tristanseifert/68komputer-hw/cpu-68000/sound.brd

## EAGLE design cpu-68000/sound.brd (2020-02-12)

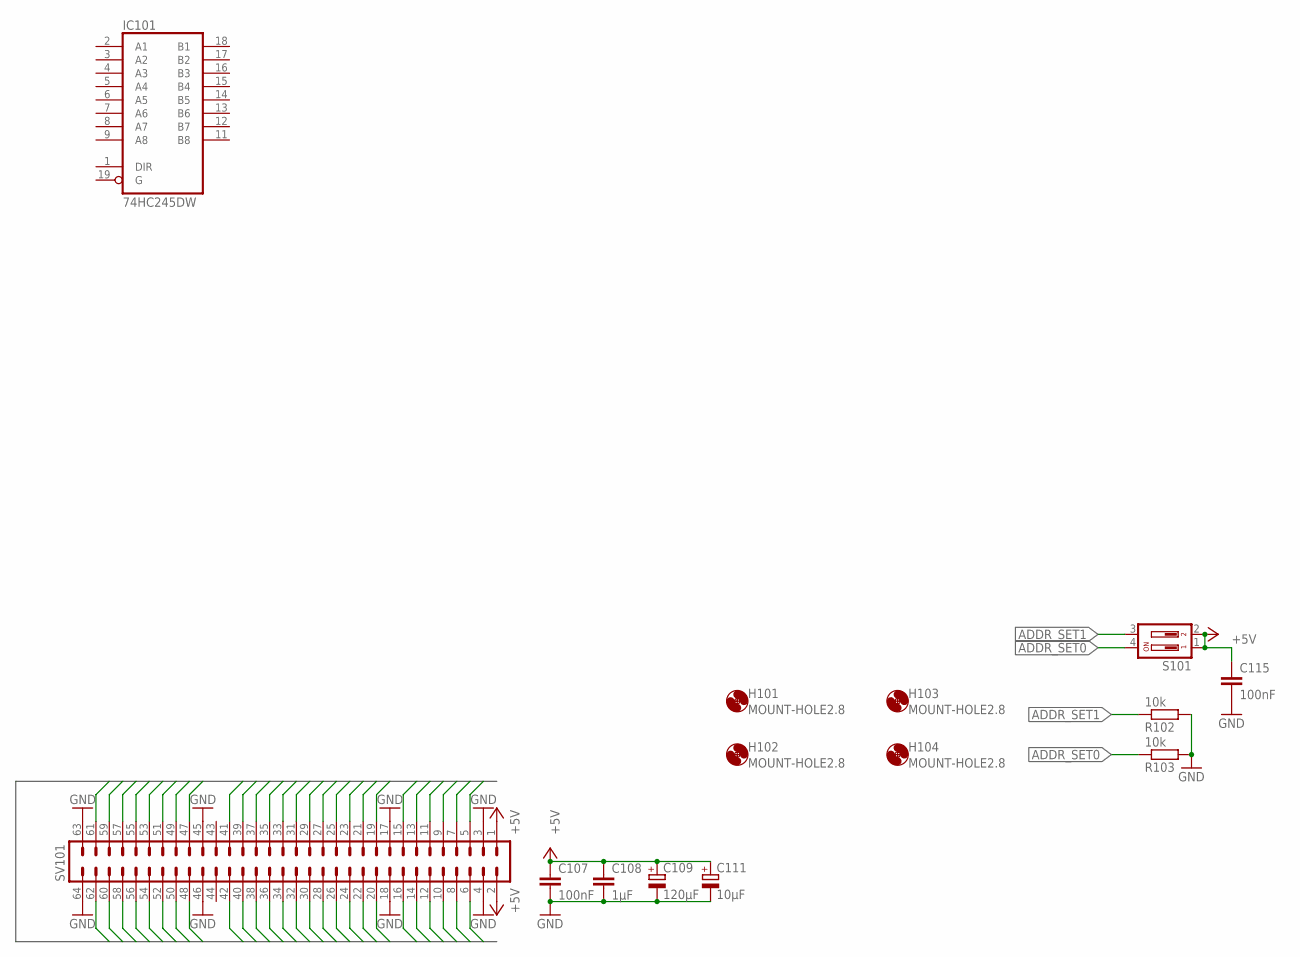
[picture p32: schematic sound.sch, sheet 1, Interface, Address Decoding]

Parts:
C107, C115: 100nF; C0805; MOUSER 710-885012207072
C108: 1µF; C0805; MOUSER 710-885012207078
C109: 120µF; E2,5-7; MOUSER 710-860020373007
C111: 10µF; SMC_B; MOUSER 581-TAJB106K020RNJV
H101, H102, H103, H104: MOUNT-HOLE2.8; 2,8
IC101: 74HC245DW; SO20W; MOUSER 595-SN74HC245DWR
R102, R103: 10k; R2012; MOUSER 652-CR0805FX-1002ELF
S101: DP02; DP-02
SV101: ML64L

Connections:
!AS: SV101.13
!BG: SV101.9
!BGACK: SV101.8
!BR: SV101.7
!DTACK: SV101.10
!EXTI_A: SV101.16
!EXTI_B: SV101.15
!EXT_ID: SV101.41
!HALT: SV101.5
!LDS: SV101.11
!RESET: SV101.6
!UDS: SV101.14
+5V: C107.1, C108.1, C109.+, C111.+, C115.1, S101.1, S101.2, SV101.1, SV101.2; also elsewhere on the board
A1: SV101.20
A2: SV101.22
A3: SV101.19
A4: SV101.24
A5: SV101.21
A6: SV101.23
A7: SV101.26
A8: SV101.25
A9: SV101.28
A10: SV101.27
A11: SV101.30
A12: SV101.29
A13: SV101.31
A14: SV101.32
A15: SV101.33
A16: SV101.34
A17: SV101.36
A18: SV101.35
A19: SV101.38
A20: SV101.37
A21: SV101.40
A22: SV101.39
A23: SV101.42
ADDR_SET0: R103.1, S101.4
ADDR_SET1: R102.1, S101.3
D0: SV101.62
D1: SV101.60
D2: SV101.58
D3: SV101.56
D4: SV101.54
D5: SV101.52
D6: SV101.50
D7: SV101.48
D8: SV101.57
D9: SV101.59
D10: SV101.61
D11: SV101.55
D12: SV101.53
D13: SV101.51
D14: SV101.49
D15: SV101.47
GND: C107.2, C108.2, C109.-, C111.-, C115.2, IC101.10 (GND), R102.2, R103.2, SV101.3, SV101.4, SV101.17, SV101.18, SV101.45, SV101.46, SV101.63, SV101.64; also elsewhere on the board
R/!W!: SV101.12
VCC: IC101.20 (VCC)

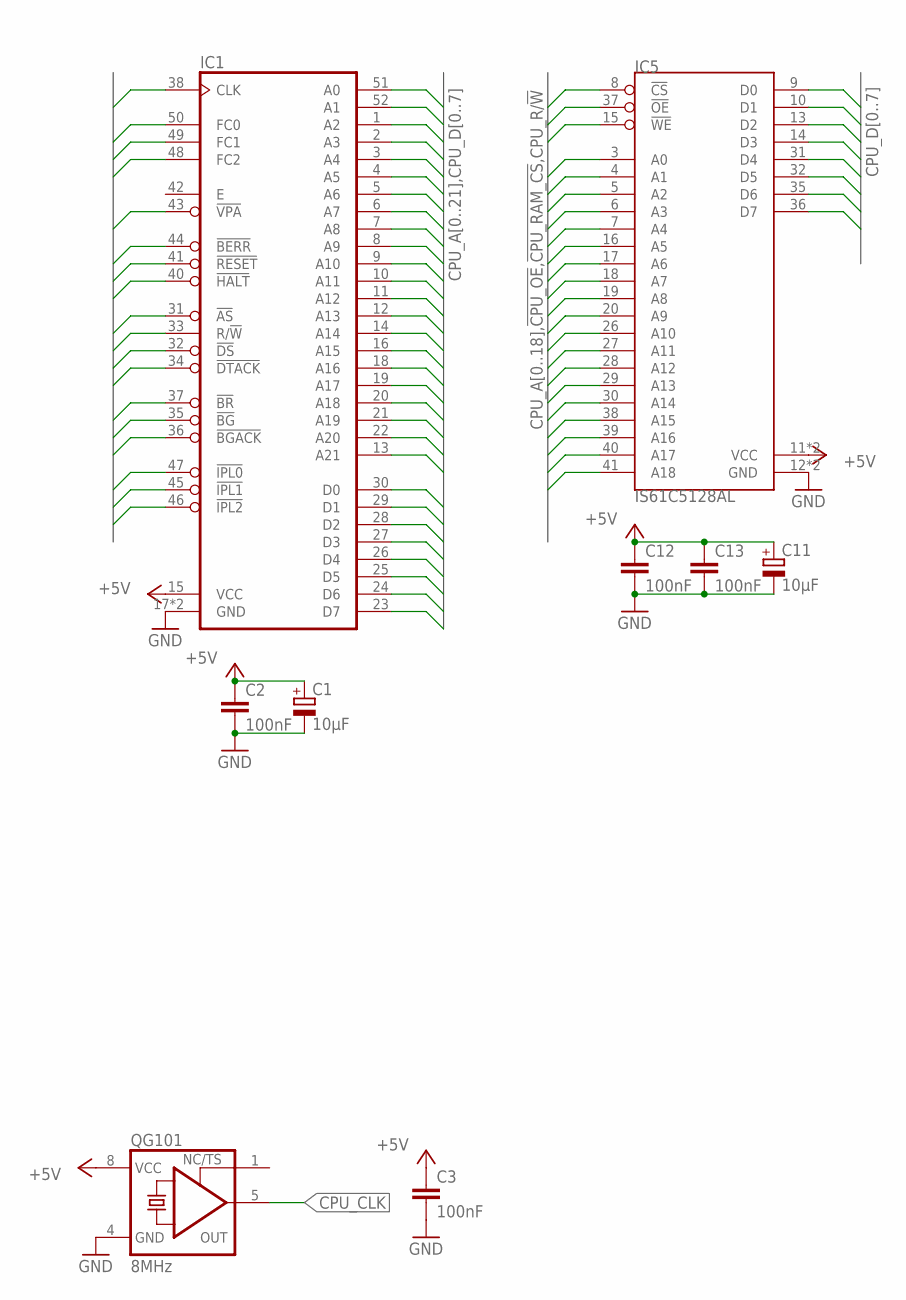
[picture p33: schematic sound.sch, sheet 2, Sound CPU]

Parts:
C1, C11: 10µF; SMC_B; MOUSER 581-TAJB106K020RNJV
C2, C3, C12, C13: 100nF; C0805; MOUSER 710-885012207072
IC1: MC68008-PLCCPLCC52-SOCKET; PLCC52-S
IC5: IS61C5128AL; TSOP44-II
QG101: 8MHz; DIL08S; MOUSER 774-MXO45HS-3C-8.0

Connections:
!CPU_AS: IC1.31 (!AS)
!CPU_BERR: IC1.44 (!BERR)
!CPU_BG: IC1.35 (!BG); also elsewhere on the board
!CPU_BGACK: IC1.36 (!BGACK)
!CPU_BR: IC1.37 (!BR); also elsewhere on the board
!CPU_DS: IC1.32 (!DS)
!CPU_DTACK: IC1.34 (!DTACK)
!CPU_HALT: IC1.40 (!HALT); also elsewhere on the board
!CPU_IPL0: IC1.47 (!IPL0)
!CPU_IPL1: IC1.45 (!IPL1)
!CPU_IPL2: IC1.46 (!IPL2)
!CPU_OE: IC5.37 (!OE)
!CPU_RAM_CS: IC5.8 (!CS)
!CPU_RESET: IC1.41 (!RESET); also elsewhere on the board
!CPU_VPA: IC1.43 (!VPA)
+5V: C1.+, C2.1, C3.1, C11.+, C12.1, C13.1, IC1.15 (VCC), IC5.11 (VCC), IC5.33 (VCC), QG101.8 (VCC); also elsewhere on the board
CPU_A0: IC1.51 (A0), IC5.3 (A0); also elsewhere on the board
CPU_A1: IC1.52 (A1), IC5.4 (A1); also elsewhere on the board
CPU_A2: IC1.1 (A2), IC5.5 (A2); also elsewhere on the board
CPU_A3: IC1.2 (A3), IC5.6 (A3)
CPU_A4: IC1.3 (A4), IC5.7 (A4)
CPU_A5: IC1.4 (A5), IC5.16 (A5)
CPU_A6: IC1.5 (A6), IC5.17 (A6)
CPU_A7: IC1.6 (A7), IC5.18 (A7)
CPU_A8: IC1.7 (A8), IC5.19 (A8)
CPU_A9: IC1.8 (A9), IC5.20 (A9)
CPU_A10: IC1.9 (A10), IC5.26 (A10)
CPU_A11: IC1.10 (A11), IC5.27 (A11)
CPU_A12: IC1.11 (A12), IC5.28 (A12)
CPU_A13: IC1.12 (A13), IC5.29 (A13)
CPU_A14: IC1.14 (A14), IC5.30 (A14)
CPU_A15: IC1.16 (A15), IC5.38 (A15)
CPU_A16: IC1.18 (A16), IC5.39 (A16)
CPU_A17: IC1.19 (A17), IC5.40 (A17)
CPU_A18: IC1.20 (A18), IC5.41 (A18)
CPU_A19: IC1.21 (A19)
CPU_A20: IC1.22 (A20)
CPU_A21: IC1.13 (A21)
CPU_CLK: IC1.38 (CLK), QG101.5 (OUT)
CPU_D0: IC1.30 (D0), IC5.9 (D0); also elsewhere on the board
CPU_D1: IC1.29 (D1), IC5.10 (D1); also elsewhere on the board
CPU_D2: IC1.28 (D2), IC5.13 (D2); also elsewhere on the board
CPU_D3: IC1.27 (D3), IC5.14 (D3); also elsewhere on the board
CPU_D4: IC1.26 (D4), IC5.31 (D4); also elsewhere on the board
CPU_D5: IC1.25 (D5), IC5.32 (D5); also elsewhere on the board
CPU_D6: IC1.24 (D6), IC5.35 (D6); also elsewhere on the board
CPU_D7: IC1.23 (D7), IC5.36 (D7); also elsewhere on the board
CPU_FC0: IC1.50 (FC0)
CPU_FC1: IC1.49 (FC1)
CPU_FC2: IC1.48 (FC2)
CPU_R/!W!: IC1.33 (R/!W), IC5.15 (!WE); also elsewhere on the board
GND: C1.-, C2.2, C3.2, C11.-, C12.2, C13.2, IC1.17 (GND), IC1.39 (GND), IC5.12 (GND), IC5.34 (GND), QG101.4 (GND); also elsewhere on the board

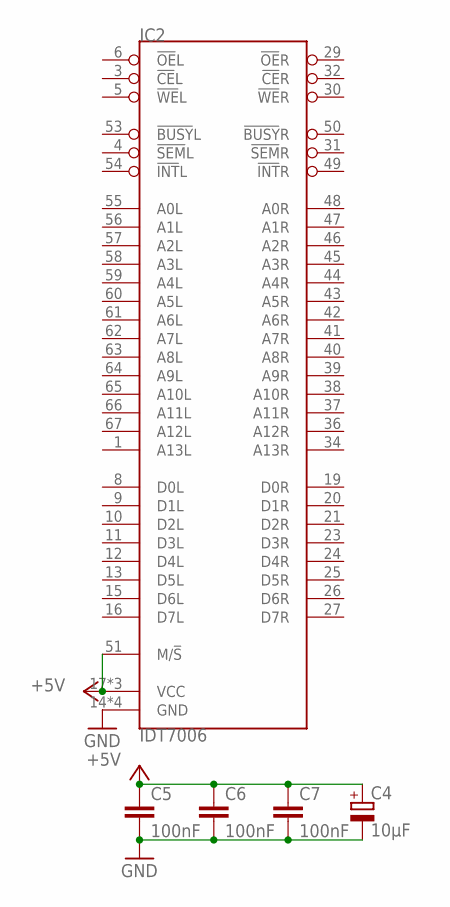
[picture p34: schematic sound.sch, sheet 4, Sound CPU / Host IF]

Parts:
C4: 10µF; SMC_B; MOUSER 581-TAJB106K020RNJV
C5, C6, C7: 100nF; C0805; MOUSER 710-885012207072
IC2: IDT7006; PLCC68-S

Connections:
+5V: C4.+, C5.1, C6.1, C7.1, IC2.17 (VCC), IC2.22 (VCC), IC2.51 (M/!S!), IC2.68 (VCC); also elsewhere on the board
GND: C4.-, C5.2, C6.2, C7.2, IC2.14 (GND), IC2.18 (GND), IC2.35 (GND), IC2.52 (GND); also elsewhere on the board

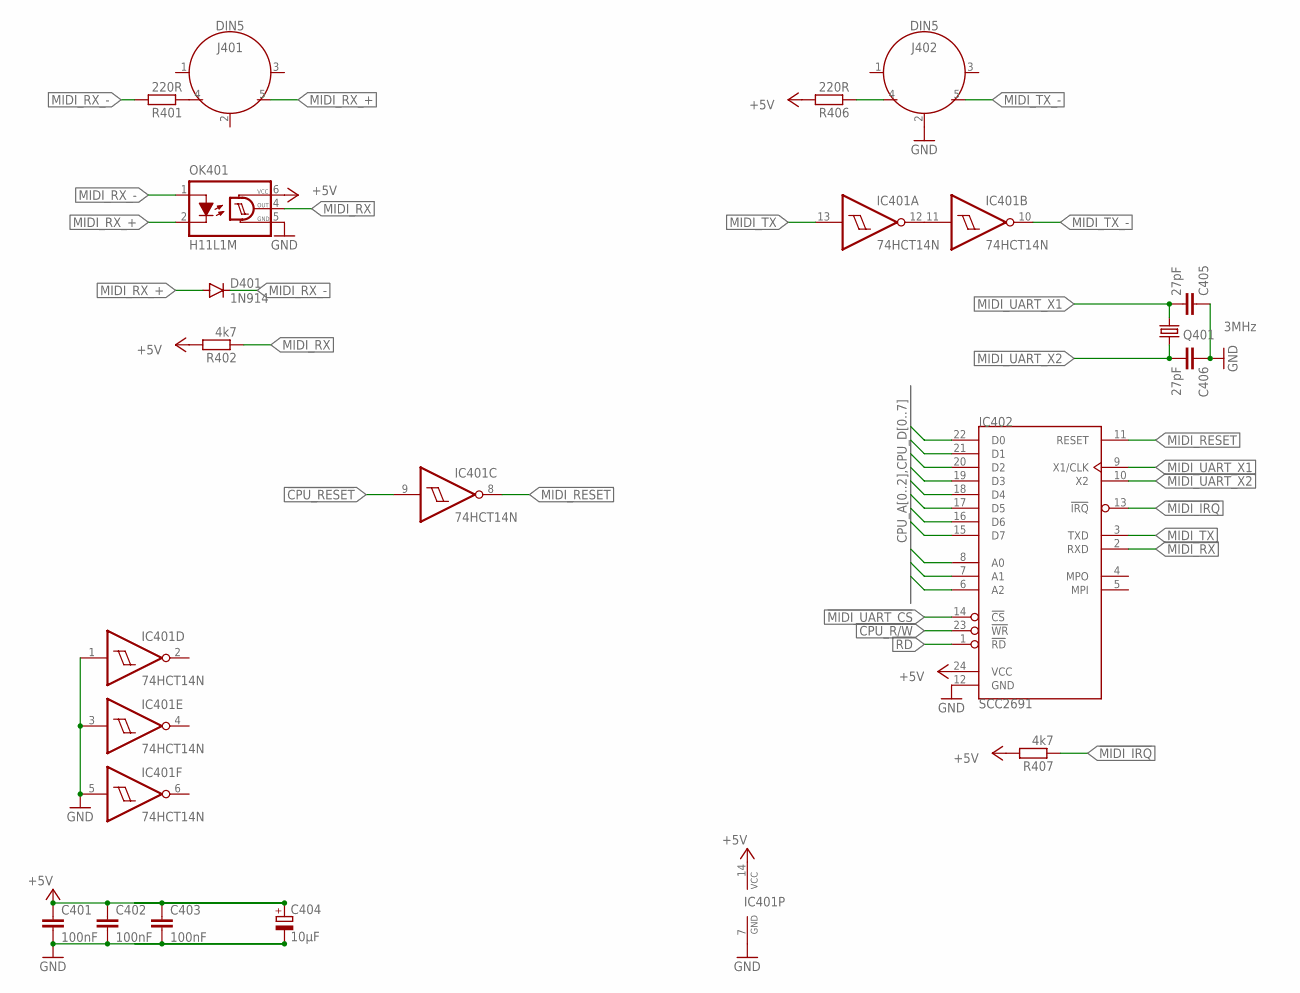
[picture p35: schematic sound.sch, sheet 7, MIDI IF]

Parts:
C401, C402, C403: 100nF; C0805; MOUSER 710-885012207072
C404: 10µF; SMC_B; MOUSER 581-TAJB106K020RNJV
C405, C406: 27pF; C0805; MOUSER 80-C0805C270K5HACTU
D401: 1N914; DO35-10; MOUSER 512-1N914TR
IC401: 74HCT14N; DIL14; MOUSER 595-SN74HCT14N
IC402: SCC2691; DIL24S; MOUSER_SOCKET 575-11044324
J401, J402: DIN5; DIN5-RA-PTH; MOUSER 806-KCDX-5S-N
OK401: H11L1M; DIL06; MOUSER 512-H11L1M
Q401: 3MHz; HC49/S; MOUSER 520-HCA300-SX
R401, R406: 220R; R2012; MOUSER 652-CR0805FX-2200ELF
R402, R407: 4k7; R2012; MOUSER 652-CR0805FX-4701ELF

Connections:
!CPU_RESET: IC401.9 (I); also elsewhere on the board
!MIDI_IRQ: IC402.13 (!IRQ), R407.1; also elsewhere on the board
!MIDI_UART_CS: IC402.14 (!CS)
!RD: IC402.1 (!RD)
+5V: C401.1, C402.1, C403.1, C404.+, IC401.14 (VCC), IC402.24 (VCC), OK401.6 (VCC), R402.2, R406.2, R407.2; also elsewhere on the board
CPU_A0: IC402.8 (A0); also elsewhere on the board
CPU_A1: IC402.7 (A1); also elsewhere on the board
CPU_A2: IC402.6 (A2); also elsewhere on the board
CPU_D0: IC402.22 (D0); also elsewhere on the board
CPU_D1: IC402.21 (D1); also elsewhere on the board
CPU_D2: IC402.20 (D2); also elsewhere on the board
CPU_D3: IC402.19 (D3); also elsewhere on the board
CPU_D4: IC402.18 (D4); also elsewhere on the board
CPU_D5: IC402.17 (D5); also elsewhere on the board
CPU_D6: IC402.16 (D6); also elsewhere on the board
CPU_D7: IC402.15 (D7); also elsewhere on the board
CPU_R/!W!: IC402.23 (!WR); also elsewhere on the board
GND: C401.2, C402.2, C403.2, C404.-, C405.1, C406.1, IC401.1 (I), IC401.3 (I), IC401.5 (I), IC401.7 (GND), IC402.12 (GND), J402.2, OK401.5 (GND); also elsewhere on the board
MIDI_RESET: IC401.8 (O), IC402.11 (RESET)
MIDI_RX: IC402.2 (RXD), OK401.4 (OUT), R402.1; also elsewhere on the board
MIDI_RX_+: D401.A, J401.5, OK401.2 (C)
MIDI_RX_-: D401.C, OK401.1 (A), R401.2
MIDI_TX: IC401.13 (I), IC402.3 (TXD); also elsewhere on the board
MIDI_TX_-: IC401.10 (O), J402.5
MIDI_UART_X1: C405.2, IC402.9 (X1/CLK), Q401.1
MIDI_UART_X2: C406.2, IC402.10 (X2), Q401.2
unnamed: J401.4, R401.1
unnamed: IC401.11 (I), IC401.12 (O)
unnamed: J402.4, R406.1

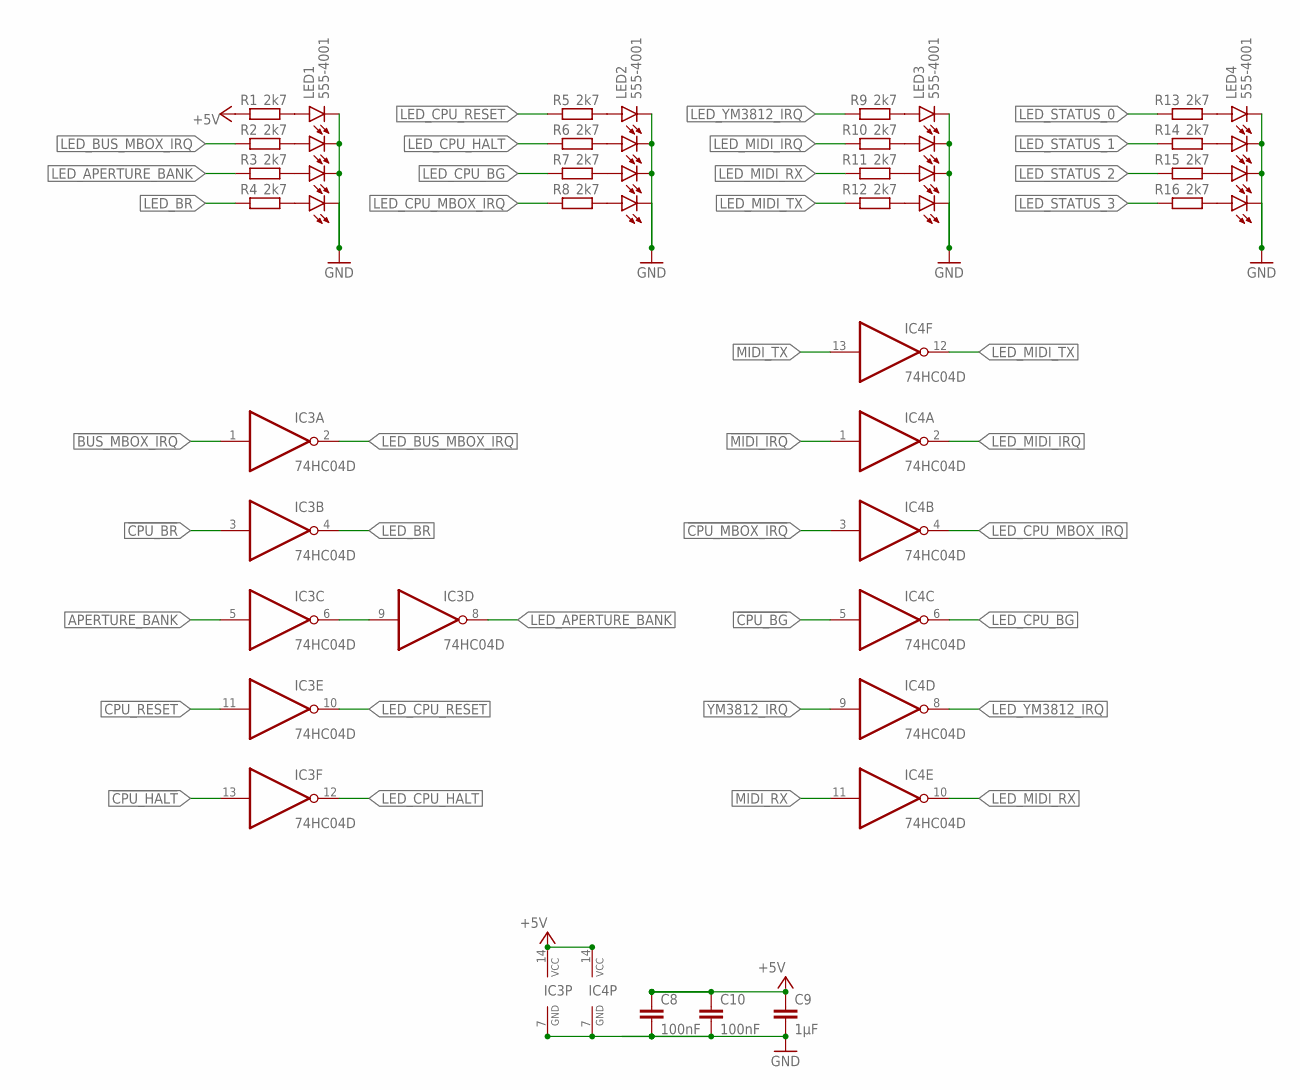
[picture p36: schematic sound.sch, sheet 8, Blinkenlights]

Parts:
C8, C10: 100nF; C0805; MOUSER 710-885012207072
C9: 1µF; C0805; MOUSER 710-885012207078
IC3, IC4: 74HC04D; SO14
LED1, LED2, LED3, LED4: 555-4001
R1, R2, R3, R4, R5, R6, R7, R8, R9, R10, R11, R12, R13, R14, R15, R16: 2k7; R2012; MOUSER 652-CR0805FX-2701ELF

Connections:
!BUS_MBOX_IRQ: IC3.1 (I)
!CPU_BG: IC4.5 (I); also elsewhere on the board
!CPU_BR: IC3.3 (I); also elsewhere on the board
!CPU_HALT: IC3.13 (I); also elsewhere on the board
!CPU_MBOX_IRQ: IC4.3 (I)
!CPU_RESET: IC3.11 (I); also elsewhere on the board
!MIDI_IRQ: IC4.1 (I); also elsewhere on the board
!YM3812_IRQ: IC4.9 (I)
+5V: C8.1, C9.1, C10.1, IC3.14 (VCC), IC4.14 (VCC), R1.2; also elsewhere on the board
APERTURE_BANK: IC3.5 (I)
GND: C8.2, C9.2, C10.2, IC3.7 (GND), IC4.7 (GND), LED1.K1, LED1.K2, LED1.K3, LED1.K4, LED2.K1, LED2.K2, LED2.K3, LED2.K4, LED3.K1, LED3.K2, LED3.K3, LED3.K4, LED4.K1, LED4.K2, LED4.K3, LED4.K4; also elsewhere on the board
LED_APERTURE_BANK: IC3.8 (O), R3.2
LED_BR: IC3.4 (O), R4.2
LED_BUS_MBOX_IRQ: IC3.2 (O), R2.2
LED_CPU_BG: IC4.6 (O), R7.2
LED_CPU_HALT: IC3.12 (O), R6.2
LED_CPU_MBOX_IRQ: IC4.4 (O), R8.2
LED_CPU_RESET: IC3.10 (O), R5.2
LED_MIDI_IRQ: IC4.2 (O), R10.2
LED_MIDI_RX: IC4.10 (O), R11.2
LED_MIDI_TX: IC4.12 (O), R12.2
LED_STATUS_0: R13.2
LED_STATUS_1: R14.2
LED_STATUS_2: R15.2
LED_STATUS_3: R16.2
LED_YM3812_IRQ: IC4.8 (O), R9.2
MIDI_RX: IC4.11 (I); also elsewhere on the board
MIDI_TX: IC4.13 (I); also elsewhere on the board
unnamed: LED1.A4, R1.1
unnamed: LED1.A3, R2.1
unnamed: LED1.A2, R3.1
unnamed: LED1.A1, R4.1
unnamed: LED2.A4, R5.1
unnamed: LED2.A3, R6.1
unnamed: IC3.6 (O), IC3.9 (I)
unnamed: LED2.A2, R7.1
unnamed: LED2.A1, R8.1
unnamed: LED3.A4, R9.1
unnamed: LED3.A3, R10.1
unnamed: LED3.A2, R11.1
unnamed: LED3.A1, R12.1
unnamed: LED4.A4, R13.1
unnamed: LED4.A3, R14.1
unnamed: LED4.A2, R15.1
unnamed: LED4.A1, R16.1

Board: 2 copper layers, 70 parts (3 on the bottom side), 77 nets, no tracks yet.
