tristanseifert/68komputer-hw/cpu-68000/cpu-68000.brd

## EAGLE design cpu-68000/cpu-68000.brd (2019-11-22)

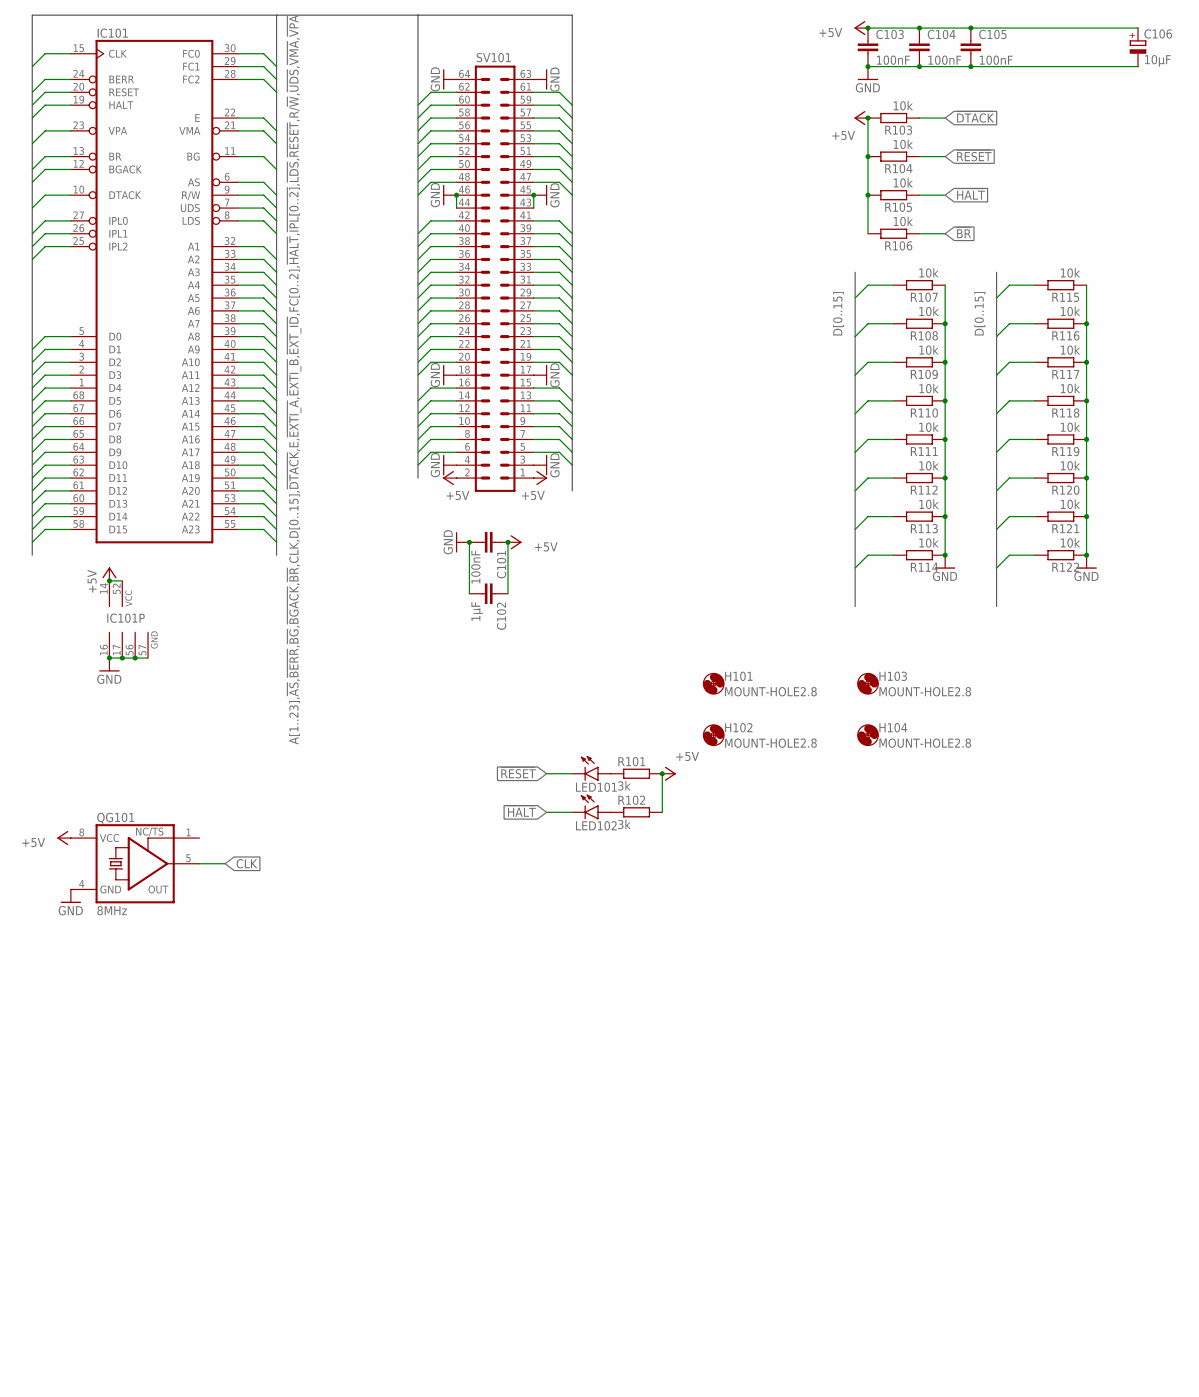
[picture p37: schematic cpu-68000.sch, sheet 1, CPU]

Parts:
C101, C103, C104, C105: 100nF; C0805; MOUSER 710-885012207072
C102: 1µF; C0805; MOUSER 710-885012207078
C106: 10µF; SMC_B; MOUSER 581-TAJB106K020RNJV
H101, H102, H103, H104: MOUNT-HOLE2.8; 2,8
IC101: MC68000FN-SOC; PLCC68SOCK; MOUSER_SOCKET 940-44-068-24-000000
LED101, LED102: LEDCHIPLED_1206; CHIPLED_1206; MOUSER 710-156120RS75300
QG101: 8MHz; DIL08S; MOUSER 774-MXO45HS-3C-8.0
R101, R102: 3k; R2012; MOUSER 652-CR0805JW-302ELF
R103, R104, R105, R106, R107, R108, R109, R110, R111, R112, R113, R114, R115, R116, R117, R118, R119, R120, R121, R122: 10k; R2012; MOUSER 652-CR0805FX-1002ELF
SV101: ML64L

Connections:
!AS: IC101.6 (AS), SV101.13; also elsewhere on the board
!BERR: IC101.24 (BERR); also elsewhere on the board
!BG: IC101.11 (BG), SV101.9
!BGACK: IC101.12 (BGACK), SV101.8
!BR: IC101.13 (BR), R106.1, SV101.7
!DTACK: IC101.10 (DTACK), R103.1, SV101.10; also elsewhere on the board
!EXTI_A: SV101.16; also elsewhere on the board
!EXTI_B: SV101.15; also elsewhere on the board
!EXT_ID: SV101.41; also elsewhere on the board
!HALT: IC101.19 (HALT), LED102.C, R105.1, SV101.5; also elsewhere on the board
!IPL0: IC101.27 (IPL0); also elsewhere on the board
!IPL1: IC101.26 (IPL1); also elsewhere on the board
!IPL2: IC101.25 (IPL2); also elsewhere on the board
!LDS: IC101.8 (LDS), SV101.11; also elsewhere on the board
!RESET: IC101.20 (RESET), LED101.C, R104.1, SV101.6; also elsewhere on the board
!UDS: IC101.7 (UDS), SV101.14; also elsewhere on the board
!VMA: IC101.21 (VMA)
!VPA: IC101.23 (VPA); also elsewhere on the board
+5V: C101.1, C102.1, C103.1, C104.1, C105.1, C106.+, IC101.14 (VCC), IC101.52 (VCC), QG101.8 (VCC), R101.2, R102.2, R103.2, R104.2, R105.2, R106.2, SV101.1, SV101.2; also elsewhere on the board
A1: IC101.32 (A1), SV101.20; also elsewhere on the board
A2: IC101.33 (A2), SV101.22; also elsewhere on the board
A3: IC101.34 (A3), SV101.19; also elsewhere on the board
A4: IC101.35 (A4), SV101.24; also elsewhere on the board
A5: IC101.36 (A5), SV101.21; also elsewhere on the board
A6: IC101.37 (A6), SV101.23; also elsewhere on the board
A7: IC101.38 (A7), SV101.26; also elsewhere on the board
A8: IC101.39 (A8), SV101.25; also elsewhere on the board
A9: IC101.40 (A9), SV101.28; also elsewhere on the board
A10: IC101.41 (A10), SV101.27; also elsewhere on the board
A11: IC101.42 (A11), SV101.30; also elsewhere on the board
A12: IC101.43 (A12), SV101.29; also elsewhere on the board
A13: IC101.44 (A13), SV101.31; also elsewhere on the board
A14: IC101.45 (A14), SV101.32; also elsewhere on the board
A15: IC101.46 (A15), SV101.33; also elsewhere on the board
A16: IC101.47 (A16), SV101.34; also elsewhere on the board
A17: IC101.48 (A17), SV101.36; also elsewhere on the board
A18: IC101.49 (A18), SV101.35; also elsewhere on the board
A19: IC101.50 (A19), SV101.38; also elsewhere on the board
A20: IC101.51 (A20), SV101.37; also elsewhere on the board
A21: IC101.53 (A21), SV101.40; also elsewhere on the board
A22: IC101.54 (A22), SV101.39; also elsewhere on the board
A23: IC101.55 (A23), SV101.42; also elsewhere on the board
CLK: IC101.15 (CLK), QG101.5 (OUT); also elsewhere on the board
D0: IC101.5 (D0), R107.2, SV101.62; also elsewhere on the board
D1: IC101.4 (D1), R108.2, SV101.60; also elsewhere on the board
D2: IC101.3 (D2), R109.2, SV101.58; also elsewhere on the board
D3: IC101.2 (D3), R110.2, SV101.56; also elsewhere on the board
D4: IC101.1 (D4), R111.2, SV101.54; also elsewhere on the board
D5: IC101.68 (D5), R112.2, SV101.52; also elsewhere on the board
D6: IC101.67 (D6), R113.2, SV101.50; also elsewhere on the board
D7: IC101.66 (D7), R114.2, SV101.48; also elsewhere on the board
D8: IC101.65 (D8), R115.2, SV101.57; also elsewhere on the board
D9: IC101.64 (D9), R116.2, SV101.59; also elsewhere on the board
D10: IC101.63 (D10), R117.2, SV101.61; also elsewhere on the board
D11: IC101.62 (D11), R118.2, SV101.55; also elsewhere on the board
D12: IC101.61 (D12), R119.2, SV101.53; also elsewhere on the board
D13: IC101.60 (D13), R120.2, SV101.51; also elsewhere on the board
D14: IC101.59 (D14), R121.2, SV101.49; also elsewhere on the board
D15: IC101.58 (D15), R122.2, SV101.47; also elsewhere on the board
E: IC101.22 (E); also elsewhere on the board
FC0: IC101.30 (FC0); also elsewhere on the board
FC1: IC101.29 (FC1); also elsewhere on the board
FC2: IC101.28 (FC2); also elsewhere on the board
GND: C101.2, C102.2, C103.2, C104.2, C105.2, C106.-, IC101.16 (GND), IC101.17 (GND), IC101.56 (GND), IC101.57 (GND), QG101.4 (GND), R107.1, R108.1, R109.1, R110.1, R111.1, R112.1, R113.1, R114.1, R115.1, R116.1, R117.1, R118.1, R119.1, R120.1, R121.1, R122.1, SV101.3, SV101.4, SV101.17, SV101.18, SV101.43, SV101.44, SV101.45, SV101.46, SV101.63, SV101.64; also elsewhere on the board
unnamed: LED101.A, R101.1
unnamed: LED102.A, R102.1
R/!W!: IC101.9 (R/W), SV101.12; also elsewhere on the board

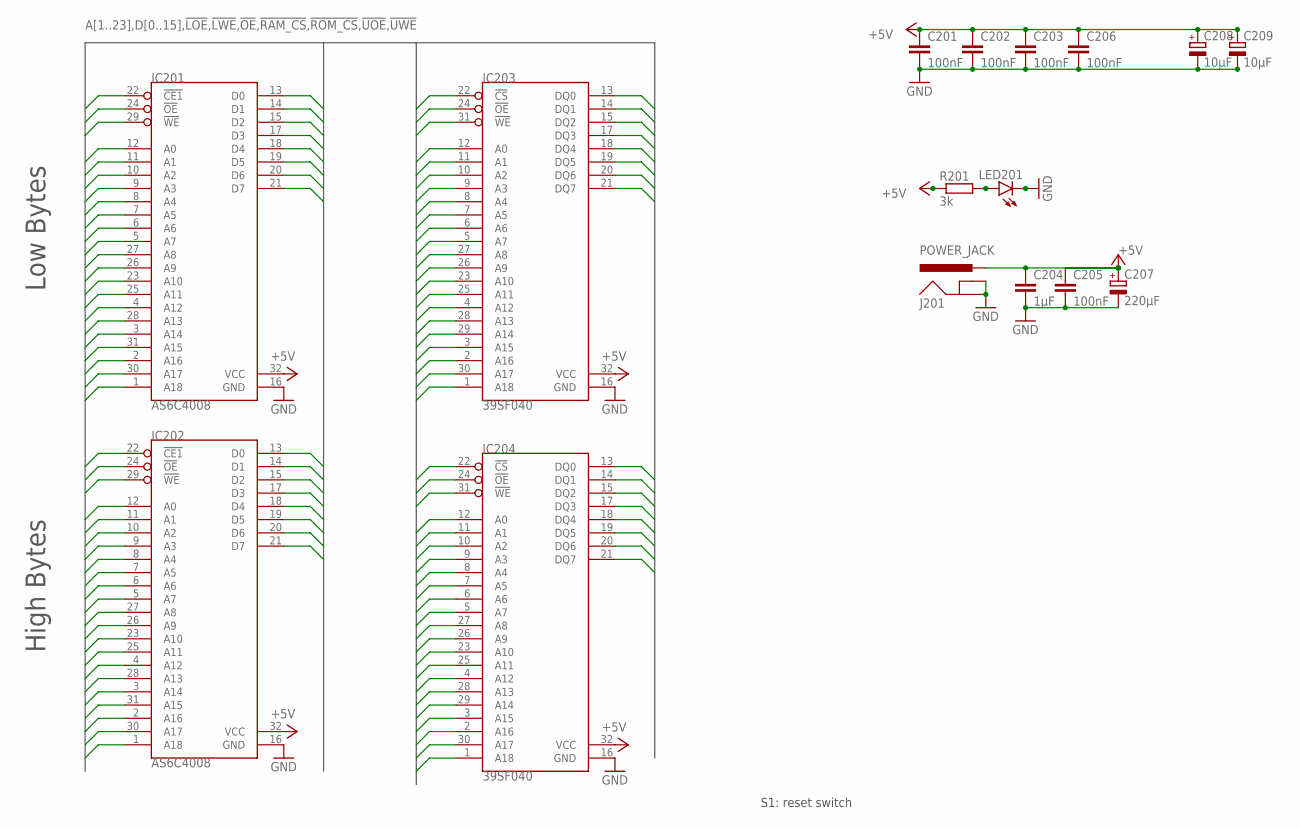
[picture p38: schematic cpu-68000.sch, sheet 2, RAM, ROM]

Parts:
C201, C202, C203, C205, C206: 100nF; C0805; MOUSER 710-885012207072
C204: 1µF; C0805; MOUSER 710-885012107015
C207: 220µF; E2,5-7; MOUSER 710-860020373010
C208, C209: 10µF; SMC_B; MOUSER 581-TAJB106K020RNJV
IC201, IC202: AS6C4008; DIL32; MOUSER_SOCKET 575-1144632
IC203, IC204: 39SF040; DIL32; MOUSER 804-39SF0407CPHE
J201: POWER_JACK; POWER_JACK_PTH
LED201: LEDCHIPLED_1206; CHIPLED_1206; MOUSER 710-156120YS75300
R201: 3k; R2012; MOUSER 652-CR0805JW-302ELF

Connections:
!LOE: IC201.24 (!OE), IC203.24 (!OE); also elsewhere on the board
!LWE: IC201.29 (!WE), IC203.31 (!WE); also elsewhere on the board
!RAM_CS: IC201.22 (!CE1), IC202.22 (!CE1); also elsewhere on the board
!ROM_CS: IC203.22 (!CS), IC204.22 (!CS); also elsewhere on the board
!UOE: IC202.24 (!OE), IC204.24 (!OE); also elsewhere on the board
!UWE: IC202.29 (!WE), IC204.31 (!WE); also elsewhere on the board
+5V: C201.1, C202.1, C203.1, C204.1, C205.1, C206.1, C207.+, C208.+, C209.+, IC201.32 (VCC), IC202.32 (VCC), IC203.32 (VCC), IC204.32 (VCC), J201.PWR, R201.1; also elsewhere on the board
A1: IC201.12 (A0), IC202.12 (A0), IC203.12 (A0), IC204.12 (A0); also elsewhere on the board
A2: IC201.11 (A1), IC202.11 (A1), IC203.11 (A1), IC204.11 (A1); also elsewhere on the board
A3: IC201.10 (A2), IC202.10 (A2), IC203.10 (A2), IC204.10 (A2); also elsewhere on the board
A4: IC201.9 (A3), IC202.9 (A3), IC203.9 (A3), IC204.9 (A3); also elsewhere on the board
A5: IC201.8 (A4), IC202.8 (A4), IC203.8 (A4), IC204.8 (A4); also elsewhere on the board
A6: IC201.7 (A5), IC202.7 (A5), IC203.7 (A5), IC204.7 (A5); also elsewhere on the board
A7: IC201.6 (A6), IC202.6 (A6), IC203.6 (A6), IC204.6 (A6); also elsewhere on the board
A8: IC201.5 (A7), IC202.5 (A7), IC203.5 (A7), IC204.5 (A7); also elsewhere on the board
A9: IC201.27 (A8), IC202.27 (A8), IC203.27 (A8), IC204.27 (A8); also elsewhere on the board
A10: IC201.26 (A9), IC202.26 (A9), IC203.26 (A9), IC204.26 (A9); also elsewhere on the board
A11: IC201.23 (A10), IC202.23 (A10), IC203.23 (A10), IC204.23 (A10); also elsewhere on the board
A12: IC201.25 (A11), IC202.25 (A11), IC203.25 (A11), IC204.25 (A11); also elsewhere on the board
A13: IC201.4 (A12), IC202.4 (A12), IC203.4 (A12), IC204.4 (A12); also elsewhere on the board
A14: IC201.28 (A13), IC202.28 (A13), IC203.28 (A13), IC204.28 (A13); also elsewhere on the board
A15: IC201.3 (A14), IC202.3 (A14), IC203.29 (A14), IC204.29 (A14); also elsewhere on the board
A16: IC201.31 (A15), IC202.31 (A15), IC203.3 (A15), IC204.3 (A15); also elsewhere on the board
A17: IC201.2 (A16), IC202.2 (A16), IC203.2 (A16), IC204.2 (A16); also elsewhere on the board
A18: IC201.30 (A17), IC202.30 (A17), IC203.30 (A17), IC204.30 (A17); also elsewhere on the board
A19: IC201.1 (A18), IC202.1 (A18), IC203.1 (A18), IC204.1 (A18); also elsewhere on the board
D0: IC201.13 (D0), IC203.13 (DQ0); also elsewhere on the board
D1: IC201.14 (D1), IC203.14 (DQ1); also elsewhere on the board
D2: IC201.15 (D2), IC203.15 (DQ2); also elsewhere on the board
D3: IC201.17 (D3), IC203.17 (DQ3); also elsewhere on the board
D4: IC201.18 (D4), IC203.18 (DQ4); also elsewhere on the board
D5: IC201.19 (D5), IC203.19 (DQ5); also elsewhere on the board
D6: IC201.20 (D6), IC203.20 (DQ6); also elsewhere on the board
D7: IC201.21 (D7), IC203.21 (DQ7); also elsewhere on the board
D8: IC202.13 (D0), IC204.13 (DQ0); also elsewhere on the board
D9: IC202.14 (D1), IC204.14 (DQ1); also elsewhere on the board
D10: IC202.15 (D2), IC204.15 (DQ2); also elsewhere on the board
D11: IC202.17 (D3), IC204.17 (DQ3); also elsewhere on the board
D12: IC202.18 (D4), IC204.18 (DQ4); also elsewhere on the board
D13: IC202.19 (D5), IC204.19 (DQ5); also elsewhere on the board
D14: IC202.20 (D6), IC204.20 (DQ6); also elsewhere on the board
D15: IC202.21 (D7), IC204.21 (DQ7); also elsewhere on the board
GND: C201.2, C202.2, C203.2, C204.2, C205.2, C206.2, C207.-, C208.-, C209.-, IC201.16 (GND), IC202.16 (GND), IC203.16 (GND), IC204.16 (GND), J201.GND, J201.GNDBREAK, LED201.C; also elsewhere on the board
unnamed: LED201.A, R201.2

Notes on the sheet:
S1: reset switch
Low Bytes
High Bytes
