tristanseifert/68komputer-hw/cpu-68000/cpu-68000.brd

## EAGLE design cpu-68000/cpu-68000.brd (continued)

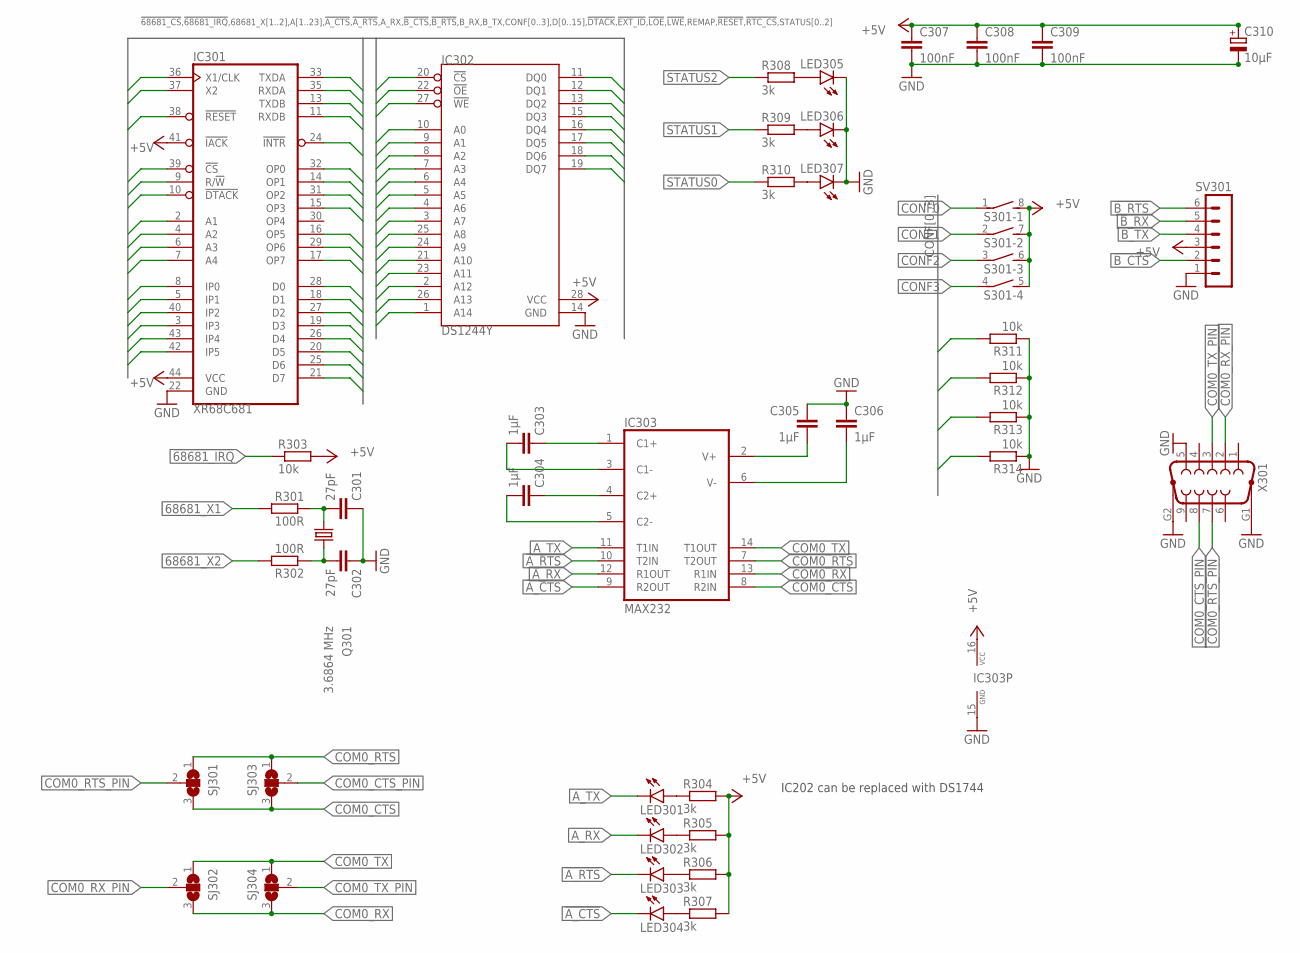
[picture p39: schematic cpu-68000.sch, sheet 3, Peripherals (DUART, RTC)]

Parts:
C301, C302: 27pF; C0805; MOUSER 80-C0805C270K5HACTU
C303, C304, C305, C306: 1µF; C0805; MOUSER 710-885012207078
C307, C308, C309: 100nF; C0805; MOUSER 710-885012207072
C310: 10µF; SMC_B; MOUSER 581-TAJB106K020RNJV
IC301: XR68C681; PLCC-S44; MOUSER 701-XR68C681CJ-F
IC302: DS1244Y; DIL28-6; MOUSER_SOCKET 575-1104762841001000
IC303: MAX232; DIL16; MOUSER 595-MAX232ECN
LED301, LED302, LED303, LED304, LED305, LED306, LED307: LEDCHIPLED_1206; CHIPLED_1206; MOUSER 710-156120VS75300
Q301: 3.6864 MHz; HC49/S; MOUSER 815-ABL-3.6864-B2
R301, R302: 100R; R2012; MOUSER 652-CR0805FX-1000ELF
R303, R311, R312, R313, R314: 10k; R2012; MOUSER 652-CR0805FX-1002ELF
R304, R305, R306, R307, R308, R309, R310: 3k; R2012; MOUSER 652-CR0805JW-302ELF
S301: DIP04S; MOUSER 653-A6FR-4104
SJ301, SJ302, SJ303, SJ304: SJ2WW; SJ_2W
SV301: MA06-1
X301: F09HP; MOUSER 806-K22X-E9P-N-99

Connections:
68681_X1: IC301.36 (X1/CLK), R301.2
68681_X2: IC301.37 (X2), R302.2
!68681_CS: IC301.39 (!CS); also elsewhere on the board
!68681_IRQ: IC301.24 (!INTR), R303.1; also elsewhere on the board
!A_CTS: IC301.8 (IP0), IC303.9 (R2OUT), LED304.C
!A_RTS: IC301.32 (OP0), IC303.10 (T2IN), LED303.C
!B_CTS: IC301.5 (IP1), SV301.2
!B_RTS: IC301.14 (OP1), SV301.6
!DTACK: IC301.10 (!DTACK); also elsewhere on the board
!EXT_ID: IC301.29 (OP6); also elsewhere on the board
!LOE: IC302.22 (!OE); also elsewhere on the board
!LWE: IC301.9 (R/!W), IC302.27 (!WE); also elsewhere on the board
!RESET: IC301.38 (!RESET); also elsewhere on the board
!RTC_CS: IC302.20 (!CS); also elsewhere on the board
+5V: C307.1, C308.1, C309.1, C310.+, IC301.41 (!IACK), IC301.44 (VCC), IC302.28 (VCC), IC303.16 (VCC), R303.2, R304.2, R305.2, R306.2, R307.2, S301.5 (2), S301.6 (2), S301.7 (2), S301.8 (2), SV301.3; also elsewhere on the board
A1: IC301.2 (A1), IC302.10 (A0); also elsewhere on the board
A2: IC301.4 (A2), IC302.9 (A1); also elsewhere on the board
A3: IC301.6 (A3), IC302.8 (A2); also elsewhere on the board
A4: IC301.7 (A4), IC302.7 (A3); also elsewhere on the board
A5: IC302.6 (A4); also elsewhere on the board
A6: IC302.5 (A5); also elsewhere on the board
A7: IC302.4 (A6); also elsewhere on the board
A8: IC302.3 (A7); also elsewhere on the board
A9: IC302.25 (A8); also elsewhere on the board
A10: IC302.24 (A9); also elsewhere on the board
A11: IC302.21 (A10); also elsewhere on the board
A12: IC302.23 (A11); also elsewhere on the board
A13: IC302.2 (A12); also elsewhere on the board
A14: IC302.26 (A13); also elsewhere on the board
A15: IC302.1 (A14); also elsewhere on the board
A_RX: IC301.35 (RXDA), IC303.12 (R1OUT), LED302.C
A_TX: IC301.33 (TXDA), IC303.11 (T1IN), LED301.C
B_RX: IC301.11 (RXDB), SV301.5
B_TX: IC301.13 (TXDB), SV301.4
COM0_CTS: IC303.8 (R2IN), SJ301.3, SJ303.3
COM0_CTS_PIN: SJ303.2, X301.8
COM0_RTS: IC303.7 (T2OUT), SJ301.1, SJ303.1
COM0_RTS_PIN: SJ301.2, X301.7
COM0_RX: IC303.13 (R1IN), SJ302.3, SJ304.3
COM0_RX_PIN: SJ302.2, X301.2
COM0_TX: IC303.14 (T1OUT), SJ302.1, SJ304.1
COM0_TX_PIN: SJ304.2, X301.3
CONF0: IC301.40 (IP2), R311.2, S301.1
CONF1: IC301.43 (IP4), R312.2, S301.2 (1)
CONF2: IC301.42 (IP5), R313.2, S301.3 (1)
CONF3: IC301.3 (IP3), R314.2, S301.4 (1)
D0: IC301.28 (D0), IC302.11 (DQ0); also elsewhere on the board
D1: IC301.18 (D1), IC302.12 (DQ1); also elsewhere on the board
D2: IC301.27 (D2), IC302.13 (DQ2); also elsewhere on the board
D3: IC301.19 (D3), IC302.15 (DQ3); also elsewhere on the board
D4: IC301.26 (D4), IC302.16 (DQ4); also elsewhere on the board
D5: IC301.20 (D5), IC302.17 (DQ5); also elsewhere on the board
D6: IC301.25 (D6), IC302.18 (DQ6); also elsewhere on the board
D7: IC301.21 (D7), IC302.19 (DQ7); also elsewhere on the board
GND: C301.1, C302.1, C305.1, C306.1, C307.2, C308.2, C309.2, C310.-, IC301.22 (GND), IC302.14 (GND), IC303.15 (GND), LED305.C, LED306.C, LED307.C, R311.1, R312.1, R313.1, R314.1, SV301.1, X301.5, X301.G1, X301.G2; also elsewhere on the board
unnamed: C305.2, IC303.2 (V+)
unnamed: C301.2, Q301.1, R301.1
unnamed: C302.2, Q301.2, R302.1
unnamed: LED306.A, R309.2
unnamed: LED307.A, R310.2
unnamed: LED305.A, R308.2
unnamed: LED301.A, R304.1
unnamed: LED302.A, R305.1
unnamed: LED303.A, R306.1
unnamed: LED304.A, R307.1
unnamed: C306.2, IC303.6 (V-)
unnamed: C304.1, IC303.4 (C2+)
unnamed: C303.1, IC303.1 (C1+)
unnamed: C303.2, IC303.3 (C1-)
unnamed: C304.2, IC303.5 (C2-)
REMAP: IC301.31 (OP2); also elsewhere on the board
STATUS0: IC301.16 (OP5), R310.1
STATUS1: IC301.17 (OP7), R309.1
STATUS2: IC301.15 (OP3), R308.1

Notes on the sheet:
IC202 can be replaced with DS1744

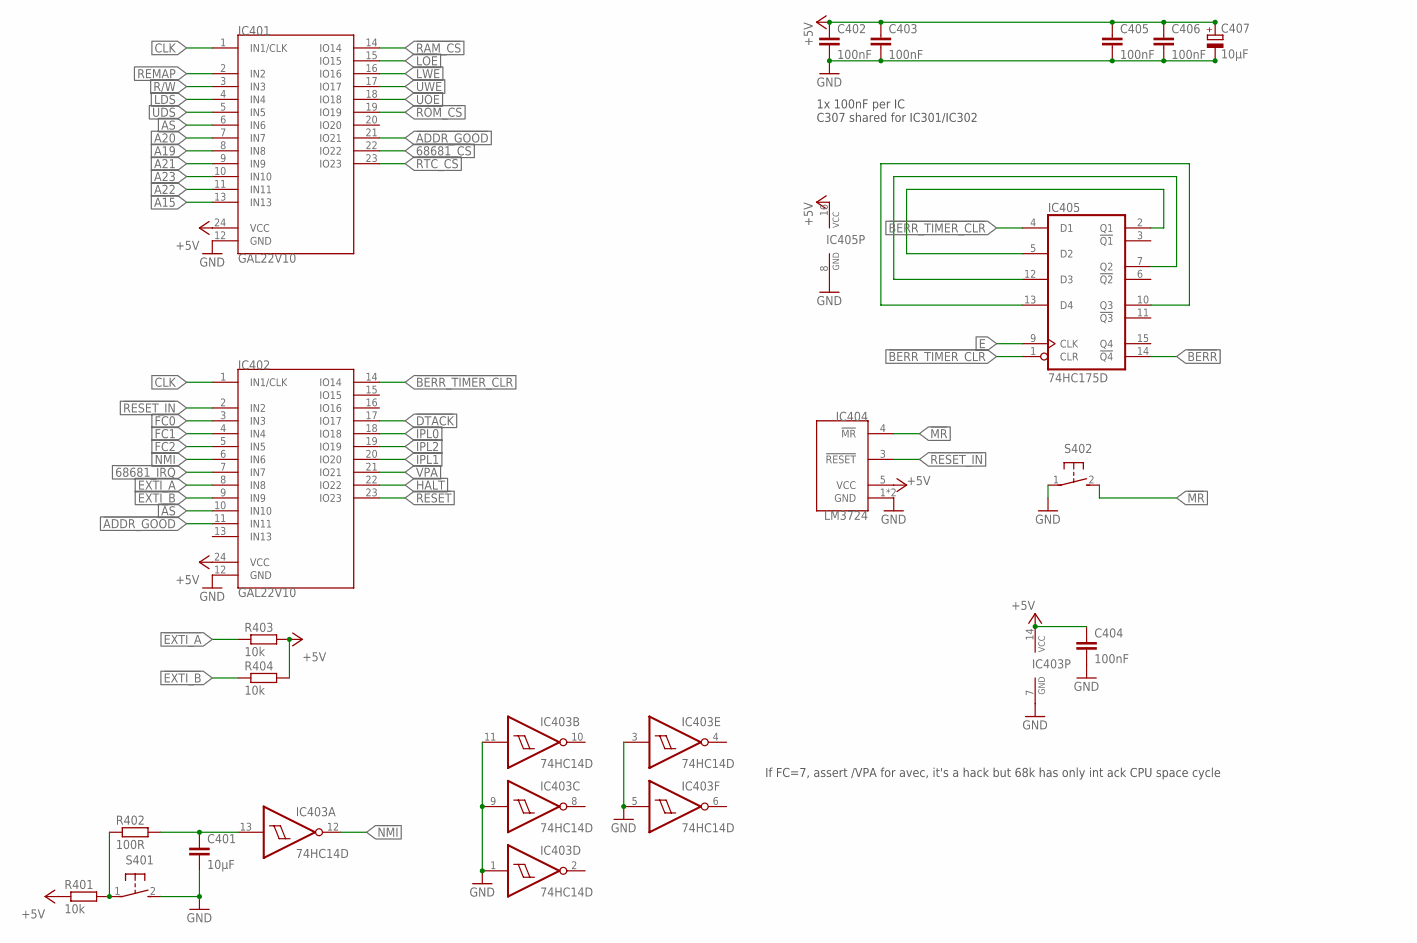
[picture p40: schematic cpu-68000.sch, sheet 4, Supporting Logic]

Parts:
C401: 10µF; C0805; MOUSER 791-0805F106Z100CT
C402, C403, C404, C405, C406: 100nF; C0805; MOUSER 710-885012207072
C407: 10µF; SMC_B; MOUSER 581-TAJB106K020RNJV
IC401, IC402: GAL22V10; DIL24S; MOUSER_SOCKET 575-1104732441001000
IC403: 74HC14D; SO14; MOUSER 771-74HC14D-T
IC404: LM3724; SOT23-5
IC405: 74HC175D; SO16; MOUSER 595-CD74HCT175M
R401, R403, R404: 10k; R2012; MOUSER 652-CR0805FX-1002ELF
R402: 100R; R2012; MOUSER 652-CR0805JW-101ELF
S401, S402: 31-XX; B3F-31XX; MOUSER 653-B3F-3150

Connections:
!68681_CS: IC401.22 (IO22); also elsewhere on the board
!68681_IRQ: IC402.7 (IN7); also elsewhere on the board
!ADDR_GOOD: IC401.21 (IO21), IC402.11 (IN11)
!AS: IC401.6 (IN6), IC402.10 (IN10); also elsewhere on the board
!BERR: IC405.14 (!Q4); also elsewhere on the board
!BERR_TIMER_CLR: IC402.14 (IO14), IC405.1 (CLR), IC405.4 (D1)
!DTACK: IC402.17 (IO17); also elsewhere on the board
!EXTI_A: IC402.8 (IN8), R403.1; also elsewhere on the board
!EXTI_B: IC402.9 (IN9), R404.1; also elsewhere on the board
!HALT: IC402.22 (IO22); also elsewhere on the board
!IPL0: IC402.18 (IO18); also elsewhere on the board
!IPL1: IC402.20 (IO20); also elsewhere on the board
!IPL2: IC402.19 (IO19); also elsewhere on the board
!LDS: IC401.4 (IN4); also elsewhere on the board
!LOE: IC401.15 (IO15); also elsewhere on the board
!LWE: IC401.16 (IO16); also elsewhere on the board
!MR: IC404.4 (!MR), S402.2 (S)
!NMI: IC402.6 (IN6), IC403.12 (O)
!RAM_CS: IC401.14 (IO14); also elsewhere on the board
!RESET: IC402.23 (IO23); also elsewhere on the board
!RESET_IN: IC402.2 (IN2), IC404.3 (!RESET)
!ROM_CS: IC401.19 (IO19); also elsewhere on the board
!RTC_CS: IC401.23 (IO23); also elsewhere on the board
!UDS: IC401.5 (IN5); also elsewhere on the board
!UOE: IC401.18 (IO18); also elsewhere on the board
!UWE: IC401.17 (IO17); also elsewhere on the board
!VPA: IC402.21 (IO21); also elsewhere on the board
+5V: C402.1, C403.1, C404.1, C405.1, C406.1, C407.+, IC401.24 (VCC), IC402.24 (VCC), IC403.14 (VCC), IC404.5 (VCC), IC405.16 (VCC), R401.1, R403.2, R404.2; also elsewhere on the board
A15: IC401.13 (IN13); also elsewhere on the board
A19: IC401.8 (IN8); also elsewhere on the board
A20: IC401.7 (IN7); also elsewhere on the board
A21: IC401.9 (IN9); also elsewhere on the board
A22: IC401.11 (IN11); also elsewhere on the board
A23: IC401.10 (IN10); also elsewhere on the board
CLK: IC401.1 (IN1/CLK), IC402.1 (IN1/CLK); also elsewhere on the board
E: IC405.9 (CLK); also elsewhere on the board
FC0: IC402.3 (IN3); also elsewhere on the board
FC1: IC402.4 (IN4); also elsewhere on the board
FC2: IC402.5 (IN5); also elsewhere on the board
GND: C401.2, C402.2, C403.2, C404.2, C405.2, C406.2, C407.-, IC401.12 (GND), IC402.12 (GND), IC403.1 (I), IC403.3 (I), IC403.5 (I), IC403.7 (GND), IC403.9 (I), IC403.11 (I), IC404.1 (GND), IC404.2 (GND), IC405.8 (GND), S401.2 (S), S402.1; also elsewhere on the board
unnamed: IC405.2 (Q1), IC405.5 (D2)
unnamed: IC405.7 (Q2), IC405.12 (D3)
unnamed: IC405.10 (Q3), IC405.13 (D4)
unnamed: R401.2, R402.1, S401.1
unnamed: C401.1, IC403.13 (I), R402.2
R/!W!: IC401.3 (IN3); also elsewhere on the board
REMAP: IC401.2 (IN2); also elsewhere on the board

Notes on the sheet:
1x 100nF per IC C307 shared for IC301/IC302
If FC=7, assert /VPA for avec, it's a hack but 68k has only int ack CPU space cycle

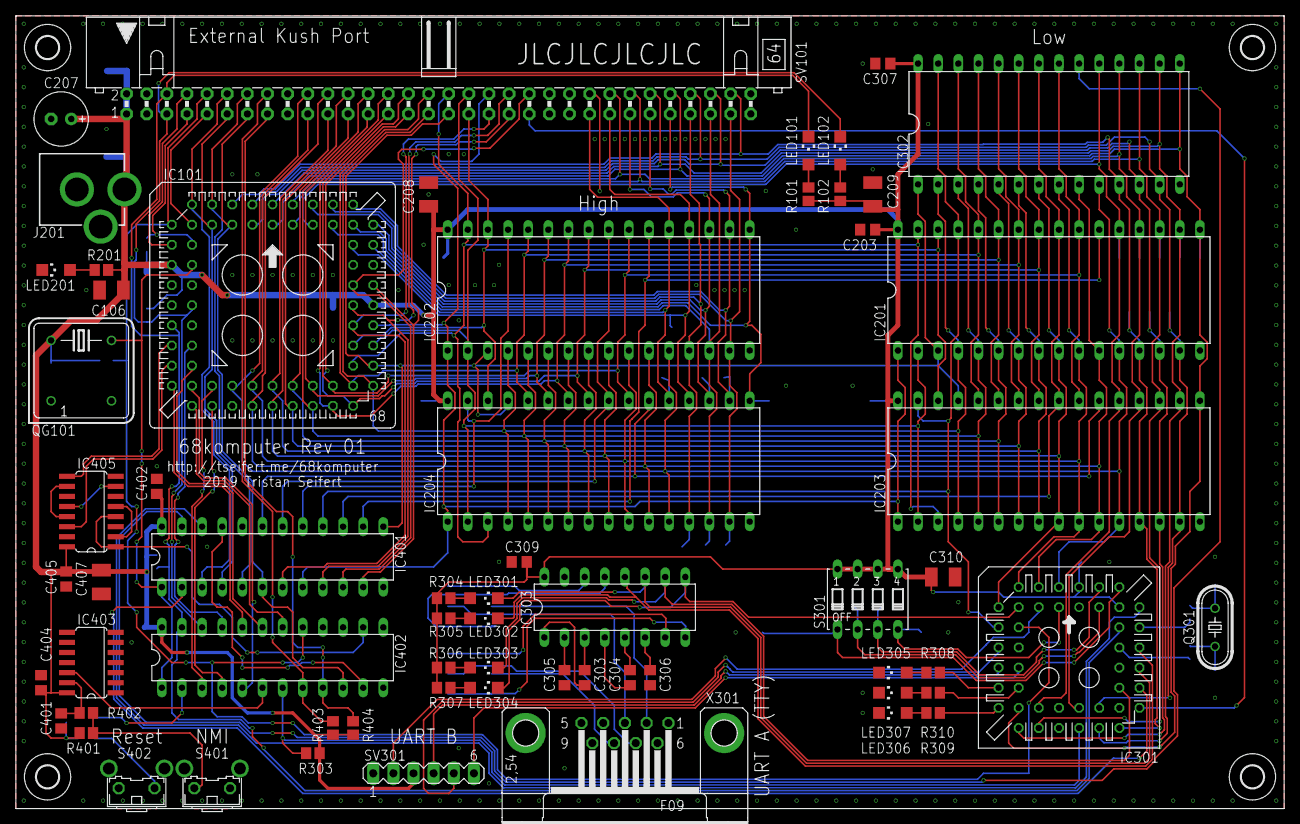
[picture p41: board cpu-68000.brd from above]

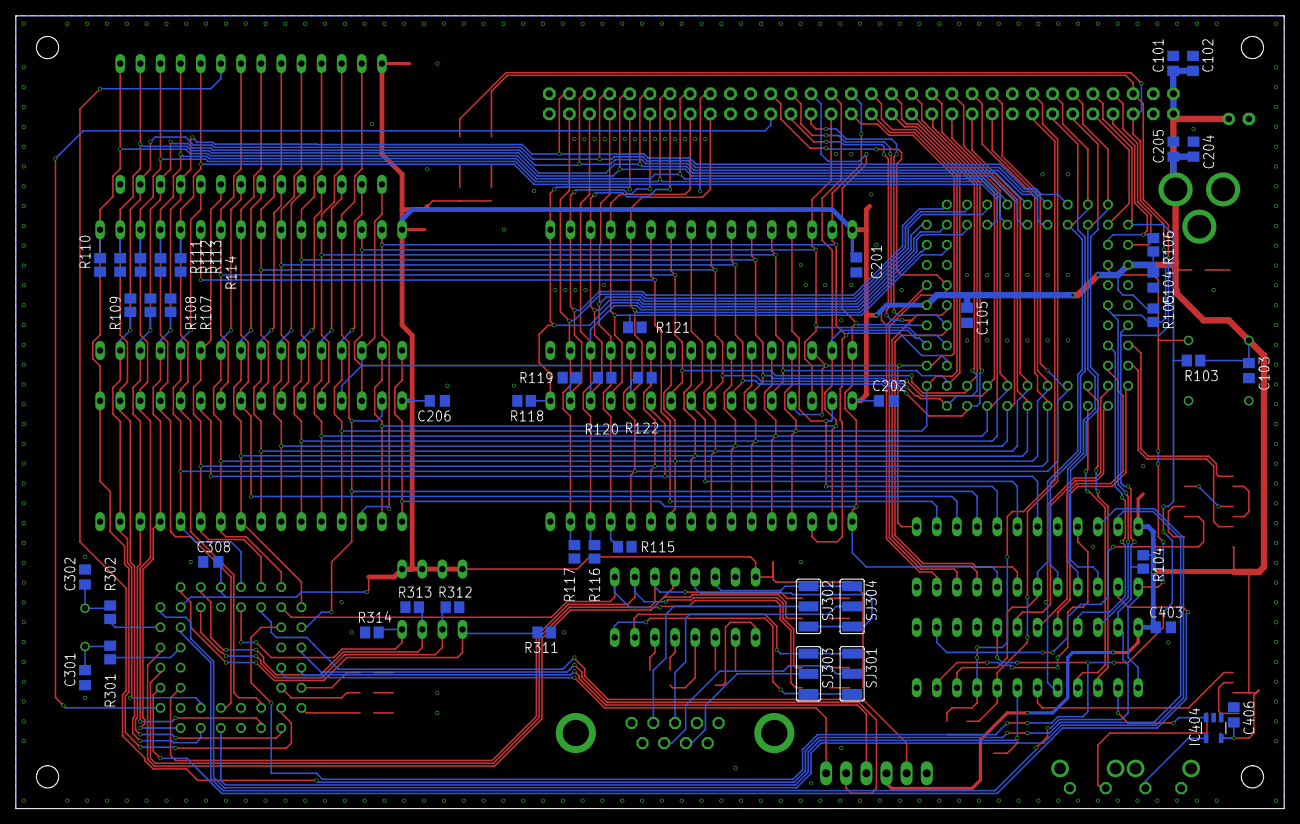
[picture p42: board cpu-68000.brd from below]

Board: 2 copper layers, 160.0 x 100.0 mm, 113 parts (46 on the bottom side), 127 nets.
