tristanseifert/68komputer-hw/cpu-68000/ram-2mb.brd

## EAGLE design cpu-68000/ram-2mb.brd (2019-11-22)

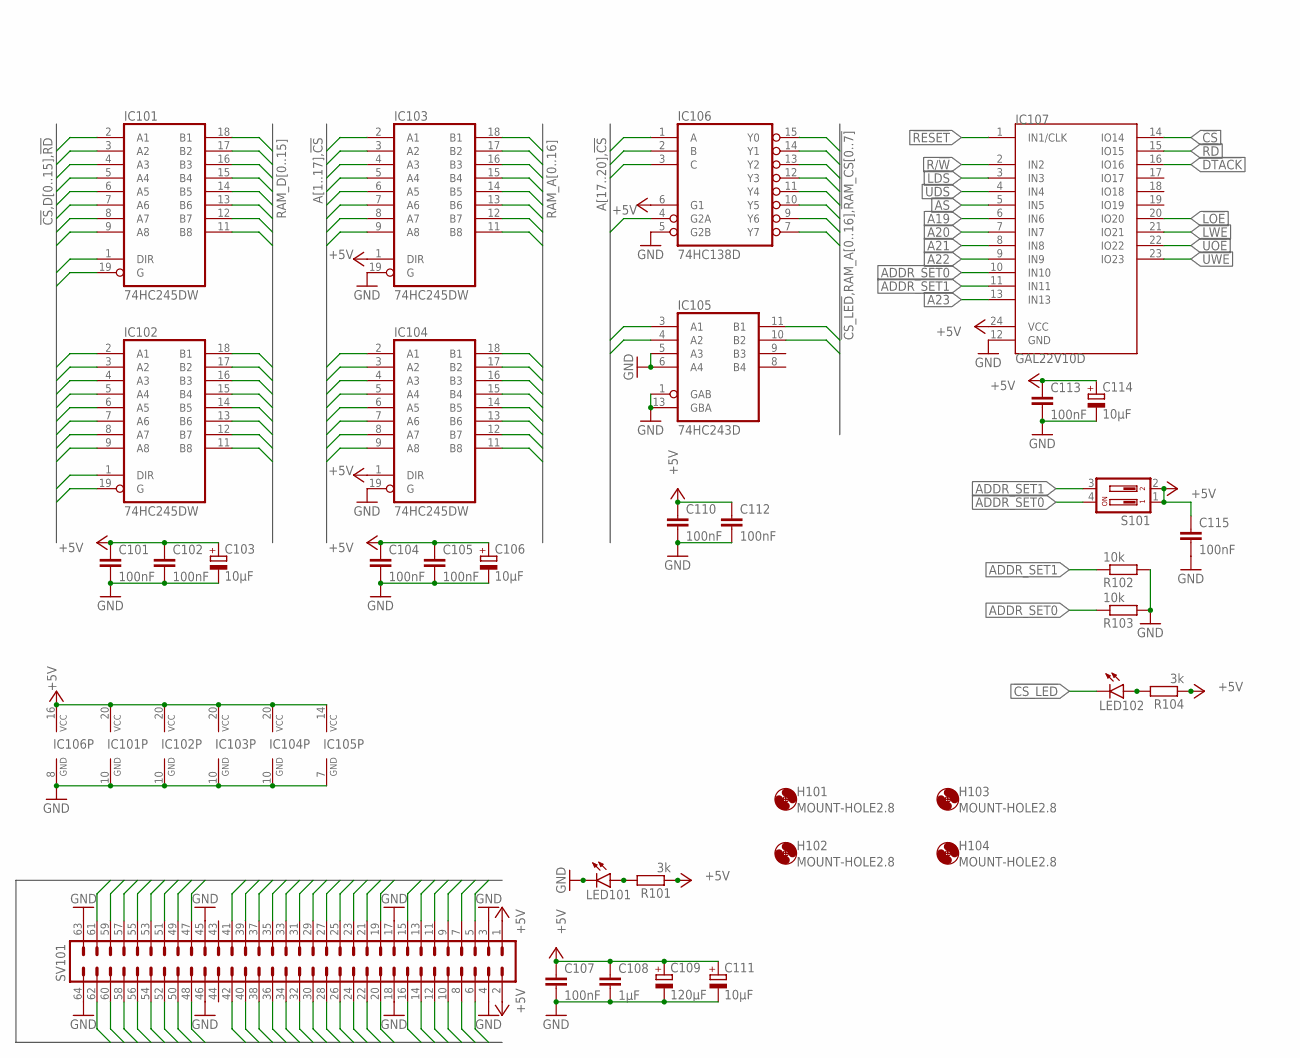
[picture p43: schematic ram-2mb.sch, sheet 1, Interface, Address Decoding]

Parts:
C101, C102, C104, C105, C107, C110, C112, C113, C115: 100nF; C0805; MOUSER 710-885012207072
C103, C106, C111, C114: 10µF; SMC_B; MOUSER 581-TAJB106K020RNJV
C108: 1µF; C0805; MOUSER 710-885012207078
C109: 120µF; E2,5-7; MOUSER 710-860020373007
H101, H102, H103, H104: MOUNT-HOLE2.8; 2,8
IC101, IC102, IC103, IC104: 74HC245DW; SO20W; MOUSER 595-SN74HC245DWR
IC105: 74HC243D; SO14; MOUSER 595-CD74HC243M96
IC106: 74HC138D; SO16; MOUSER 595-SN74HC138DG4
IC107: GAL22V10D; DIL24S; MOUSER_SOCKET 575-1104732441001000
LED101: LEDCHIPLED_1206; CHIPLED_1206; MOUSER 710-156120YS75300
LED102: LEDCHIPLED_1206; CHIPLED_1206; MOUSER 710-156120VS75300
R101, R104: 3k; R2012; MOUSER 652-CR0805JW-302ELF
R102, R103: 10k; R2012; MOUSER 652-CR0805FX-1002ELF
S101: DP02; DP-02
SV101: ML64L

Connections:
!AS: IC107.5 (IN5), SV101.13
!BG: SV101.9
!BGACK: SV101.8
!BR: SV101.7
!CS: IC101.19 (G), IC102.19 (G), IC105.4 (A2), IC106.4 (G2A), IC107.14 (IO14)
!CS_LED: IC105.10 (B2), LED102.C
!DTACK: IC107.16 (IO16), SV101.10
!EXTI_A: SV101.16
!EXTI_B: SV101.15
!EXT_ID: SV101.41
!HALT: SV101.5
!LDS: IC107.3 (IN3), SV101.11
!LOE: IC107.20 (IO20); also elsewhere on the board
!LWE: IC107.21 (IO21); also elsewhere on the board
!RAM_CS0: IC106.15 (Y0); also elsewhere on the board
!RAM_CS1: IC106.14 (Y1); also elsewhere on the board
!RAM_CS2: IC106.13 (Y2); also elsewhere on the board
!RAM_CS3: IC106.12 (Y3); also elsewhere on the board
!RAM_CS4: IC106.11 (Y4); also elsewhere on the board
!RAM_CS5: IC106.10 (Y5); also elsewhere on the board
!RAM_CS6: IC106.9 (Y6); also elsewhere on the board
!RAM_CS7: IC106.7 (Y7); also elsewhere on the board
!RD: IC101.1 (DIR), IC102.1 (DIR), IC107.15 (IO15)
!RESET: IC107.1 (IN1/CLK), SV101.6
!UDS: IC107.4 (IN4), SV101.14
!UOE: IC107.22 (IO22); also elsewhere on the board
!UWE: IC107.23 (IO23); also elsewhere on the board
+5V: C101.1, C102.1, C103.+, C104.1, C105.1, C106.+, C107.1, C108.1, C109.+, C110.1, C111.+, C112.1, C113.1, C114.+, C115.1, IC101.20 (VCC), IC102.20 (VCC), IC103.1 (DIR), IC103.20 (VCC), IC104.1 (DIR), IC104.20 (VCC), IC105.14 (VCC), IC106.6 (G1), IC106.16 (VCC), IC107.24 (VCC), R101.1, R104.1, S101.1, S101.2, SV101.1, SV101.2; also elsewhere on the board
A1: IC103.2 (A1), SV101.20
A2: IC103.3 (A2), SV101.22
A3: IC103.4 (A3), SV101.19
A4: IC103.5 (A4), SV101.24
A5: IC103.6 (A5), SV101.21
A6: IC103.7 (A6), SV101.23
A7: IC103.8 (A7), SV101.26
A8: IC103.9 (A8), SV101.25
A9: IC104.2 (A1), SV101.28
A10: IC104.3 (A2), SV101.27
A11: IC104.4 (A3), SV101.30
A12: IC104.5 (A4), SV101.29
A13: IC104.6 (A5), SV101.31
A14: IC104.7 (A6), SV101.32
A15: IC104.8 (A7), SV101.33
A16: IC104.9 (A8), SV101.34
A17: IC105.3 (A1), SV101.36
A18: IC106.1 (A), SV101.35
A19: IC106.2 (B), IC107.6 (IN6), SV101.38
A20: IC106.3 (C), IC107.7 (IN7), SV101.37
A21: IC107.8 (IN8), SV101.40
A22: IC107.9 (IN9), SV101.39
A23: IC107.13 (IN13), SV101.42
ADDR_SET0: IC107.10 (IN10), R103.1, S101.4
ADDR_SET1: IC107.11 (IN11), R102.1, S101.3
D0: IC101.2 (A1), SV101.62
D1: IC101.3 (A2), SV101.60
D2: IC101.4 (A3), SV101.58
D3: IC101.5 (A4), SV101.56
D4: IC101.6 (A5), SV101.54
D5: IC101.7 (A6), SV101.52
D6: IC101.8 (A7), SV101.50
D7: IC101.9 (A8), SV101.48
D8: IC102.2 (A1), SV101.57
D9: IC102.3 (A2), SV101.59
D10: IC102.4 (A3), SV101.61
D11: IC102.5 (A4), SV101.55
D12: IC102.6 (A5), SV101.53
D13: IC102.7 (A6), SV101.51
D14: IC102.8 (A7), SV101.49
D15: IC102.9 (A8), SV101.47
GND: C101.2, C102.2, C103.-, C104.2, C105.2, C106.-, C107.2, C108.2, C109.-, C110.2, C111.-, C112.2, C113.2, C114.-, C115.2, IC101.10 (GND), IC102.10 (GND), IC103.10 (GND), IC103.19 (G), IC104.10 (GND), IC104.19 (G), IC105.1 (GAB), IC105.5 (A3), IC105.6 (A4), IC105.7 (GND), IC105.13 (GBA), IC106.5 (G2B), IC106.8 (GND), IC107.12 (GND), LED101.C, R102.2, R103.2, SV101.3, SV101.4, SV101.17, SV101.18, SV101.45, SV101.46, SV101.63, SV101.64; also elsewhere on the board
unnamed: LED102.A, R104.2
unnamed: LED101.A, R101.2
R/!W!: IC107.2 (IN2), SV101.12
RAM_A0: IC103.18 (B1); also elsewhere on the board
RAM_A1: IC103.17 (B2); also elsewhere on the board
RAM_A2: IC103.16 (B3); also elsewhere on the board
RAM_A3: IC103.15 (B4); also elsewhere on the board
RAM_A4: IC103.14 (B5); also elsewhere on the board
RAM_A5: IC103.13 (B6); also elsewhere on the board
RAM_A6: IC103.12 (B7); also elsewhere on the board
RAM_A7: IC103.11 (B8); also elsewhere on the board
RAM_A8: IC104.18 (B1); also elsewhere on the board
RAM_A9: IC104.17 (B2); also elsewhere on the board
RAM_A10: IC104.16 (B3); also elsewhere on the board
RAM_A11: IC104.15 (B4); also elsewhere on the board
RAM_A12: IC104.14 (B5); also elsewhere on the board
RAM_A13: IC104.13 (B6); also elsewhere on the board
RAM_A14: IC104.12 (B7); also elsewhere on the board
RAM_A15: IC104.11 (B8); also elsewhere on the board
RAM_A16: IC105.11 (B1); also elsewhere on the board
RAM_D0: IC101.18 (B1); also elsewhere on the board
RAM_D1: IC101.17 (B2); also elsewhere on the board
RAM_D2: IC101.16 (B3); also elsewhere on the board
RAM_D3: IC101.15 (B4); also elsewhere on the board
RAM_D4: IC101.14 (B5); also elsewhere on the board
RAM_D5: IC101.13 (B6); also elsewhere on the board
RAM_D6: IC101.12 (B7); also elsewhere on the board
RAM_D7: IC101.11 (B8); also elsewhere on the board
RAM_D8: IC102.18 (B1); also elsewhere on the board
RAM_D9: IC102.17 (B2); also elsewhere on the board
RAM_D10: IC102.16 (B3); also elsewhere on the board
RAM_D11: IC102.15 (B4); also elsewhere on the board
RAM_D12: IC102.14 (B5); also elsewhere on the board
RAM_D13: IC102.13 (B6); also elsewhere on the board
RAM_D14: IC102.12 (B7); also elsewhere on the board
RAM_D15: IC102.11 (B8); also elsewhere on the board

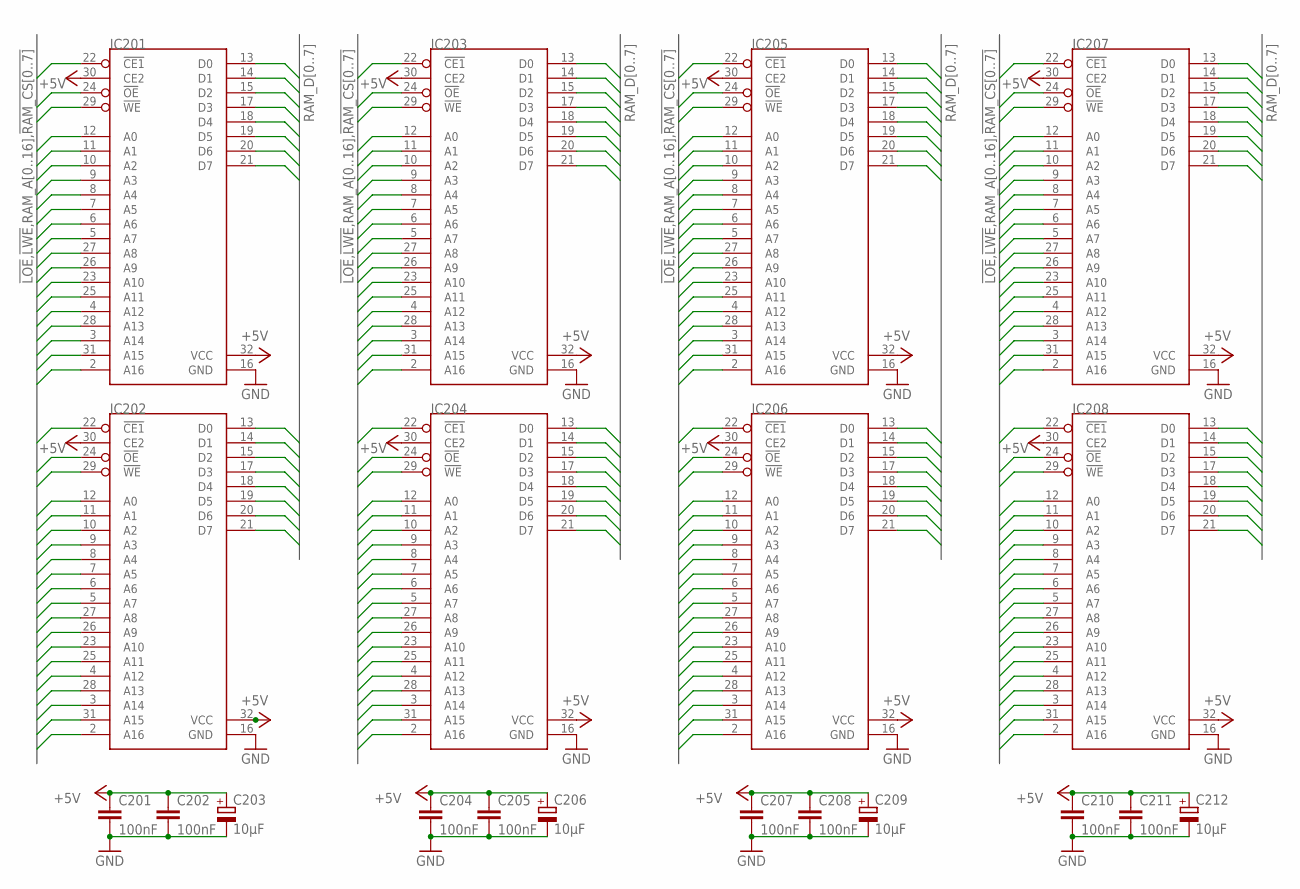
[picture p44: schematic ram-2mb.sch, sheet 2, RAM (Low Byte)]

Parts:
C201, C202, C204, C205, C207, C208, C210, C211: 100nF; C0805; MOUSER 710-885012207072
C203, C206, C209, C212: 10µF; SMC_B; MOUSER 581-TAJB106K020RNJV
IC201, IC202, IC203, IC204, IC205, IC206, IC207, IC208: CY62128BSOIC32-450; SOIC127P1412X299-32N

Connections:
!LOE: IC201.24 (!OE), IC202.24 (!OE), IC203.24 (!OE), IC204.24 (!OE), IC205.24 (!OE), IC206.24 (!OE), IC207.24 (!OE), IC208.24 (!OE); also elsewhere on the board
!LWE: IC201.29 (!WE), IC202.29 (!WE), IC203.29 (!WE), IC204.29 (!WE), IC205.29 (!WE), IC206.29 (!WE), IC207.29 (!WE), IC208.29 (!WE); also elsewhere on the board
!RAM_CS0: IC201.22 (!CE1); also elsewhere on the board
!RAM_CS1: IC202.22 (!CE1); also elsewhere on the board
!RAM_CS2: IC203.22 (!CE1); also elsewhere on the board
!RAM_CS3: IC204.22 (!CE1); also elsewhere on the board
!RAM_CS4: IC205.22 (!CE1); also elsewhere on the board
!RAM_CS5: IC206.22 (!CE1); also elsewhere on the board
!RAM_CS6: IC207.22 (!CE1); also elsewhere on the board
!RAM_CS7: IC208.22 (!CE1); also elsewhere on the board
+5V: C201.1, C202.1, C203.+, C204.1, C205.1, C206.+, C207.1, C208.1, C209.+, C210.1, C211.1, C212.+, IC201.30 (CE2), IC201.32 (VCC), IC202.30 (CE2), IC202.32 (VCC), IC203.30 (CE2), IC203.32 (VCC), IC204.30 (CE2), IC204.32 (VCC), IC205.30 (CE2), IC205.32 (VCC), IC206.30 (CE2), IC206.32 (VCC), IC207.30 (CE2), IC207.32 (VCC), IC208.30 (CE2), IC208.32 (VCC); also elsewhere on the board
GND: C201.2, C202.2, C203.-, C204.2, C205.2, C206.-, C207.2, C208.2, C209.-, C210.2, C211.2, C212.-, IC201.16 (GND), IC202.16 (GND), IC203.16 (GND), IC204.16 (GND), IC205.16 (GND), IC206.16 (GND), IC207.16 (GND), IC208.16 (GND); also elsewhere on the board
RAM_A0: IC201.12 (A0), IC202.12 (A0), IC203.12 (A0), IC204.12 (A0), IC205.12 (A0), IC206.12 (A0), IC207.12 (A0), IC208.12 (A0); also elsewhere on the board
RAM_A1: IC201.11 (A1), IC202.11 (A1), IC203.11 (A1), IC204.11 (A1), IC205.11 (A1), IC206.11 (A1), IC207.11 (A1), IC208.11 (A1); also elsewhere on the board
RAM_A2: IC201.10 (A2), IC202.10 (A2), IC203.10 (A2), IC204.10 (A2), IC205.10 (A2), IC206.10 (A2), IC207.10 (A2), IC208.10 (A2); also elsewhere on the board
RAM_A3: IC201.9 (A3), IC202.9 (A3), IC203.9 (A3), IC204.9 (A3), IC205.9 (A3), IC206.9 (A3), IC207.9 (A3), IC208.9 (A3); also elsewhere on the board
RAM_A4: IC201.8 (A4), IC202.8 (A4), IC203.8 (A4), IC204.8 (A4), IC205.8 (A4), IC206.8 (A4), IC207.8 (A4), IC208.8 (A4); also elsewhere on the board
RAM_A5: IC201.7 (A5), IC202.7 (A5), IC203.7 (A5), IC204.7 (A5), IC205.7 (A5), IC206.7 (A5), IC207.7 (A5), IC208.7 (A5); also elsewhere on the board
RAM_A6: IC201.6 (A6), IC202.6 (A6), IC203.6 (A6), IC204.6 (A6), IC205.6 (A6), IC206.6 (A6), IC207.6 (A6), IC208.6 (A6); also elsewhere on the board
RAM_A7: IC201.5 (A7), IC202.5 (A7), IC203.5 (A7), IC204.5 (A7), IC205.5 (A7), IC206.5 (A7), IC207.5 (A7), IC208.5 (A7); also elsewhere on the board
RAM_A8: IC201.27 (A8), IC202.27 (A8), IC203.27 (A8), IC204.27 (A8), IC205.27 (A8), IC206.27 (A8), IC207.27 (A8), IC208.27 (A8); also elsewhere on the board
RAM_A9: IC201.26 (A9), IC202.26 (A9), IC203.26 (A9), IC204.26 (A9), IC205.26 (A9), IC206.26 (A9), IC207.26 (A9), IC208.26 (A9); also elsewhere on the board
RAM_A10: IC201.23 (A10), IC202.23 (A10), IC203.23 (A10), IC204.23 (A10), IC205.23 (A10), IC206.23 (A10), IC207.23 (A10), IC208.23 (A10); also elsewhere on the board
RAM_A11: IC201.25 (A11), IC202.25 (A11), IC203.25 (A11), IC204.25 (A11), IC205.25 (A11), IC206.25 (A11), IC207.25 (A11), IC208.25 (A11); also elsewhere on the board
RAM_A12: IC201.4 (A12), IC202.4 (A12), IC203.4 (A12), IC204.4 (A12), IC205.4 (A12), IC206.4 (A12), IC207.4 (A12), IC208.4 (A12); also elsewhere on the board
RAM_A13: IC201.28 (A13), IC202.28 (A13), IC203.28 (A13), IC204.28 (A13), IC205.28 (A13), IC206.28 (A13), IC207.28 (A13), IC208.28 (A13); also elsewhere on the board
RAM_A14: IC201.3 (A14), IC202.3 (A14), IC203.3 (A14), IC204.3 (A14), IC205.3 (A14), IC206.3 (A14), IC207.3 (A14), IC208.3 (A14); also elsewhere on the board
RAM_A15: IC201.31 (A15), IC202.31 (A15), IC203.31 (A15), IC204.31 (A15), IC205.31 (A15), IC206.31 (A15), IC207.31 (A15), IC208.31 (A15); also elsewhere on the board
RAM_A16: IC201.2 (A16), IC202.2 (A16), IC203.2 (A16), IC204.2 (A16), IC205.2 (A16), IC206.2 (A16), IC207.2 (A16), IC208.2 (A16); also elsewhere on the board
RAM_D0: IC201.13 (D0), IC202.13 (D0), IC203.13 (D0), IC204.13 (D0), IC205.13 (D0), IC206.13 (D0), IC207.13 (D0), IC208.13 (D0); also elsewhere on the board
RAM_D1: IC201.14 (D1), IC202.14 (D1), IC203.14 (D1), IC204.14 (D1), IC205.14 (D1), IC206.14 (D1), IC207.14 (D1), IC208.14 (D1); also elsewhere on the board
RAM_D2: IC201.15 (D2), IC202.15 (D2), IC203.15 (D2), IC204.15 (D2), IC205.15 (D2), IC206.15 (D2), IC207.15 (D2), IC208.15 (D2); also elsewhere on the board
RAM_D3: IC201.17 (D3), IC202.17 (D3), IC203.17 (D3), IC204.17 (D3), IC205.17 (D3), IC206.17 (D3), IC207.17 (D3), IC208.17 (D3); also elsewhere on the board
RAM_D4: IC201.18 (D4), IC202.18 (D4), IC203.18 (D4), IC204.18 (D4), IC205.18 (D4), IC206.18 (D4), IC207.18 (D4), IC208.18 (D4); also elsewhere on the board
RAM_D5: IC201.19 (D5), IC202.19 (D5), IC203.19 (D5), IC204.19 (D5), IC205.19 (D5), IC206.19 (D5), IC207.19 (D5), IC208.19 (D5); also elsewhere on the board
RAM_D6: IC201.20 (D6), IC202.20 (D6), IC203.20 (D6), IC204.20 (D6), IC205.20 (D6), IC206.20 (D6), IC207.20 (D6), IC208.20 (D6); also elsewhere on the board
RAM_D7: IC201.21 (D7), IC202.21 (D7), IC203.21 (D7), IC204.21 (D7), IC205.21 (D7), IC206.21 (D7), IC207.21 (D7), IC208.21 (D7); also elsewhere on the board
