tristanseifert/68komputer-hw/cpu-68000/ram-2mb.brd

## EAGLE design cpu-68000/ram-2mb.brd (continued)

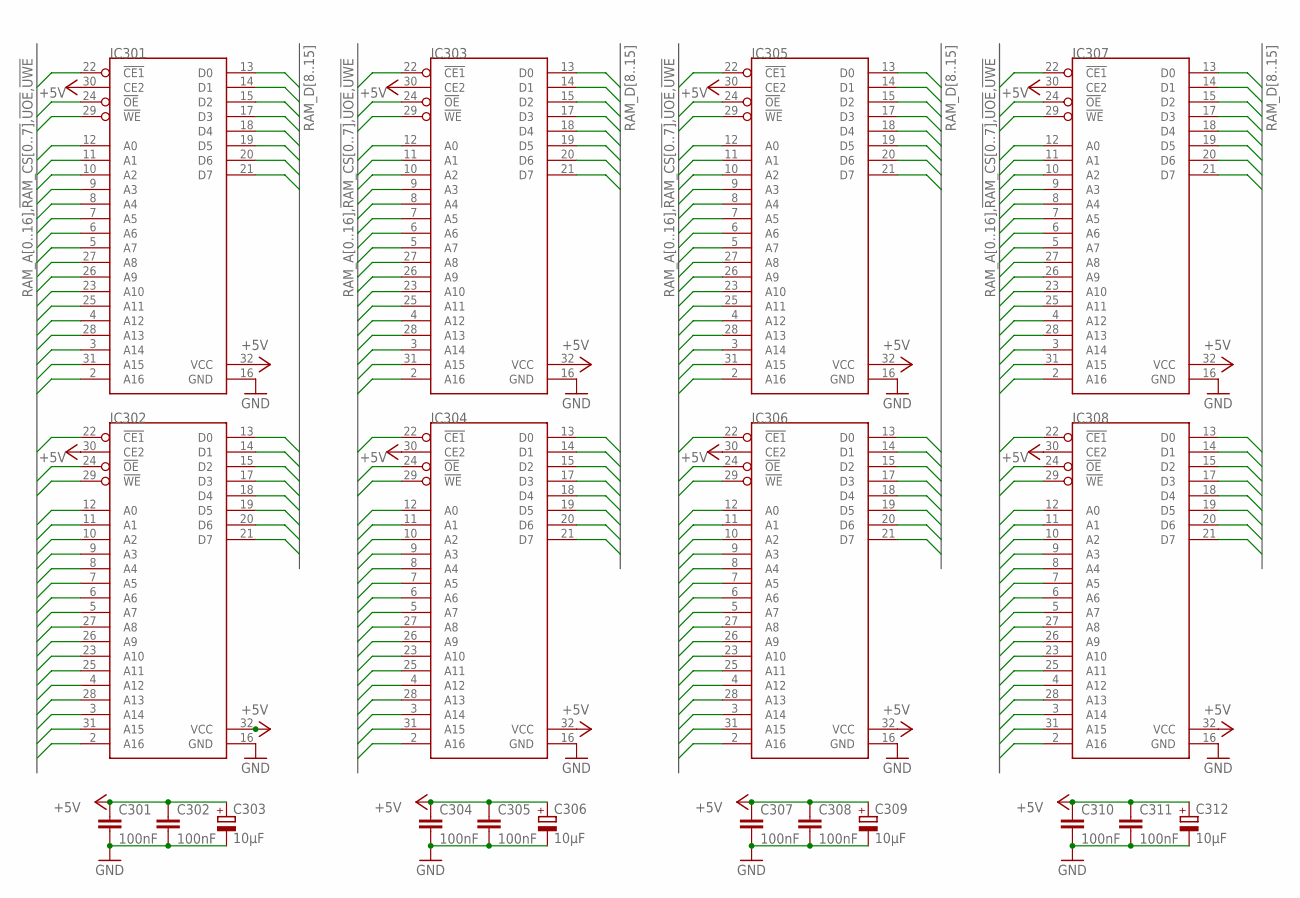
[picture p45: schematic ram-2mb.sch, sheet 3, RAM (High Byte)]

Parts:
C301, C302, C304, C305, C307, C308, C310, C311: 100nF; C0805; MOUSER 710-885012207072
C303, C306, C309, C312: 10µF; SMC_B; MOUSER 581-TAJB106K020RNJV
IC301, IC302, IC303, IC304, IC305, IC306, IC307, IC308: CY62128BSOIC32-450; SOIC127P1412X299-32N

Connections:
!RAM_CS0: IC301.22 (!CE1); also elsewhere on the board
!RAM_CS1: IC302.22 (!CE1); also elsewhere on the board
!RAM_CS2: IC303.22 (!CE1); also elsewhere on the board
!RAM_CS3: IC304.22 (!CE1); also elsewhere on the board
!RAM_CS4: IC305.22 (!CE1); also elsewhere on the board
!RAM_CS5: IC306.22 (!CE1); also elsewhere on the board
!RAM_CS6: IC307.22 (!CE1); also elsewhere on the board
!RAM_CS7: IC308.22 (!CE1); also elsewhere on the board
!UOE: IC301.24 (!OE), IC302.24 (!OE), IC303.24 (!OE), IC304.24 (!OE), IC305.24 (!OE), IC306.24 (!OE), IC307.24 (!OE), IC308.24 (!OE); also elsewhere on the board
!UWE: IC301.29 (!WE), IC302.29 (!WE), IC303.29 (!WE), IC304.29 (!WE), IC305.29 (!WE), IC306.29 (!WE), IC307.29 (!WE), IC308.29 (!WE); also elsewhere on the board
+5V: C301.1, C302.1, C303.+, C304.1, C305.1, C306.+, C307.1, C308.1, C309.+, C310.1, C311.1, C312.+, IC301.30 (CE2), IC301.32 (VCC), IC302.30 (CE2), IC302.32 (VCC), IC303.30 (CE2), IC303.32 (VCC), IC304.30 (CE2), IC304.32 (VCC), IC305.30 (CE2), IC305.32 (VCC), IC306.30 (CE2), IC306.32 (VCC), IC307.30 (CE2), IC307.32 (VCC), IC308.30 (CE2), IC308.32 (VCC); also elsewhere on the board
GND: C301.2, C302.2, C303.-, C304.2, C305.2, C306.-, C307.2, C308.2, C309.-, C310.2, C311.2, C312.-, IC301.16 (GND), IC302.16 (GND), IC303.16 (GND), IC304.16 (GND), IC305.16 (GND), IC306.16 (GND), IC307.16 (GND), IC308.16 (GND); also elsewhere on the board
RAM_A0: IC301.12 (A0), IC302.12 (A0), IC303.12 (A0), IC304.12 (A0), IC305.12 (A0), IC306.12 (A0), IC307.12 (A0), IC308.12 (A0); also elsewhere on the board
RAM_A1: IC301.11 (A1), IC302.11 (A1), IC303.11 (A1), IC304.11 (A1), IC305.11 (A1), IC306.11 (A1), IC307.11 (A1), IC308.11 (A1); also elsewhere on the board
RAM_A2: IC301.10 (A2), IC302.10 (A2), IC303.10 (A2), IC304.10 (A2), IC305.10 (A2), IC306.10 (A2), IC307.10 (A2), IC308.10 (A2); also elsewhere on the board
RAM_A3: IC301.9 (A3), IC302.9 (A3), IC303.9 (A3), IC304.9 (A3), IC305.9 (A3), IC306.9 (A3), IC307.9 (A3), IC308.9 (A3); also elsewhere on the board
RAM_A4: IC301.8 (A4), IC302.8 (A4), IC303.8 (A4), IC304.8 (A4), IC305.8 (A4), IC306.8 (A4), IC307.8 (A4), IC308.8 (A4); also elsewhere on the board
RAM_A5: IC301.7 (A5), IC302.7 (A5), IC303.7 (A5), IC304.7 (A5), IC305.7 (A5), IC306.7 (A5), IC307.7 (A5), IC308.7 (A5); also elsewhere on the board
RAM_A6: IC301.6 (A6), IC302.6 (A6), IC303.6 (A6), IC304.6 (A6), IC305.6 (A6), IC306.6 (A6), IC307.6 (A6), IC308.6 (A6); also elsewhere on the board
RAM_A7: IC301.5 (A7), IC302.5 (A7), IC303.5 (A7), IC304.5 (A7), IC305.5 (A7), IC306.5 (A7), IC307.5 (A7), IC308.5 (A7); also elsewhere on the board
RAM_A8: IC301.27 (A8), IC302.27 (A8), IC303.27 (A8), IC304.27 (A8), IC305.27 (A8), IC306.27 (A8), IC307.27 (A8), IC308.27 (A8); also elsewhere on the board
RAM_A9: IC301.26 (A9), IC302.26 (A9), IC303.26 (A9), IC304.26 (A9), IC305.26 (A9), IC306.26 (A9), IC307.26 (A9), IC308.26 (A9); also elsewhere on the board
RAM_A10: IC301.23 (A10), IC302.23 (A10), IC303.23 (A10), IC304.23 (A10), IC305.23 (A10), IC306.23 (A10), IC307.23 (A10), IC308.23 (A10); also elsewhere on the board
RAM_A11: IC301.25 (A11), IC302.25 (A11), IC303.25 (A11), IC304.25 (A11), IC305.25 (A11), IC306.25 (A11), IC307.25 (A11), IC308.25 (A11); also elsewhere on the board
RAM_A12: IC301.4 (A12), IC302.4 (A12), IC303.4 (A12), IC304.4 (A12), IC305.4 (A12), IC306.4 (A12), IC307.4 (A12), IC308.4 (A12); also elsewhere on the board
RAM_A13: IC301.28 (A13), IC302.28 (A13), IC303.28 (A13), IC304.28 (A13), IC305.28 (A13), IC306.28 (A13), IC307.28 (A13), IC308.28 (A13); also elsewhere on the board
RAM_A14: IC301.3 (A14), IC302.3 (A14), IC303.3 (A14), IC304.3 (A14), IC305.3 (A14), IC306.3 (A14), IC307.3 (A14), IC308.3 (A14); also elsewhere on the board
RAM_A15: IC301.31 (A15), IC302.31 (A15), IC303.31 (A15), IC304.31 (A15), IC305.31 (A15), IC306.31 (A15), IC307.31 (A15), IC308.31 (A15); also elsewhere on the board
RAM_A16: IC301.2 (A16), IC302.2 (A16), IC303.2 (A16), IC304.2 (A16), IC305.2 (A16), IC306.2 (A16), IC307.2 (A16), IC308.2 (A16); also elsewhere on the board
RAM_D8: IC301.13 (D0), IC302.13 (D0), IC303.13 (D0), IC304.13 (D0), IC305.13 (D0), IC306.13 (D0), IC307.13 (D0), IC308.13 (D0); also elsewhere on the board
RAM_D9: IC301.14 (D1), IC302.14 (D1), IC303.14 (D1), IC304.14 (D1), IC305.14 (D1), IC306.14 (D1), IC307.14 (D1), IC308.14 (D1); also elsewhere on the board
RAM_D10: IC301.15 (D2), IC302.15 (D2), IC303.15 (D2), IC304.15 (D2), IC305.15 (D2), IC306.15 (D2), IC307.15 (D2), IC308.15 (D2); also elsewhere on the board
RAM_D11: IC301.17 (D3), IC302.17 (D3), IC303.17 (D3), IC304.17 (D3), IC305.17 (D3), IC306.17 (D3), IC307.17 (D3), IC308.17 (D3); also elsewhere on the board
RAM_D12: IC301.18 (D4), IC302.18 (D4), IC303.18 (D4), IC304.18 (D4), IC305.18 (D4), IC306.18 (D4), IC307.18 (D4), IC308.18 (D4); also elsewhere on the board
RAM_D13: IC301.19 (D5), IC302.19 (D5), IC303.19 (D5), IC304.19 (D5), IC305.19 (D5), IC306.19 (D5), IC307.19 (D5), IC308.19 (D5); also elsewhere on the board
RAM_D14: IC301.20 (D6), IC302.20 (D6), IC303.20 (D6), IC304.20 (D6), IC305.20 (D6), IC306.20 (D6), IC307.20 (D6), IC308.20 (D6); also elsewhere on the board
RAM_D15: IC301.21 (D7), IC302.21 (D7), IC303.21 (D7), IC304.21 (D7), IC305.21 (D7), IC306.21 (D7), IC307.21 (D7), IC308.21 (D7); also elsewhere on the board

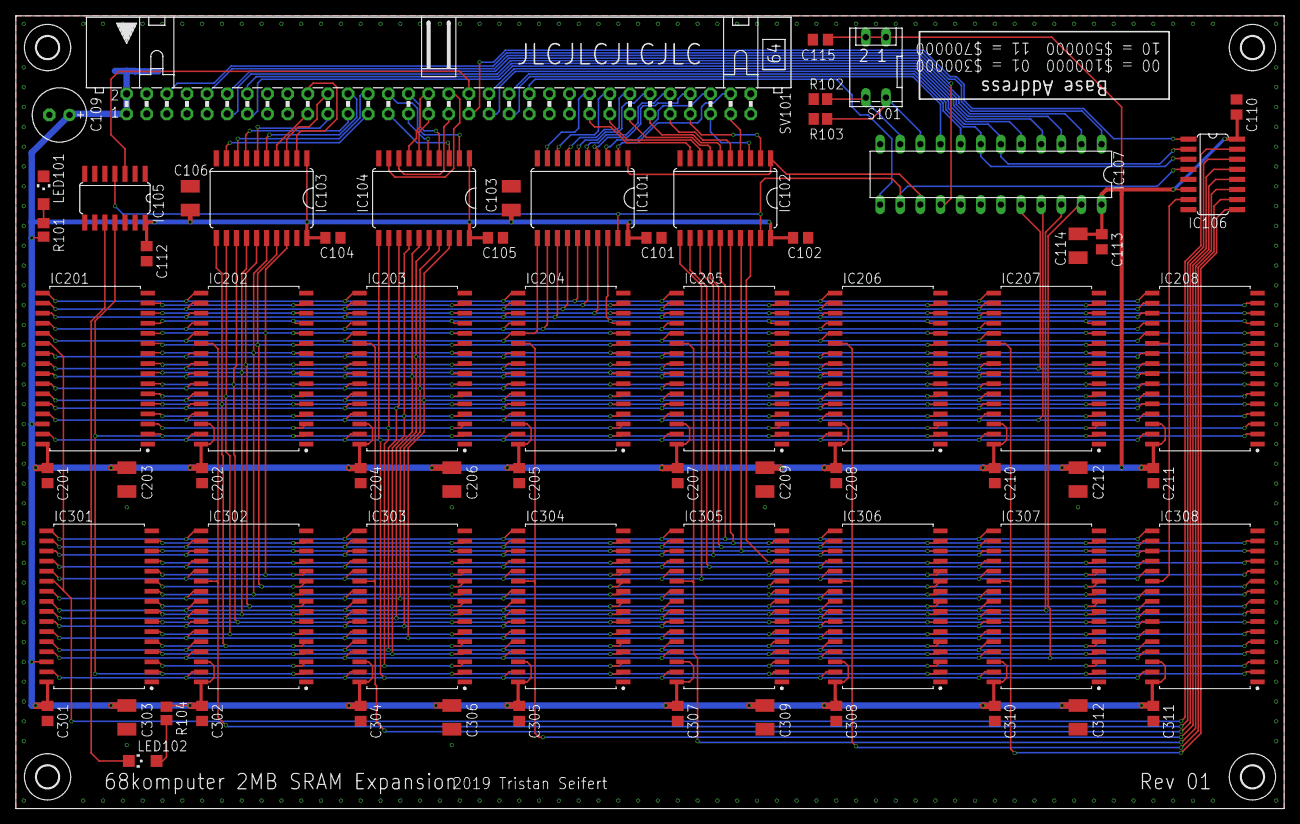
[picture p46: board ram-2mb.brd from above]

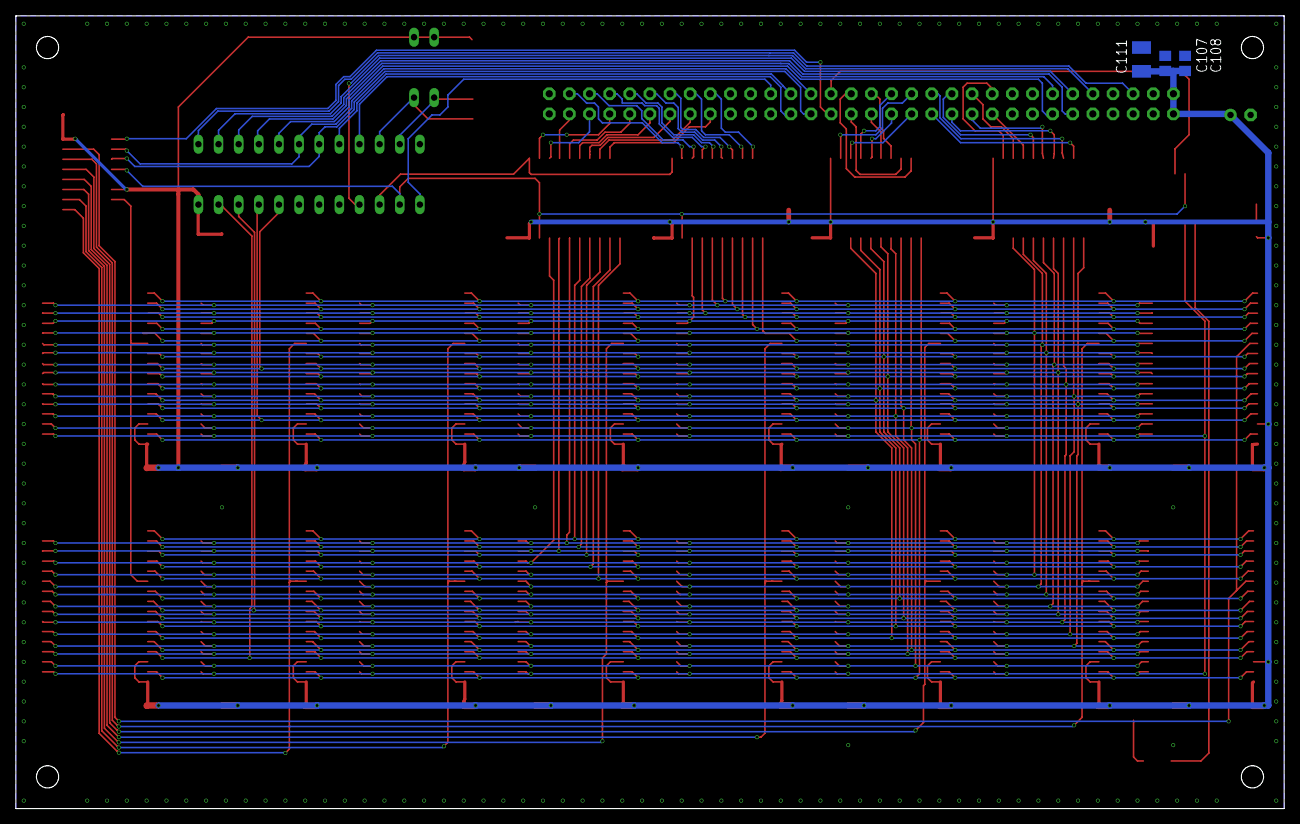
[picture p47: board ram-2mb.brd from below]

Board: 2 copper layers, 160.0 x 100.0 mm, 74 parts (3 on the bottom side), 99 nets.
