tristanseifert/68komputer-hw/cpu-68000/io.brd

## EAGLE design cpu-68000/io.brd (2019-11-21)

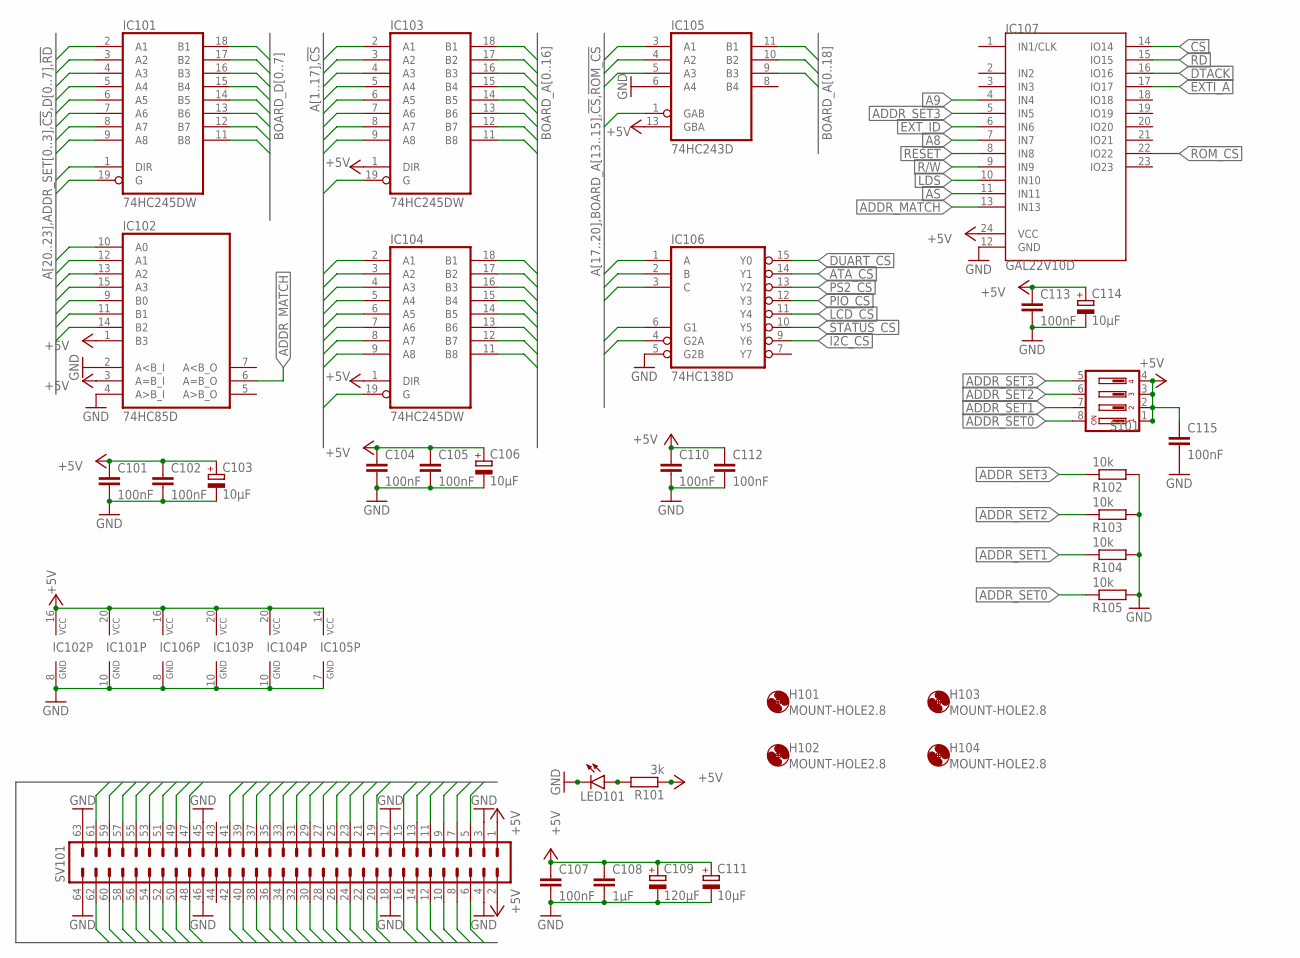
[picture p48: schematic io.sch, sheet 1, Interface, Address Decoding]

Parts:
C101, C102, C104, C105, C107, C110, C112, C113, C115: 100nF; C0805; MOUSER 710-885012207072
C103, C106, C111, C114: 10µF; SMC_B; MOUSER 581-TAJB106K020RNJV
C108: 1µF; C0805; MOUSER 710-885012207078
C109: 120µF; E2,5-7; MOUSER 710-860020373007
H101, H102, H103, H104: MOUNT-HOLE2.8; 2,8
IC101, IC103, IC104: 74HC245DW; SO20W; MOUSER 595-SN74HC245DWR
IC102: 74HC85D; SO16; MOUSER 771-74HC138D
IC105: 74HC243D; SO14; MOUSER 595-CD74HC243M96
IC106: 74HC138D; SO16; MOUSER 595-SN74HC138DG4
IC107: GAL22V10D; DIL24S; MOUSER_SOCKET 575-1104732441001000
LED101: LEDCHIPLED_1206; CHIPLED_1206; MOUSER 710-156120YS75300
R101: 3k; R2012; MOUSER 652-CR0805JW-302ELF
R102, R103, R104, R105: 10k; R2012; MOUSER 652-CR0805FX-1002ELF
S101: DP04; DP-04; MOUSER 653-A6FR-2104
SV101: ML64L

Connections:
!AS: IC107.11 (IN11), SV101.13
!ATA_CS: IC106.14 (Y1)
!BG: SV101.9
!BGACK: SV101.8
!BR: SV101.7
!CS: IC101.19 (G), IC103.19 (G), IC104.19 (G), IC105.1 (GAB), IC106.4 (G2A), IC107.14 (IO14)
!DTACK: IC107.16 (IO16), SV101.10; also elsewhere on the board
!DUART_CS: IC106.15 (Y0); also elsewhere on the board
!EXTI_A: IC107.17 (IO17), SV101.16
!EXTI_B: SV101.15
!EXT_ID: IC107.6 (IN6), SV101.41
!HALT: SV101.5
!I2C_CS: IC106.9 (Y6)
!LCD_CS: IC106.11 (Y4)
!LDS: IC107.10 (IN10), SV101.11
!PIO_CS: IC106.12 (Y3); also elsewhere on the board
!PS2_CS: IC106.13 (Y2); also elsewhere on the board
!RD: IC101.1 (DIR), IC107.15 (IO15); also elsewhere on the board
!RESET: IC107.8 (IN8), SV101.6; also elsewhere on the board
!ROM_CS: IC106.6 (G1), IC107.22 (IO22); also elsewhere on the board
!STATUS_CS: IC106.10 (Y5)
!UDS: SV101.14
+5V: C101.1, C102.1, C103.+, C104.1, C105.1, C106.+, C107.1, C108.1, C109.+, C110.1, C111.+, C112.1, C113.1, C114.+, C115.1, IC101.20 (VCC), IC102.1 (B3), IC102.3 (A=B_I), IC102.16 (VCC), IC103.1 (DIR), IC103.20 (VCC), IC104.1 (DIR), IC104.20 (VCC), IC105.13 (GBA), IC105.14 (VCC), IC106.16 (VCC), IC107.24 (VCC), R101.1, S101.1, S101.2, S101.3, S101.4, SV101.1, SV101.2; also elsewhere on the board
A1: IC103.2 (A1), SV101.20
A2: IC103.3 (A2), SV101.22
A3: IC103.4 (A3), SV101.19
A4: IC103.5 (A4), SV101.24
A5: IC103.6 (A5), SV101.21
A6: IC103.7 (A6), SV101.23
A7: IC103.8 (A7), SV101.26
A8: IC103.9 (A8), IC107.7 (IN7), SV101.25
A9: IC104.2 (A1), IC107.4 (IN4), SV101.28
A10: IC104.3 (A2), SV101.27
A11: IC104.4 (A3), SV101.30
A12: IC104.5 (A4), SV101.29
A13: IC104.6 (A5), SV101.31
A14: IC104.7 (A6), SV101.32
A15: IC104.8 (A7), SV101.33
A16: IC104.9 (A8), SV101.34
A17: IC105.3 (A1), SV101.36
A18: IC105.4 (A2), SV101.35
A19: IC105.5 (A3), SV101.38
A20: IC102.10 (A0), SV101.37
A21: IC102.12 (A1), SV101.40
A22: IC102.13 (A2), SV101.39
A23: IC102.15 (A3), SV101.42
ADDR_MATCH: IC102.6 (A=B_O), IC107.13 (IN13)
ADDR_SET0: IC102.9 (B0), R105.1, S101.8
ADDR_SET1: IC102.11 (B1), R104.1, S101.7
ADDR_SET2: IC102.14 (B2), R103.1, S101.6
ADDR_SET3: IC107.5 (IN5), R102.1, S101.5
BOARD_A0: IC103.18 (B1); also elsewhere on the board
BOARD_A1: IC103.17 (B2); also elsewhere on the board
BOARD_A2: IC103.16 (B3); also elsewhere on the board
BOARD_A3: IC103.15 (B4); also elsewhere on the board
BOARD_A4: IC103.14 (B5); also elsewhere on the board
BOARD_A5: IC103.13 (B6); also elsewhere on the board
BOARD_A6: IC103.12 (B7); also elsewhere on the board
BOARD_A7: IC103.11 (B8); also elsewhere on the board
BOARD_A8: IC104.18 (B1); also elsewhere on the board
BOARD_A9: IC104.17 (B2); also elsewhere on the board
BOARD_A10: IC104.16 (B3); also elsewhere on the board
BOARD_A11: IC104.15 (B4); also elsewhere on the board
BOARD_A12: IC104.14 (B5); also elsewhere on the board
BOARD_A13: IC104.13 (B6), IC106.1 (A); also elsewhere on the board
BOARD_A14: IC104.12 (B7), IC106.2 (B); also elsewhere on the board
BOARD_A15: IC104.11 (B8), IC106.3 (C); also elsewhere on the board
BOARD_A16: IC105.11 (B1)
BOARD_A17: IC105.10 (B2)
BOARD_A18: IC105.9 (B3)
BOARD_D0: IC101.18 (B1); also elsewhere on the board
BOARD_D1: IC101.17 (B2); also elsewhere on the board
BOARD_D2: IC101.16 (B3); also elsewhere on the board
BOARD_D3: IC101.15 (B4); also elsewhere on the board
BOARD_D4: IC101.14 (B5); also elsewhere on the board
BOARD_D5: IC101.13 (B6); also elsewhere on the board
BOARD_D6: IC101.12 (B7); also elsewhere on the board
BOARD_D7: IC101.11 (B8); also elsewhere on the board
D0: IC101.2 (A1), SV101.62
D1: IC101.3 (A2), SV101.60
D2: IC101.4 (A3), SV101.58
D3: IC101.5 (A4), SV101.56
D4: IC101.6 (A5), SV101.54
D5: IC101.7 (A6), SV101.52
D6: IC101.8 (A7), SV101.50
D7: IC101.9 (A8), SV101.48
D8: SV101.57
D9: SV101.59
D10: SV101.61
D11: SV101.55
D12: SV101.53
D13: SV101.51
D14: SV101.49
D15: SV101.47
GND: C101.2, C102.2, C103.-, C104.2, C105.2, C106.-, C107.2, C108.2, C109.-, C110.2, C111.-, C112.2, C113.2, C114.-, C115.2, IC101.10 (GND), IC102.2 (A<B_I), IC102.4 (A>B_I), IC102.8 (GND), IC103.10 (GND), IC104.10 (GND), IC105.6 (A4), IC105.7 (GND), IC106.5 (G2B), IC106.8 (GND), IC107.12 (GND), LED101.C, R102.2, R103.2, R104.2, R105.2, SV101.3, SV101.4, SV101.17, SV101.18, SV101.45, SV101.46, SV101.63, SV101.64; also elsewhere on the board
unnamed: LED101.A, R101.2
R/!W!: IC107.9 (IN9), SV101.12; also elsewhere on the board

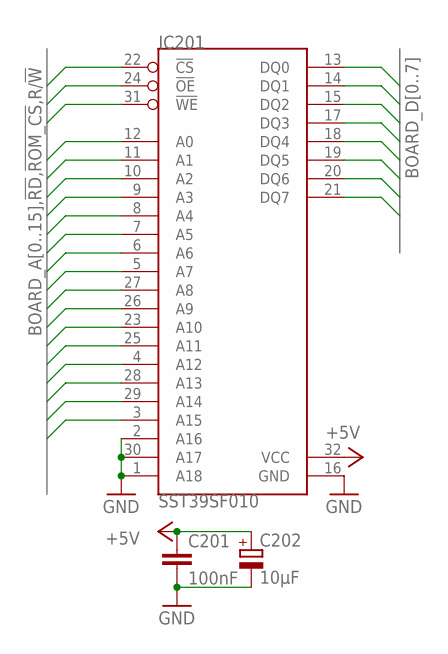
[picture p49: schematic io.sch, sheet 2, Card ID]

Parts:
C201: 100nF; C0805; MOUSER 710-885012207072
C202: 10µF; SMC_B; MOUSER 581-TAJB106K020RNJV
IC201: SST39SF010; PLCC-S32; MOUSER 579-SST3910A554INHET

Connections:
!RD: IC201.24 (!OE); also elsewhere on the board
!ROM_CS: IC201.22 (!CS); also elsewhere on the board
+5V: C201.1, C202.+, IC201.32 (VCC); also elsewhere on the board
BOARD_A0: IC201.12 (A0); also elsewhere on the board
BOARD_A1: IC201.11 (A1); also elsewhere on the board
BOARD_A2: IC201.10 (A2); also elsewhere on the board
BOARD_A3: IC201.9 (A3); also elsewhere on the board
BOARD_A4: IC201.8 (A4); also elsewhere on the board
BOARD_A5: IC201.7 (A5); also elsewhere on the board
BOARD_A6: IC201.6 (A6); also elsewhere on the board
BOARD_A7: IC201.5 (A7); also elsewhere on the board
BOARD_A8: IC201.27 (A8); also elsewhere on the board
BOARD_A9: IC201.26 (A9); also elsewhere on the board
BOARD_A10: IC201.23 (A10); also elsewhere on the board
BOARD_A11: IC201.25 (A11); also elsewhere on the board
BOARD_A12: IC201.4 (A12); also elsewhere on the board
BOARD_A13: IC201.28 (A13); also elsewhere on the board
BOARD_A14: IC201.29 (A14); also elsewhere on the board
BOARD_A15: IC201.3 (A15); also elsewhere on the board
BOARD_D0: IC201.13 (DQ0); also elsewhere on the board
BOARD_D1: IC201.14 (DQ1); also elsewhere on the board
BOARD_D2: IC201.15 (DQ2); also elsewhere on the board
BOARD_D3: IC201.17 (DQ3); also elsewhere on the board
BOARD_D4: IC201.18 (DQ4); also elsewhere on the board
BOARD_D5: IC201.19 (DQ5); also elsewhere on the board
BOARD_D6: IC201.20 (DQ6); also elsewhere on the board
BOARD_D7: IC201.21 (DQ7); also elsewhere on the board
GND: C201.2, C202.-, IC201.1 (A18), IC201.2 (A16), IC201.16 (GND), IC201.30 (A17); also elsewhere on the board
R/!W!: IC201.31 (!WE); also elsewhere on the board

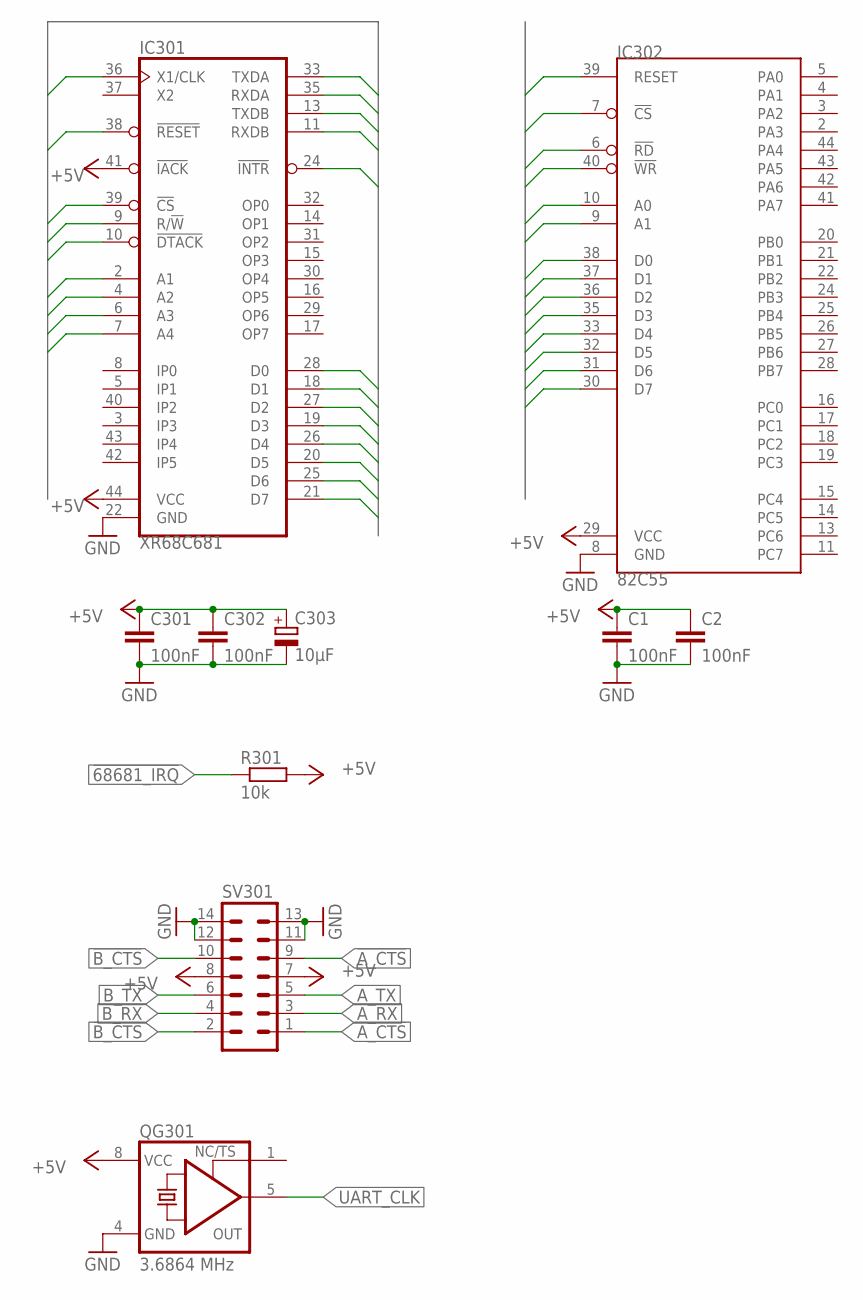
[picture p50: schematic io.sch, sheet 3, Serial/Parallel IO]

Parts:
C1, C2, C301, C302: 100nF; C0805; MOUSER 710-885012207072
C303: 10µF; SMC_B; MOUSER 581-TAJB106K020RNJV
IC301: XR68C681; PLCC-S44; MOUSER 701-XR68C681CJ-F
IC302: 82C55; PLCC-S44; MOUSER_SOCKET 940-44-044-24-000000
QG301: 3.6864 MHz; DIL08S; MOUSER 774-MXO45HS-3C-3.6
R301: 10k; R2012; MOUSER 652-CR0805FX-1002ELF
SV301: MA07-2W

Connections:
!68681_IRQ: IC301.24 (!INTR), R301.1
!A_CTS: SV301.1, SV301.9
!B_CTS: SV301.2, SV301.10
!DTACK: IC301.10 (!DTACK); also elsewhere on the board
!DUART_CS: IC301.39 (!CS); also elsewhere on the board
!LWE: IC301.9 (R/!W)
!PIO_CS: IC302.7 (!CS); also elsewhere on the board
!RD: IC302.6 (!RD); also elsewhere on the board
!RESET: IC301.38 (!RESET); also elsewhere on the board
+5V: C1.1, C2.1, C301.1, C302.1, C303.+, IC301.41 (!IACK), IC301.44 (VCC), IC302.29 (VCC), QG301.8 (VCC), R301.2, SV301.7, SV301.8; also elsewhere on the board
A_RX: IC301.35 (RXDA), SV301.3
A_TX: IC301.33 (TXDA), SV301.5
BOARD_A0: IC301.2 (A1), IC302.10 (A0); also elsewhere on the board
BOARD_A1: IC301.4 (A2), IC302.9 (A1); also elsewhere on the board
BOARD_A2: IC301.6 (A3); also elsewhere on the board
BOARD_A3: IC301.7 (A4); also elsewhere on the board
BOARD_D0: IC301.28 (D0), IC302.38 (D0); also elsewhere on the board
BOARD_D1: IC301.18 (D1), IC302.37 (D1); also elsewhere on the board
BOARD_D2: IC301.27 (D2), IC302.36 (D2); also elsewhere on the board
BOARD_D3: IC301.19 (D3), IC302.35 (D3); also elsewhere on the board
BOARD_D4: IC301.26 (D4), IC302.33 (D4); also elsewhere on the board
BOARD_D5: IC301.20 (D5), IC302.32 (D5); also elsewhere on the board
BOARD_D6: IC301.25 (D6), IC302.31 (D6); also elsewhere on the board
BOARD_D7: IC301.21 (D7), IC302.30 (D7); also elsewhere on the board
B_RX: IC301.11 (RXDB), SV301.4
B_TX: IC301.13 (TXDB), SV301.6
GND: C1.2, C2.2, C301.2, C302.2, C303.-, IC301.22 (GND), IC302.8 (GND), QG301.4 (GND), SV301.11, SV301.12, SV301.13, SV301.14; also elsewhere on the board
R/!W!: IC302.40 (!WR); also elsewhere on the board
RESET: IC302.39 (RESET); also elsewhere on the board
UART_CLK: IC301.36 (X1/CLK), QG301.5 (OUT); also elsewhere on the board

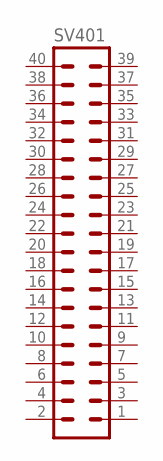
[picture p51: schematic io.sch, sheet 4, IDE Interface]

Parts:
SV401: ML40L

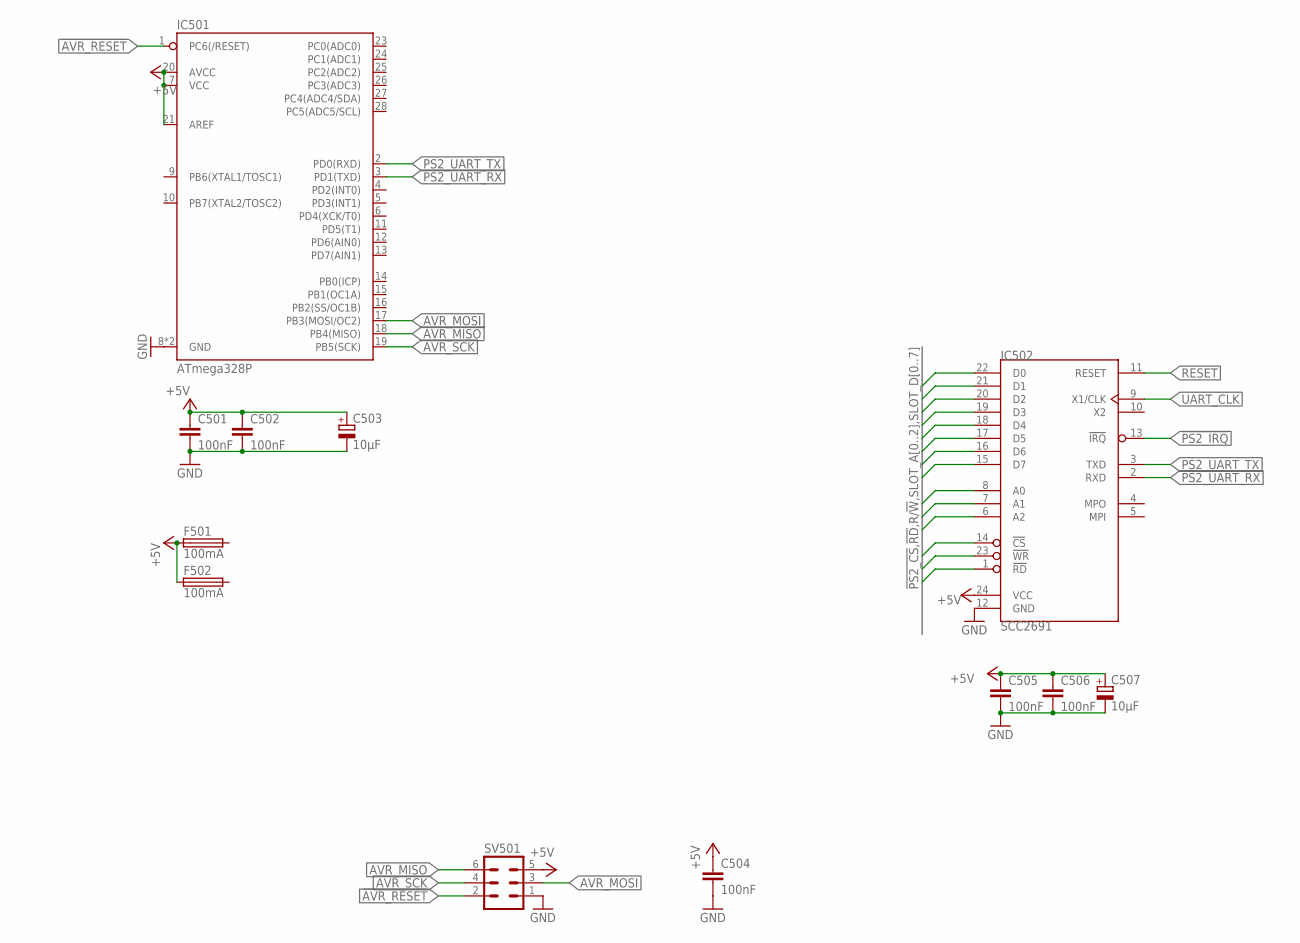
[picture p52: schematic io.sch, sheet 5, PS/2 Keyboard/Mouse]

Parts:
C501, C502, C504, C505, C506: 100nF; C0805; MOUSER 710-885012207072
C503, C507: 10µF; SMC_B; MOUSER 581-TAJB106K020RNJV
F501, F502: 100mA; WE-MI_1206; MOUSER 530-0ZCJ0010FF2E
IC501: ATmega328P; DIP28; MOUSER 556-ATMEGA328-PU
IC502: SCC2691; DIL24S; MOUSER_SOCKET 575-1104732441001000
SV501: ML6

Connections:
!AVR_RESET: IC501.1 (PC6(/RESET)), SV501.2
!PS2_CS: IC502.14 (!CS); also elsewhere on the board
!PS2_IRQ: IC502.13 (!IRQ)
!RD: IC502.1 (!RD); also elsewhere on the board
+5V: C501.1, C502.1, C503.+, C504.1, C505.1, C506.1, C507.+, F501.1, F502.1, IC501.7 (VCC), IC501.20 (AVCC), IC501.21 (AREF), IC502.24 (VCC), SV501.5; also elsewhere on the board
AVR_MISO: IC501.18 (PB4(MISO)), SV501.6
AVR_MOSI: IC501.17 (PB3(MOSI/OC2)), SV501.3
AVR_SCK: IC501.19 (PB5(SCK)), SV501.4
GND: C501.2, C502.2, C503.-, C504.2, C505.2, C506.2, C507.-, IC501.8 (GND), IC501.22 (GND), IC502.12 (GND), SV501.1; also elsewhere on the board
PS2_UART_RX: IC501.3 (PD1(TXD)), IC502.2 (RXD)
PS2_UART_TX: IC501.2 (PD0(RXD)), IC502.3 (TXD)
R/!W!: IC502.23 (!WR); also elsewhere on the board
RESET: IC502.11 (RESET); also elsewhere on the board
SLOT_A0: IC502.8 (A0)
SLOT_A1: IC502.7 (A1)
SLOT_A2: IC502.6 (A2)
SLOT_D0: IC502.22 (D0)
SLOT_D1: IC502.21 (D1)
SLOT_D2: IC502.20 (D2)
SLOT_D3: IC502.19 (D3)
SLOT_D4: IC502.18 (D4)
SLOT_D5: IC502.17 (D5)
SLOT_D6: IC502.16 (D6)
SLOT_D7: IC502.15 (D7)
UART_CLK: IC502.9 (X1/CLK); also elsewhere on the board

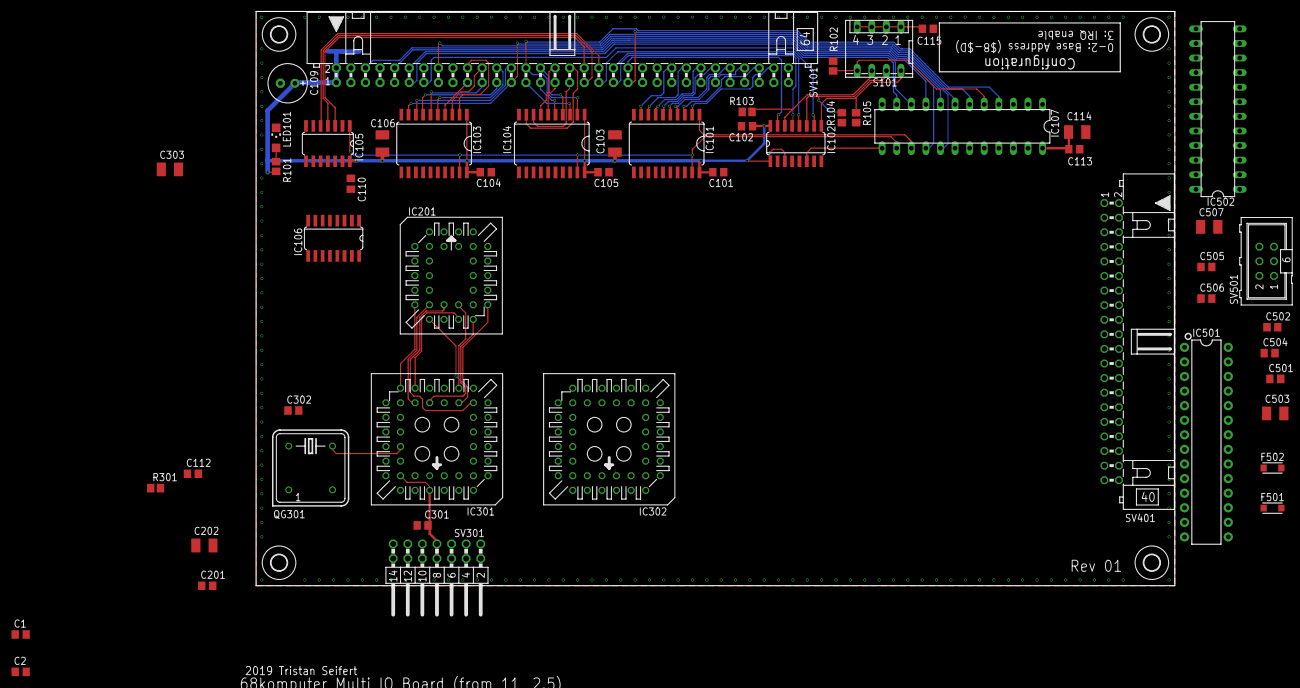
[picture p53: board io.brd from above]

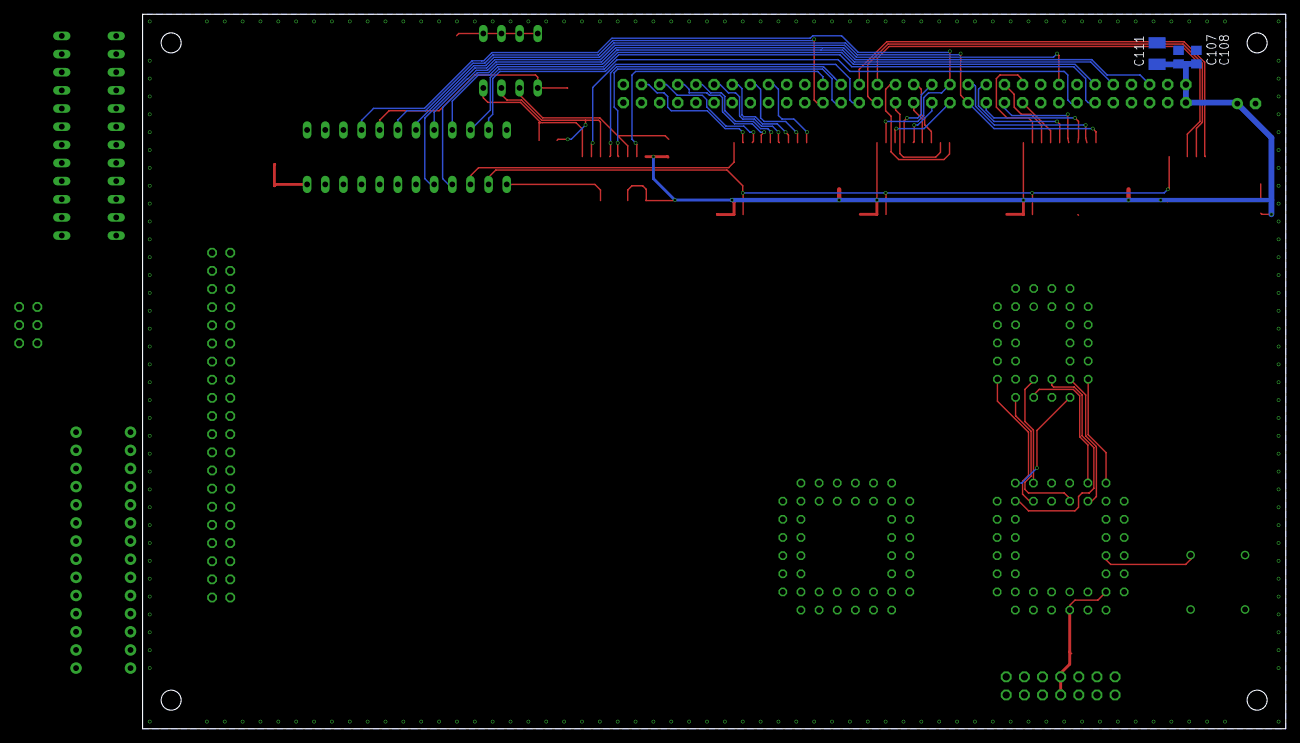
[picture p54: board io.brd from below]

Board: 2 copper layers, 160.0 x 100.0 mm, 60 parts (3 on the bottom side), 91 nets.
