tristanseifert/68komputer-hw/cpu-68008/backplane.brd

## EAGLE design cpu-68008/backplane.brd (2019-11-14)

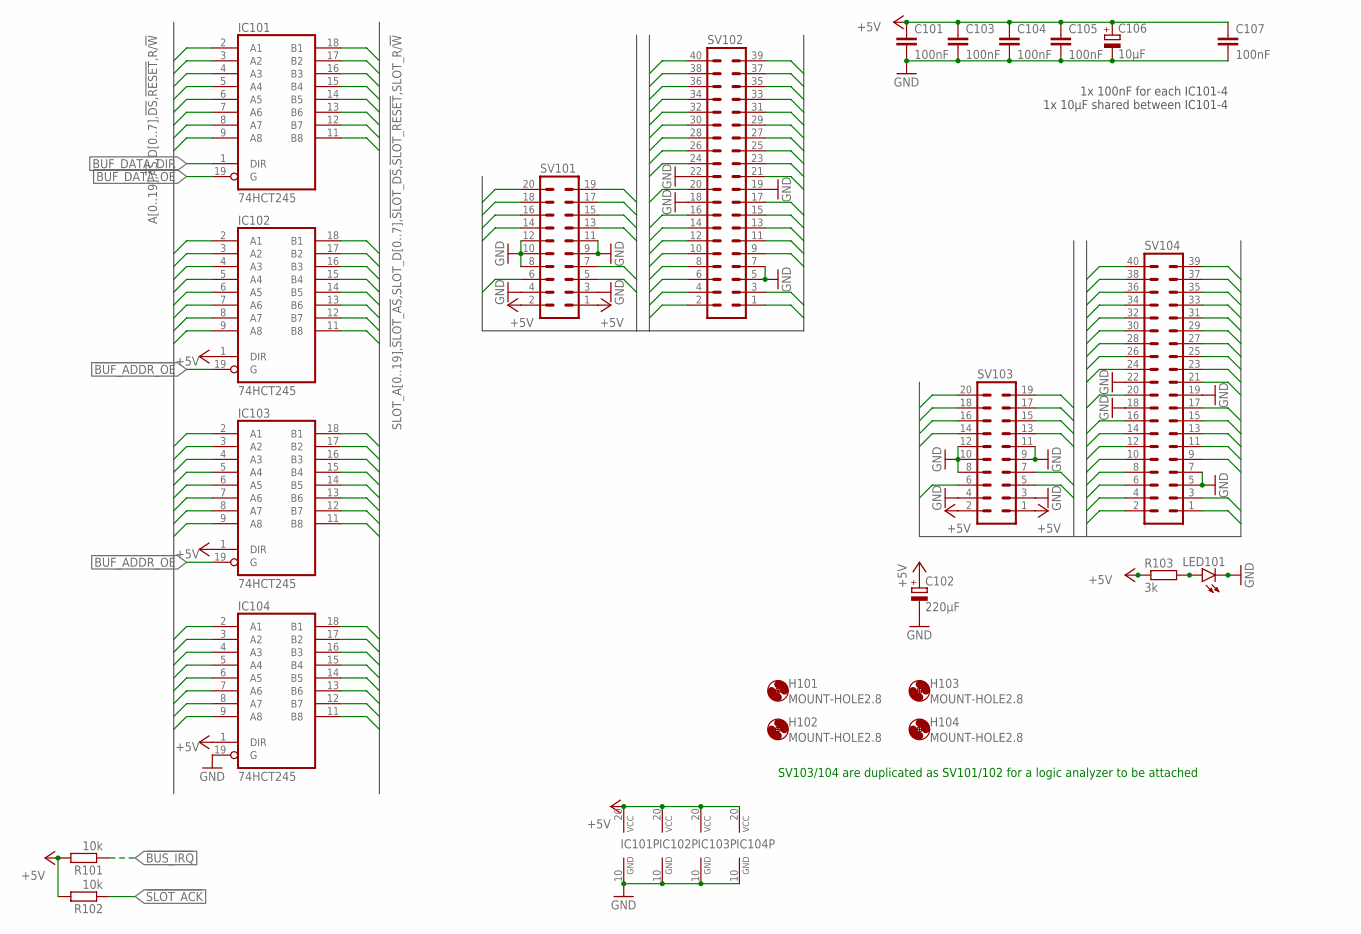
[picture p55: schematic backplane.sch, sheet 1, Expansion Input and Buffers]

Parts:
C101, C103, C104, C105, C107: 100nF; C0805; MOUSER 710-885012207072
C102: 220µF; E3,5-8; MOUSER 710-860020474012
C106: 10µF; SMC_B; MOUSER 581-TAJB106K020RNJV
H101, H102, H103, H104: MOUNT-HOLE2.8; 2,8
IC101, IC102, IC103, IC104: 74HCT245; SO20W; MOUSER 595-SN74HCT245DBR
LED101: LEDCHIPLED_1206; CHIPLED_1206; MOUSER 710-156120YS75300
R101, R102: 10k; R2012; MOUSER 652-CR0805FX-1002ELF
R103: 3k; R2012; MOUSER 652-CR0805JW-302ELF
SV101: MA10-2
SV102: MA20-2
SV103: MA10-2W
SV104: MA20-2W

Connections:
!AS: IC104.2 (A1), SV102.33, SV104.33
!BERR: SV102.9, SV104.9
!BG: SV102.25, SV104.25
!BR: SV102.23, SV104.23
!BUF_ADDR_OE: IC102.19 (G), IC103.19 (G); also elsewhere on the board
!BUF_DATA_OE: IC101.19 (G); also elsewhere on the board
!BUS_CS: SV101.7, SV103.7; also elsewhere on the board
!BUS_DTACK: SV101.6, SV103.6; also elsewhere on the board
!BUS_IRQ: R101.1, SV101.5, SV103.5; also elsewhere on the board
!DS: IC104.3 (A2), SV102.31, SV104.31
!DTACK: SV102.27, SV104.27
!HALT: SV102.17, SV104.17
!RESET: IC104.9 (A8), SV102.15, SV104.15
!SLOT_ACK: R102.1; also elsewhere on the board
!SLOT_AS: IC104.18 (B1); also elsewhere on the board
!SLOT_DS: IC104.17 (B2); also elsewhere on the board
!SLOT_RESET: IC104.11 (B8); also elsewhere on the board
!VPA: SV102.11, SV104.11
+5V: C101.1, C102.+, C103.1, C104.1, C105.1, C106.+, C107.1, IC101.20 (VCC), IC102.1 (DIR), IC102.20 (VCC), IC103.1 (DIR), IC103.20 (VCC), IC104.1 (DIR), IC104.20 (VCC), R101.2, R102.2, R103.1, SV101.1, SV101.2, SV103.1, SV103.2; also elsewhere on the board
A0: IC102.5 (A4), SV101.17, SV103.17
A1: IC102.7 (A6), SV101.15, SV103.15
A2: IC102.9 (A8), SV101.13, SV103.13
A3: IC102.8 (A7), SV101.14, SV103.14
A4: IC102.6 (A5), SV101.16, SV103.16
A5: IC102.4 (A3), SV101.18, SV103.18
A6: IC102.3 (A2), SV101.20, SV103.20
A7: IC102.2 (A1), SV102.2, SV104.2
A8: IC103.9 (A8), SV102.4, SV104.4
A9: IC103.8 (A7), SV102.6, SV104.6
A10: IC103.7 (A6), SV102.8, SV104.8
A11: IC103.6 (A5), SV102.10, SV104.10
A12: IC103.5 (A4), SV102.12, SV104.12
A13: IC103.4 (A3), SV102.14, SV104.14
A14: IC103.3 (A2), SV102.16, SV104.16
A15: IC103.2 (A1), SV102.20, SV104.20
A16: IC104.8 (A7), SV102.24, SV104.24
A17: IC104.7 (A6), SV102.26, SV104.26
A18: IC104.6 (A5), SV102.28, SV104.28
A19: IC104.4 (A3), SV102.30, SV104.30
BUF_DATA_DIR: IC101.1 (DIR); also elsewhere on the board
CLK: SV102.21, SV104.21; also elsewhere on the board
D0: IC101.7 (A6), SV102.35, SV104.35
D1: IC101.5 (A4), SV102.37, SV104.37
D2: IC101.3 (A2), SV102.39, SV104.39
D3: IC101.2 (A1), SV102.40, SV104.40
D4: IC101.4 (A3), SV102.38, SV104.38
D5: IC101.6 (A5), SV102.36, SV104.36
D6: IC101.8 (A7), SV102.34, SV104.34
D7: IC101.9 (A8), SV102.32, SV104.32
E: SV102.13, SV104.13
FC0: SV101.19, SV103.19
FC1: SV102.1, SV104.1
FC2: SV102.3, SV104.3
GND: C101.2, C102.-, C103.2, C104.2, C105.2, C106.-, C107.2, IC101.10 (GND), IC102.10 (GND), IC103.10 (GND), IC104.10 (GND), IC104.19 (G), LED101.C, SV101.3, SV101.4, SV101.8, SV101.9, SV101.10, SV101.11, SV101.12, SV102.5, SV102.7, SV102.18, SV102.19, SV102.22, SV103.3, SV103.4, SV103.8, SV103.9, SV103.10, SV103.11, SV103.12, SV104.5, SV104.7, SV104.18, SV104.19, SV104.22; also elsewhere on the board
unnamed: LED101.A, R103.2
R/!W!: IC104.5 (A4), SV102.29, SV104.29
SLOT_A0: IC102.15 (B4); also elsewhere on the board
SLOT_A1: IC102.13 (B6); also elsewhere on the board
SLOT_A2: IC102.11 (B8); also elsewhere on the board
SLOT_A3: IC102.12 (B7); also elsewhere on the board
SLOT_A4: IC102.14 (B5); also elsewhere on the board
SLOT_A5: IC102.16 (B3); also elsewhere on the board
SLOT_A6: IC102.17 (B2); also elsewhere on the board
SLOT_A7: IC102.18 (B1); also elsewhere on the board
SLOT_A8: IC103.11 (B8); also elsewhere on the board
SLOT_A9: IC103.12 (B7); also elsewhere on the board
SLOT_A10: IC103.13 (B6); also elsewhere on the board
SLOT_A11: IC103.14 (B5); also elsewhere on the board
SLOT_A12: IC103.15 (B4); also elsewhere on the board
SLOT_A13: IC103.16 (B3); also elsewhere on the board
SLOT_A14: IC103.17 (B2); also elsewhere on the board
SLOT_A15: IC103.18 (B1); also elsewhere on the board
SLOT_A16: IC104.12 (B7); also elsewhere on the board
SLOT_A17: IC104.13 (B6); also elsewhere on the board
SLOT_A18: IC104.14 (B5); also elsewhere on the board
SLOT_A19: IC104.16 (B3); also elsewhere on the board
SLOT_D0: IC101.13 (B6); also elsewhere on the board
SLOT_D1: IC101.15 (B4); also elsewhere on the board
SLOT_D2: IC101.17 (B2); also elsewhere on the board
SLOT_D3: IC101.18 (B1); also elsewhere on the board
SLOT_D4: IC101.16 (B3); also elsewhere on the board
SLOT_D5: IC101.14 (B5); also elsewhere on the board
SLOT_D6: IC101.12 (B7); also elsewhere on the board
SLOT_D7: IC101.11 (B8); also elsewhere on the board
SLOT_R/!W!: IC104.15 (B4); also elsewhere on the board

Notes on the sheet:
1x 100nF for each IC101-4 1x 10µF shared between IC101-4
SV103/104 are duplicated as SV101/102 for a logic analyzer to be attached

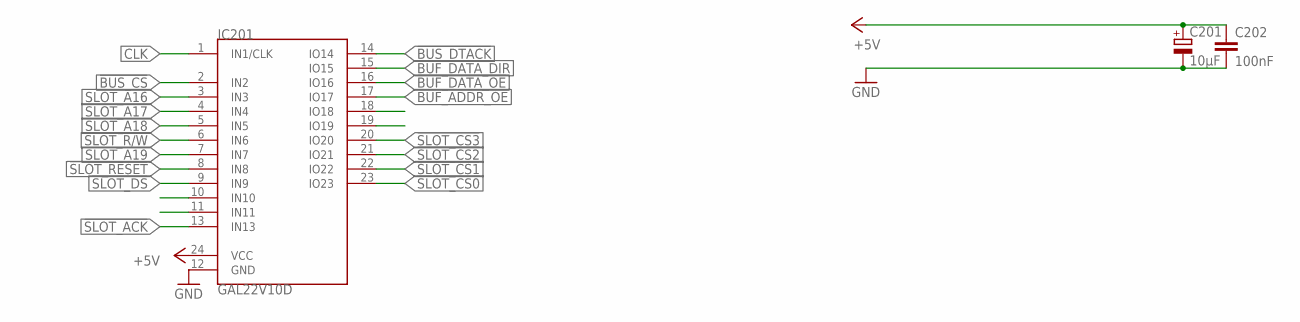
[picture p56: schematic backplane.sch, sheet 2, Logic]

Parts:
C201: 10µF; SMC_B; MOUSER 581-TAJB106K020RNJV
C202: 100nF; C0805; MOUSER 710-885012207072
IC201: GAL22V10D; DIL24S; MOUSER_SOCKET 575-11044324

Connections:
!BUF_ADDR_OE: IC201.17 (IO17); also elsewhere on the board
!BUF_DATA_OE: IC201.16 (IO16); also elsewhere on the board
!BUS_CS: IC201.2 (IN2); also elsewhere on the board
!BUS_DTACK: IC201.14 (IO14); also elsewhere on the board
!SLOT_ACK: IC201.13 (IN13); also elsewhere on the board
!SLOT_CS0: IC201.23 (IO23); also elsewhere on the board
!SLOT_CS1: IC201.22 (IO22); also elsewhere on the board
!SLOT_CS2: IC201.21 (IO21); also elsewhere on the board
!SLOT_CS3: IC201.20 (IO20); also elsewhere on the board
!SLOT_DS: IC201.9 (IN9); also elsewhere on the board
!SLOT_RESET: IC201.8 (IN8); also elsewhere on the board
+5V: C201.+, C202.1, IC201.24 (VCC); also elsewhere on the board
BUF_DATA_DIR: IC201.15 (IO15); also elsewhere on the board
CLK: IC201.1 (IN1/CLK); also elsewhere on the board
GND: C201.-, C202.2, IC201.12 (GND); also elsewhere on the board
SLOT_A16: IC201.3 (IN3); also elsewhere on the board
SLOT_A17: IC201.4 (IN4); also elsewhere on the board
SLOT_A18: IC201.5 (IN5); also elsewhere on the board
SLOT_A19: IC201.7 (IN7); also elsewhere on the board
SLOT_R/!W!: IC201.6 (IN6); also elsewhere on the board

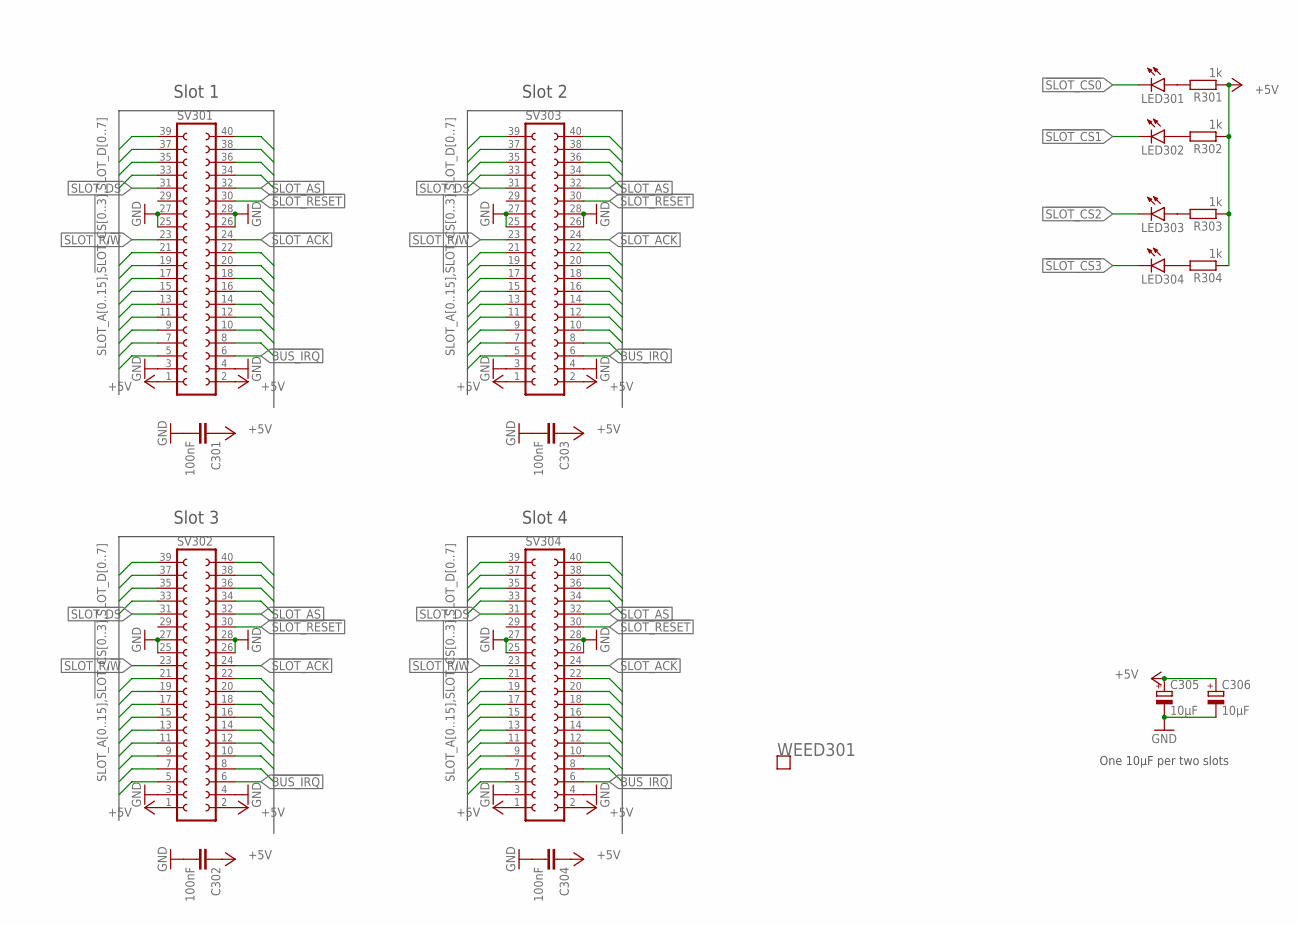
[picture p57: schematic backplane.sch, sheet 3, Expansion Slots]

Parts:
C301, C302, C303, C304: 100nF; C0805; MOUSER 710-885012207072
C305, C306: 10µF; SMC_B; MOUSER 581-TAJB106K020RNJV
LED301, LED302, LED303, LED304: LEDCHIPLED_1206; CHIPLED_1206; MOUSER 710-156120VS75300
R301, R302, R303, R304: 1k; R2012; MOUSER 652-CR0805FX-1001ELF
SV301, SV302, SV303, SV304: FE20-2; MOUSER 710-61304021821
WEED301: WEED; DOINK

Connections:
!BUS_IRQ: SV301.6, SV302.6, SV303.6, SV304.6; also elsewhere on the board
!SLOT_ACK: SV301.24, SV302.24, SV303.24, SV304.24; also elsewhere on the board
!SLOT_AS: SV301.32, SV302.32, SV303.32, SV304.32; also elsewhere on the board
!SLOT_CS0: LED301.C, SV301.5; also elsewhere on the board
!SLOT_CS1: LED302.C, SV303.5; also elsewhere on the board
!SLOT_CS2: LED303.C, SV302.5; also elsewhere on the board
!SLOT_CS3: LED304.C, SV304.5; also elsewhere on the board
!SLOT_DS: SV301.31, SV302.31, SV303.31, SV304.31; also elsewhere on the board
!SLOT_RESET: SV301.30, SV302.30, SV303.30, SV304.30; also elsewhere on the board
+5V: C301.1, C302.1, C303.1, C304.1, C305.+, C306.+, R301.1, R302.1, R303.1, R304.1, SV301.1, SV301.2, SV302.1, SV302.2, SV303.1, SV303.2, SV304.1, SV304.2; also elsewhere on the board
GND: C301.2, C302.2, C303.2, C304.2, C305.-, C306.-, SV301.3, SV301.4, SV301.25, SV301.26, SV301.27, SV301.28, SV302.3, SV302.4, SV302.25, SV302.26, SV302.27, SV302.28, SV303.3, SV303.4, SV303.25, SV303.26, SV303.27, SV303.28, SV304.3, SV304.4, SV304.25, SV304.26, SV304.27, SV304.28; also elsewhere on the board
unnamed: LED302.A, R302.2
unnamed: LED301.A, R301.2
unnamed: LED304.A, R304.2
unnamed: LED303.A, R303.2
SLOT_A0: SV301.12, SV302.12, SV303.12, SV304.12; also elsewhere on the board
SLOT_A1: SV301.10, SV302.10, SV303.10, SV304.10; also elsewhere on the board
SLOT_A2: SV301.8, SV302.8, SV303.8, SV304.8; also elsewhere on the board
SLOT_A3: SV301.7, SV302.7, SV303.7, SV304.7; also elsewhere on the board
SLOT_A4: SV301.9, SV302.9, SV303.9, SV304.9; also elsewhere on the board
SLOT_A5: SV301.11, SV302.11, SV303.11, SV304.11; also elsewhere on the board
SLOT_A6: SV301.14, SV302.14, SV303.14, SV304.14; also elsewhere on the board
SLOT_A7: SV301.13, SV302.13, SV303.13, SV304.13; also elsewhere on the board
SLOT_A8: SV301.16, SV302.16, SV303.16, SV304.16; also elsewhere on the board
SLOT_A9: SV301.15, SV302.15, SV303.15, SV304.15; also elsewhere on the board
SLOT_A10: SV301.18, SV302.18, SV303.18, SV304.18; also elsewhere on the board
SLOT_A11: SV301.17, SV302.17, SV303.17, SV304.17; also elsewhere on the board
SLOT_A12: SV301.20, SV302.20, SV303.20, SV304.20; also elsewhere on the board
SLOT_A13: SV301.19, SV302.19, SV303.19, SV304.19; also elsewhere on the board
SLOT_A14: SV301.22, SV302.22, SV303.22, SV304.22; also elsewhere on the board
SLOT_A15: SV301.21, SV302.21, SV303.21, SV304.21; also elsewhere on the board
SLOT_D0: SV301.35, SV302.35, SV303.35, SV304.35; also elsewhere on the board
SLOT_D1: SV301.37, SV302.37, SV303.37, SV304.37; also elsewhere on the board
SLOT_D2: SV301.39, SV302.39, SV303.39, SV304.39; also elsewhere on the board
SLOT_D3: SV301.40, SV302.40, SV303.40, SV304.40; also elsewhere on the board
SLOT_D4: SV301.38, SV302.38, SV303.38, SV304.38; also elsewhere on the board
SLOT_D5: SV301.36, SV302.36, SV303.36, SV304.36; also elsewhere on the board
SLOT_D6: SV301.34, SV302.34, SV303.34, SV304.34; also elsewhere on the board
SLOT_D7: SV301.33, SV302.33, SV303.33, SV304.33; also elsewhere on the board
SLOT_R/!W!: SV301.23, SV302.23, SV303.23, SV304.23; also elsewhere on the board

Notes on the sheet:
Slot 1
Slot 2
Slot 3
Slot 4
One 10µF per two slots

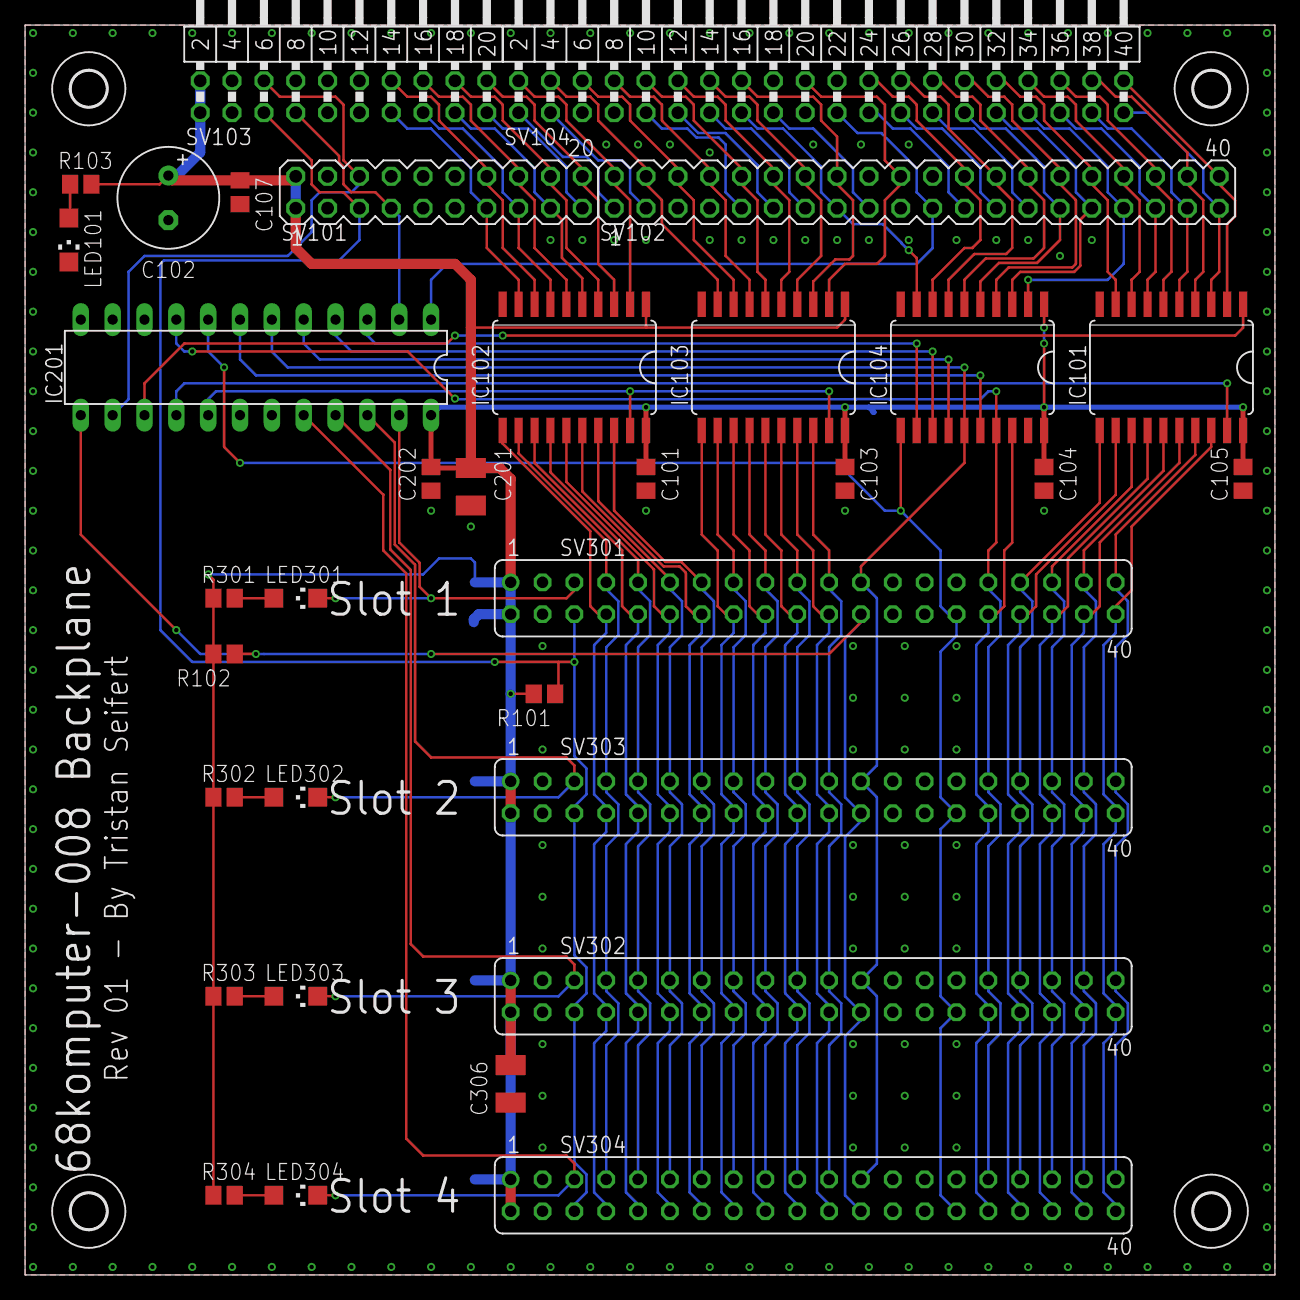
[picture p58: board backplane.brd from above]

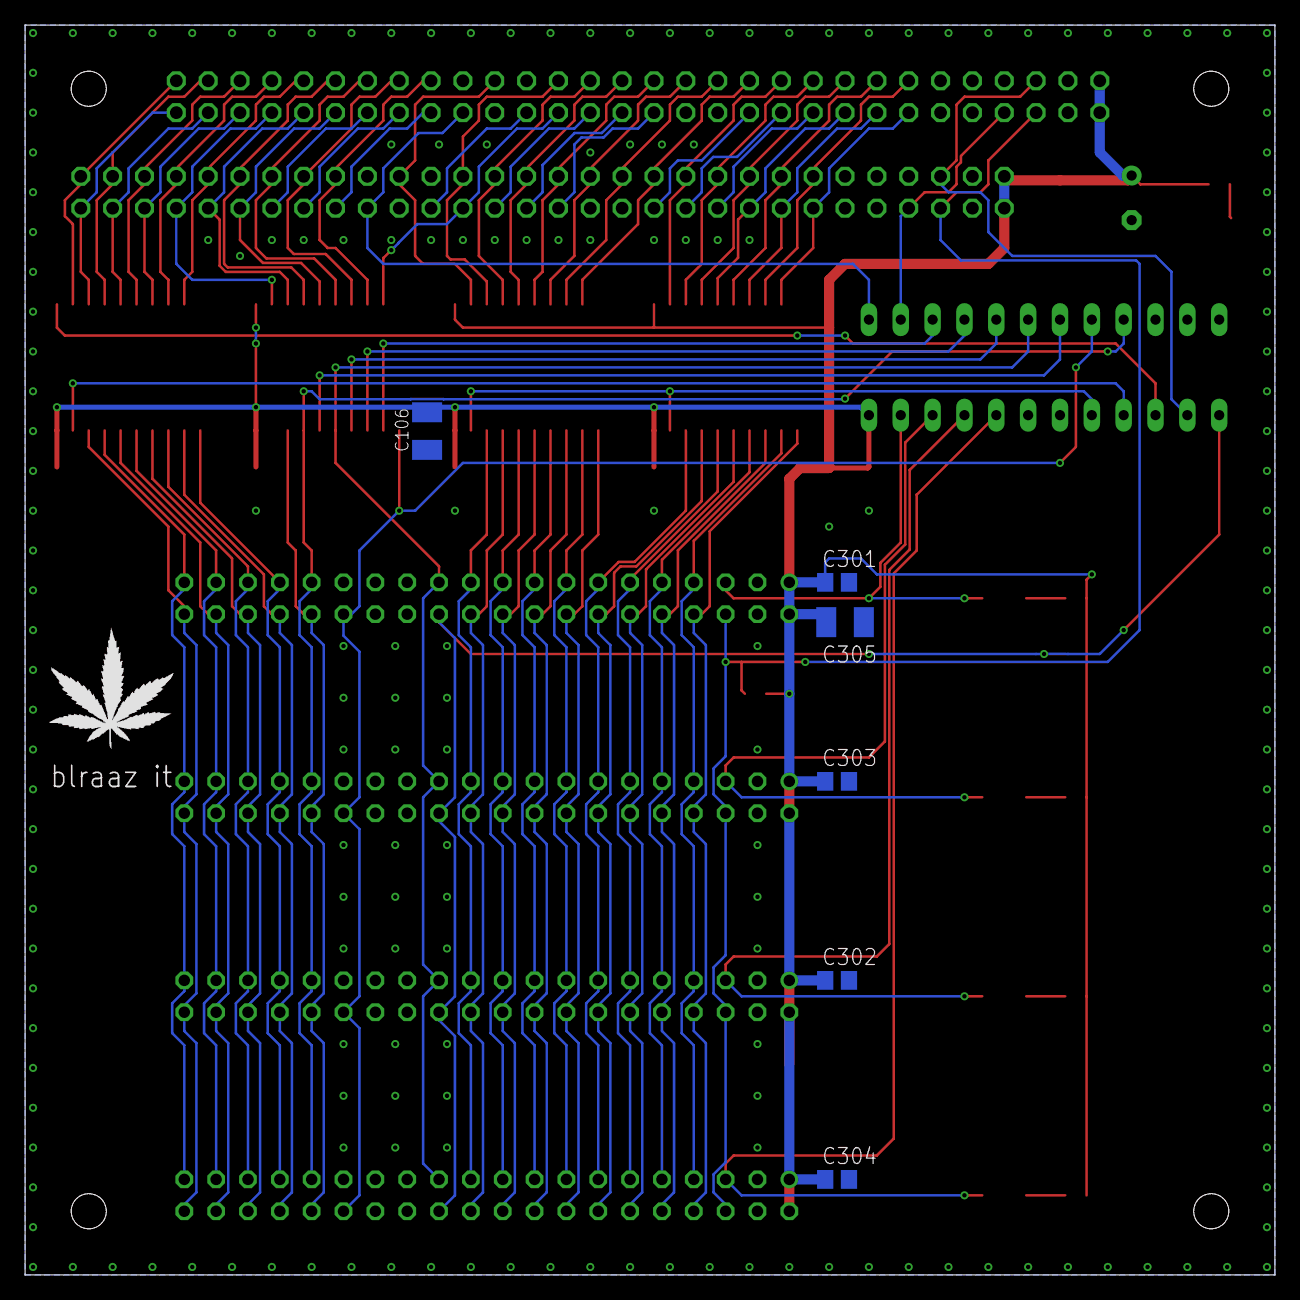
[picture p59: board backplane.brd from below]

Board: 2 copper layers, 99.7 x 99.7 mm, 45 parts (7 on the bottom side), 93 nets.
