tristanseifert/68komputer-hw/cpu-68008/tms9918.brd

## EAGLE design cpu-68008/tms9918.brd (2019-11-14)

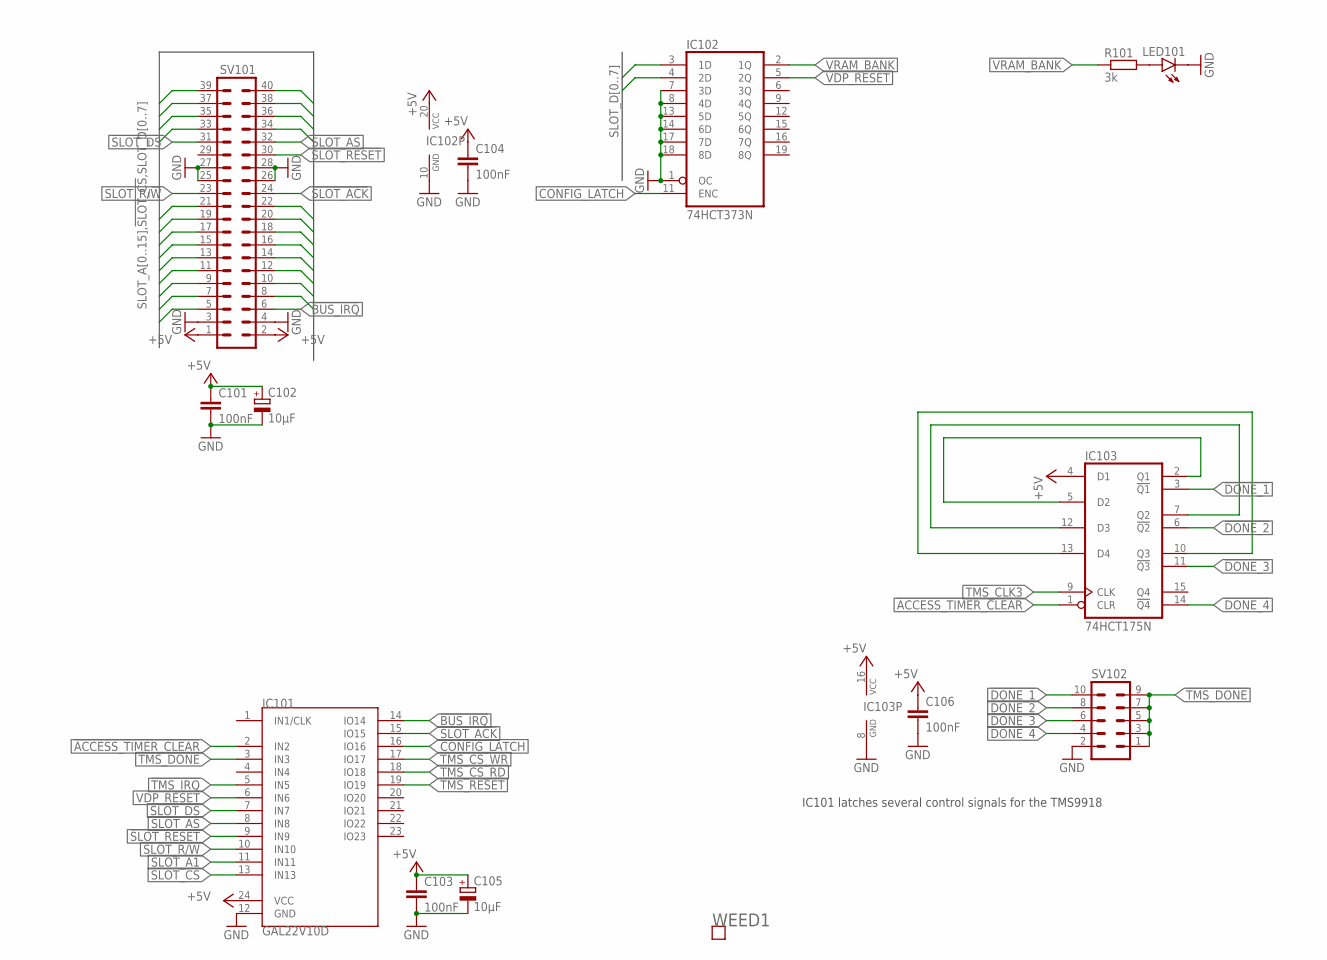
[picture p60: schematic tms9918.sch, sheet 1, Bus interface]

Parts:
C101, C103, C104, C106: 100nF; C0805; MOUSER 710-885012207072
C102, C105: 10µF; SMC_B; MOUSER 581-TAJB106K020RNJV
IC101: GAL22V10D; DIL24S; MOUSER_SOCKET 575-11044324
IC102: 74HCT373N; DIL20; MOUSER 595-SN74HCT373N
IC103: 74HCT175N; DIL16; MOUSER 595-CD74HCT175E
LED101: LEDCHIPLED_1206; CHIPLED_1206; MOUSER 710-156120VS75300
R101: 3k; R2012; MOUSER 652-CR0805JW-302ELF
SV101: MA20-2W
SV102: MA05-2
WEED1: WEED; DOINK

Connections:
!ACCESS_TIMER_CLEAR: IC101.2 (IN2), IC103.1 (CLR)
!BUS_IRQ: IC101.14 (IO14), SV101.6
!DONE_1: IC103.3 (!Q1), SV102.10
!DONE_2: IC103.6 (!Q2), SV102.8
!DONE_3: IC103.11 (!Q3), SV102.6
!DONE_4: IC103.14 (!Q4), SV102.4
!SLOT_ACK: IC101.15 (IO15), SV101.24
!SLOT_AS: IC101.8 (IN8), SV101.32
!SLOT_CS: IC101.13 (IN13), SV101.5
!SLOT_DS: IC101.7 (IN7), SV101.31
!SLOT_RESET: IC101.9 (IN9), SV101.30
!TMS_CS_RD: IC101.18 (IO18); also elsewhere on the board
!TMS_CS_WR: IC101.17 (IO17); also elsewhere on the board
!TMS_DONE: IC101.3 (IN3), SV102.1, SV102.3, SV102.5, SV102.7, SV102.9
!TMS_IRQ: IC101.5 (IN5); also elsewhere on the board
!TMS_RESET: IC101.19 (IO19); also elsewhere on the board
+5V: C101.1, C102.+, C103.1, C104.1, C105.+, C106.1, IC101.24 (VCC), IC102.20 (VCC), IC103.4 (D1), IC103.16 (VCC), SV101.1, SV101.2; also elsewhere on the board
CONFIG_LATCH: IC101.16 (IO16), IC102.11 (ENC)
GND: C101.2, C102.-, C103.2, C104.2, C105.-, C106.2, IC101.12 (GND), IC102.1 (OC), IC102.7 (3D), IC102.8 (4D), IC102.10 (GND), IC102.13 (5D), IC102.14 (6D), IC102.17 (7D), IC102.18 (8D), IC103.8 (GND), LED101.C, SV101.3, SV101.4, SV101.25, SV101.26, SV101.27, SV101.28, SV102.2; also elsewhere on the board
unnamed: IC103.2 (Q1), IC103.5 (D2)
unnamed: IC103.7 (Q2), IC103.12 (D3)
unnamed: IC103.10 (Q3), IC103.13 (D4)
unnamed: LED101.A, R101.2
SLOT_A0: SV101.12; also elsewhere on the board
SLOT_A1: IC101.11 (IN11), SV101.10
SLOT_A2: SV101.8
SLOT_A3: SV101.7
SLOT_A4: SV101.9
SLOT_A5: SV101.11
SLOT_A6: SV101.14
SLOT_A7: SV101.13
SLOT_A8: SV101.16
SLOT_A9: SV101.15
SLOT_A10: SV101.18
SLOT_A11: SV101.17
SLOT_A12: SV101.20
SLOT_A13: SV101.19
SLOT_A14: SV101.22
SLOT_A15: SV101.21
SLOT_D0: IC102.3 (1D), SV101.35; also elsewhere on the board
SLOT_D1: IC102.4 (2D), SV101.37; also elsewhere on the board
SLOT_D2: SV101.39; also elsewhere on the board
SLOT_D3: SV101.40; also elsewhere on the board
SLOT_D4: SV101.38; also elsewhere on the board
SLOT_D5: SV101.36; also elsewhere on the board
SLOT_D6: SV101.34; also elsewhere on the board
SLOT_D7: SV101.33; also elsewhere on the board
SLOT_R/!W!: IC101.10 (IN10), SV101.23
TMS_CLK3: IC103.9 (CLK); also elsewhere on the board
VDP_RESET: IC101.6 (IN6), IC102.5 (2Q)
VRAM_BANK: IC102.2 (1Q), R101.1; also elsewhere on the board

Notes on the sheet:
IC101 latches several control signals for the TMS9918

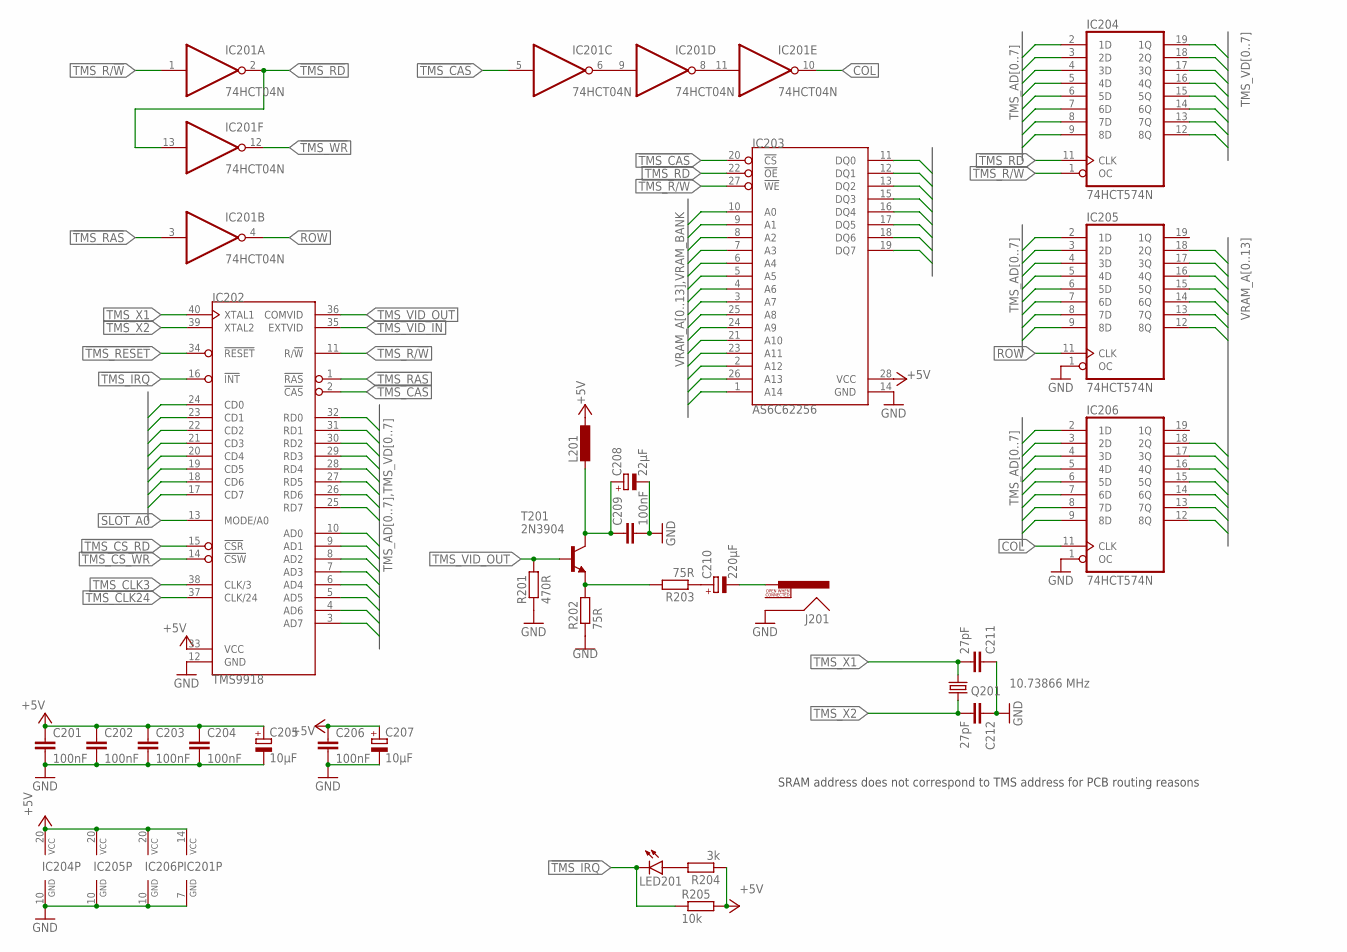
[picture p61: schematic tms9918.sch, sheet 2, Video Controller/DRAM Emulation]

Parts:
C201, C202, C203, C204, C206, C209: 100nF; C0805; MOUSER 710-885012207072
C205, C207: 10µF; SMC_B; MOUSER 581-TAJB106K020RNJV
C208: 22µF; E2-5; MOUSER 710-860010372002
C210: 220µF; E2,5-7; MOUSER 710-860020373010
C211, C212: 27pF; C0805; MOUSER 80-C0805C270K5HACTU
IC201: 74HCT04N; DIL14; MOUSER 595-SN74HCT04N
IC202: TMS9918; DIL40
IC203: AS6C62256; DIL28-6; MOUSER_SOCKET 575-1104762841001000
IC204, IC205, IC206: 74HCT574N; DIL20; MOUSER 595-SN74HCT574N
J201: RCALOCK; RCA_LOCK; MOUSER 502-PJRAN1X1U04AU
L201: L-EUL2012C; L2012C; MOUSER 963-BK2125HS101-T
LED201: LEDCHIPLED_1206; CHIPLED_1206; MOUSER 710-156120VS75300
Q201: 10.73866 MHz; HC49/S; MOUSER 449-LFXTAL029962REEL
R201: 470R; R2012; MOUSER 652-CR0805FX-4700ELF
R202, R203: 75R; R2012; MOUSER 652-CR0805FX-75R0ELF
R204: 3k; R2012; MOUSER 652-CR0805JW-302ELF
R205: 10k; R2012; MOUSER 652-CR0805FX-1002ELF
T201: 2N3904; TO92; MOUSER 512-2N3904BU

Connections:
!TMS_CAS: IC201.5 (I), IC202.2 (!CAS), IC203.20 (!CS)
!TMS_CS_RD: IC202.15 (!CSR); also elsewhere on the board
!TMS_CS_WR: IC202.14 (!CSW); also elsewhere on the board
!TMS_IRQ: IC202.16 (!INT), LED201.C, R205.1; also elsewhere on the board
!TMS_RAS: IC201.3 (I), IC202.1 (!RAS)
!TMS_RD: IC201.2 (O), IC201.13 (I), IC203.22 (!OE), IC204.11 (CLK)
!TMS_RESET: IC202.34 (!RESET); also elsewhere on the board
!TMS_WR: IC201.12 (O)
+5V: C201.1, C202.1, C203.1, C204.1, C205.+, C206.1, C207.+, IC201.14 (VCC), IC202.33 (VCC), IC203.28 (VCC), IC204.20 (VCC), IC205.20 (VCC), IC206.20 (VCC), L201.1, R204.1, R205.2; also elsewhere on the board
COL: IC201.10 (O), IC206.11 (CLK)
GND: C201.2, C202.2, C203.2, C204.2, C205.-, C206.2, C207.-, C208.-, C209.2, C211.1, C212.1, IC201.7 (GND), IC202.12 (GND), IC203.14 (GND), IC204.10 (GND), IC205.1 (OC), IC205.10 (GND), IC206.1 (OC), IC206.10 (GND), J201.SHELL, R201.1, R202.1; also elsewhere on the board
unnamed: IC201.8 (O), IC201.11 (I)
unnamed: IC201.6 (O), IC201.9 (I)
unnamed: C208.+, C209.1, L201.2, T201.1 (C)
unnamed: R202.2, R203.2, T201.3 (E)
unnamed: C210.+, R203.1
unnamed: C210.-, J201.PIN
unnamed: LED201.A, R204.2
ROW: IC201.4 (O), IC205.11 (CLK)
SLOT_A0: IC202.13 (MODE/A0); also elsewhere on the board
SLOT_D0: IC202.17 (CD7); also elsewhere on the board
SLOT_D1: IC202.18 (CD6); also elsewhere on the board
SLOT_D2: IC202.19 (CD5); also elsewhere on the board
SLOT_D3: IC202.20 (CD4); also elsewhere on the board
SLOT_D4: IC202.21 (CD3); also elsewhere on the board
SLOT_D5: IC202.22 (CD2); also elsewhere on the board
SLOT_D6: IC202.23 (CD1); also elsewhere on the board
SLOT_D7: IC202.24 (CD0); also elsewhere on the board
TMS_AD0: IC202.10 (AD0), IC204.2 (1D), IC205.9 (8D), IC206.9 (8D)
TMS_AD1: IC202.9 (AD1), IC204.3 (2D), IC205.8 (7D), IC206.8 (7D)
TMS_AD2: IC202.8 (AD2), IC204.4 (3D), IC205.7 (6D), IC206.7 (6D)
TMS_AD3: IC202.7 (AD3), IC204.5 (4D), IC205.6 (5D), IC206.6 (5D)
TMS_AD4: IC202.6 (AD4), IC204.6 (5D), IC205.5 (4D), IC206.5 (4D)
TMS_AD5: IC202.5 (AD5), IC204.7 (6D), IC205.4 (3D), IC206.4 (3D)
TMS_AD6: IC202.4 (AD6), IC204.8 (7D), IC205.3 (2D), IC206.3 (2D)
TMS_AD7: IC202.3 (AD7), IC204.9 (8D), IC205.2 (1D), IC206.2 (1D)
TMS_CLK3: IC202.38 (CLK/3); also elsewhere on the board
TMS_CLK24: IC202.37 (CLK/24)
TMS_R/!W!: IC201.1 (I), IC202.11 (R/!W!), IC203.27 (!WE), IC204.1 (OC)
TMS_VD0: IC202.32 (RD0), IC203.11 (DQ0), IC204.19 (1Q)
TMS_VD1: IC202.31 (RD1), IC203.12 (DQ1), IC204.18 (2Q)
TMS_VD2: IC202.30 (RD2), IC203.13 (DQ2), IC204.17 (3Q)
TMS_VD3: IC202.29 (RD3), IC203.15 (DQ3), IC204.16 (4Q)
TMS_VD4: IC202.28 (RD4), IC203.16 (DQ4), IC204.15 (5Q)
TMS_VD5: IC202.27 (RD5), IC203.17 (DQ5), IC204.14 (6Q)
TMS_VD6: IC202.26 (RD6), IC203.18 (DQ6), IC204.13 (7Q)
TMS_VD7: IC202.25 (RD7), IC203.19 (DQ7), IC204.12 (8Q)
TMS_VID_IN: IC202.35 (EXTVID)
TMS_VID_OUT: IC202.36 (COMVID), R201.2, T201.2 (B)
TMS_X1: C211.2, IC202.40 (XTAL1), Q201.1
TMS_X2: C212.2, IC202.39 (XTAL2), Q201.2
VRAM_A0: IC203.10 (A0), IC205.12 (8Q)
VRAM_A1: IC203.9 (A1), IC205.13 (7Q)
VRAM_A2: IC203.8 (A2), IC205.14 (6Q)
VRAM_A3: IC203.7 (A3), IC205.15 (5Q)
VRAM_A4: IC203.6 (A4), IC205.16 (4Q)
VRAM_A5: IC203.5 (A5), IC205.17 (3Q)
VRAM_A6: IC203.4 (A6), IC205.18 (2Q)
VRAM_A7: IC203.3 (A7), IC206.17 (3Q)
VRAM_A8: IC203.25 (A8), IC206.15 (5Q)
VRAM_A9: IC203.24 (A9), IC206.14 (6Q)
VRAM_A10: IC203.21 (A10), IC206.12 (8Q)
VRAM_A11: IC203.23 (A11), IC206.13 (7Q)
VRAM_A12: IC203.2 (A12), IC206.18 (2Q)
VRAM_A13: IC203.26 (A13), IC206.16 (4Q)
VRAM_BANK: IC203.1 (A14); also elsewhere on the board

Notes on the sheet:
SRAM address does not correspond to TMS address for PCB routing reasons

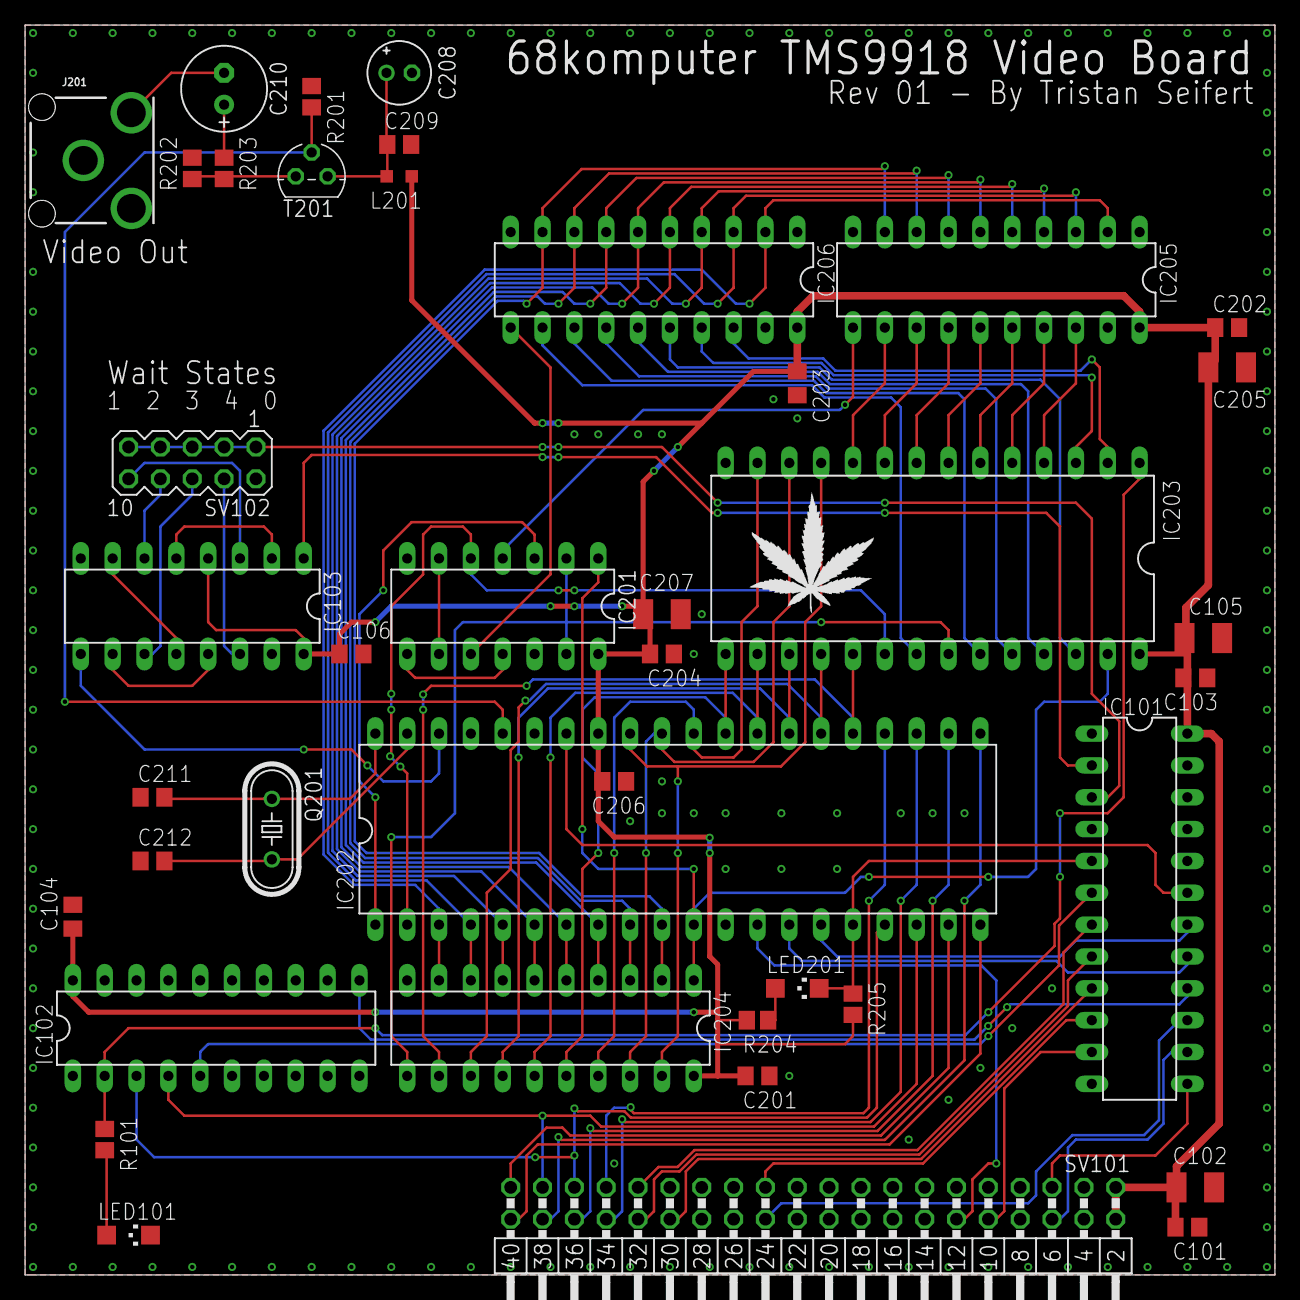
[picture p62: board tms9918.brd from above]

Board: 2 copper layers, 99.7 x 99.7 mm, 42 parts (0 on the bottom side), 83 nets.
