tristanseifert/68komputer-hw/cpu-68008/sound.brd

## EAGLE design cpu-68008/sound.brd (2019-11-14)

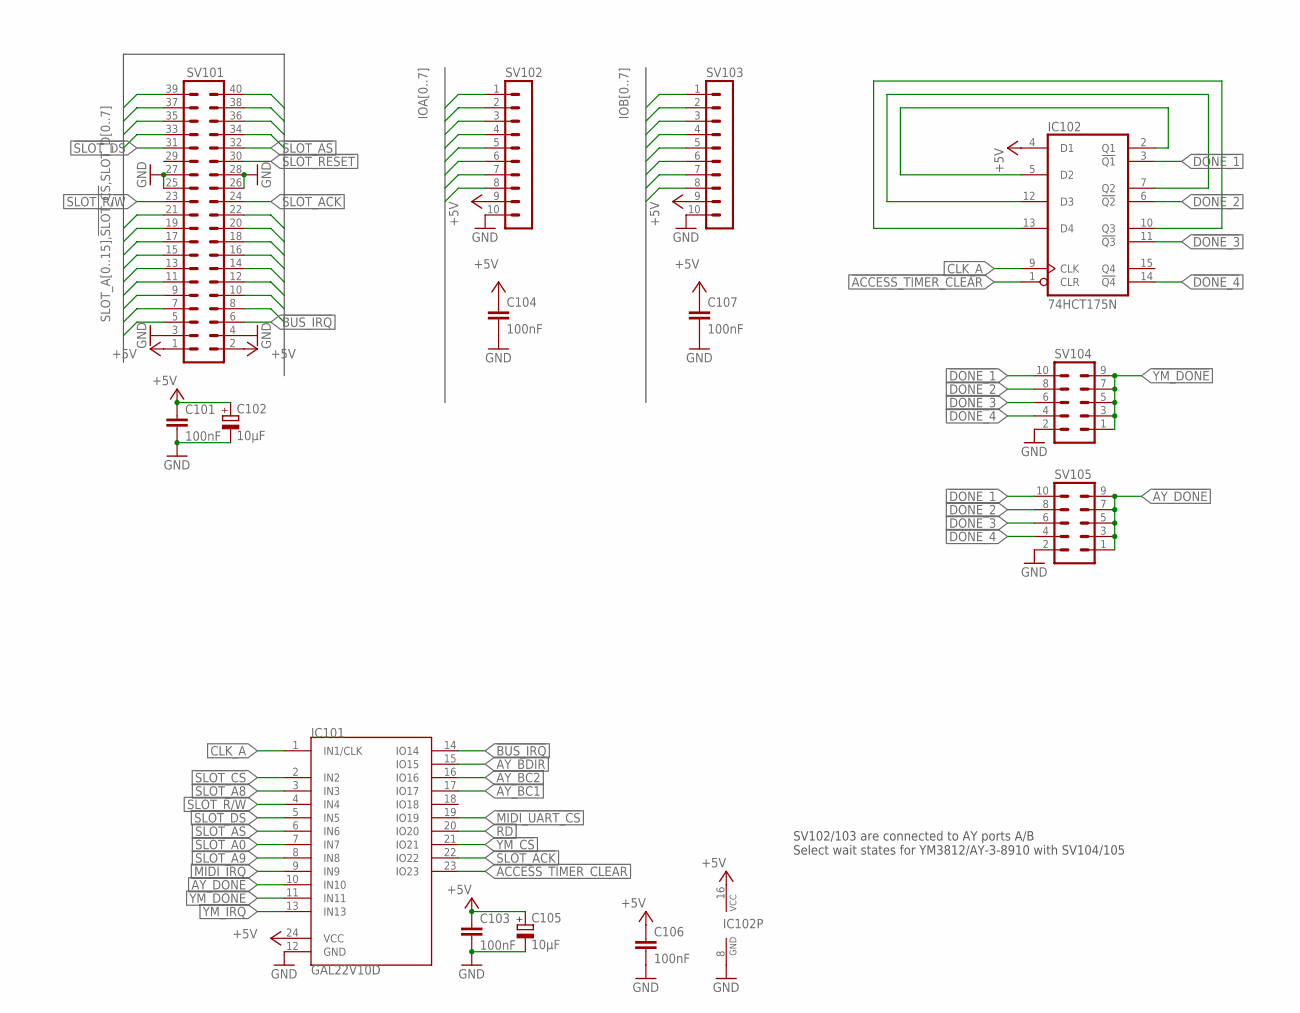
[picture p63: schematic sound.sch, sheet 1, Bus interface]

Parts:
C101, C103, C104, C106, C107: 100nF; C0805; MOUSER 710-885012207072
C102, C105: 10µF; SMC_B; MOUSER 581-TAJB106K020RNJV
IC101: GAL22V10D; DIL24S; MOUSER_SOCKET 575-11044324
IC102: 74HCT175N; DIL16; MOUSER 595-CD74HCT175E
SV101: MA20-2W
SV102, SV103: MA10-1
SV104, SV105: MA05-2

Connections:
!ACCESS_TIMER_CLEAR: IC101.23 (IO23), IC102.1 (CLR)
!AY_DONE: IC101.10 (IN10), SV105.1, SV105.3, SV105.5, SV105.7, SV105.9
!BUS_IRQ: IC101.14 (IO14), SV101.6
!DONE_1: IC102.3 (!Q1), SV104.10, SV105.10
!DONE_2: IC102.6 (!Q2), SV104.8, SV105.8
!DONE_3: IC102.11 (!Q3), SV104.6, SV105.6
!DONE_4: IC102.14 (!Q4), SV104.4, SV105.4
!MIDI_IRQ: IC101.9 (IN9); also elsewhere on the board
!MIDI_UART_CS: IC101.19 (IO19); also elsewhere on the board
!RD: IC101.20 (IO20); also elsewhere on the board
!SLOT_ACK: IC101.22 (IO22), SV101.24
!SLOT_AS: IC101.6 (IN6), SV101.32
!SLOT_CS: IC101.2 (IN2), SV101.5
!SLOT_DS: IC101.5 (IN5), SV101.31
!SLOT_RESET: SV101.30; also elsewhere on the board
!YM_CS: IC101.21 (IO21); also elsewhere on the board
!YM_DONE: IC101.11 (IN11), SV104.1, SV104.3, SV104.5, SV104.7, SV104.9
!YM_IRQ: IC101.13 (IN13); also elsewhere on the board
+5V: C101.1, C102.+, C103.1, C104.1, C105.+, C106.1, C107.1, IC101.24 (VCC), IC102.4 (D1), IC102.16 (VCC), SV101.1, SV101.2, SV102.9, SV103.9; also elsewhere on the board
AY_BC1: IC101.17 (IO17); also elsewhere on the board
AY_BC2: IC101.16 (IO16); also elsewhere on the board
AY_BDIR: IC101.15 (IO15); also elsewhere on the board
CLK_A: IC101.1 (IN1/CLK), IC102.9 (CLK); also elsewhere on the board
GND: C101.2, C102.-, C103.2, C104.2, C105.-, C106.2, C107.2, IC101.12 (GND), IC102.8 (GND), SV101.3, SV101.4, SV101.25, SV101.26, SV101.27, SV101.28, SV102.10, SV103.10, SV104.2, SV105.2; also elsewhere on the board
IOA0: SV102.1; also elsewhere on the board
IOA1: SV102.2; also elsewhere on the board
IOA2: SV102.3; also elsewhere on the board
IOA3: SV102.4; also elsewhere on the board
IOA4: SV102.5; also elsewhere on the board
IOA5: SV102.6; also elsewhere on the board
IOA6: SV102.7; also elsewhere on the board
IOA7: SV102.8; also elsewhere on the board
IOB0: SV103.1; also elsewhere on the board
IOB1: SV103.2; also elsewhere on the board
IOB2: SV103.3; also elsewhere on the board
IOB3: SV103.4; also elsewhere on the board
IOB4: SV103.5; also elsewhere on the board
IOB5: SV103.6; also elsewhere on the board
IOB6: SV103.7; also elsewhere on the board
IOB7: SV103.8; also elsewhere on the board
unnamed: IC102.10 (Q3), IC102.13 (D4)
unnamed: IC102.2 (Q1), IC102.5 (D2)
unnamed: IC102.7 (Q2), IC102.12 (D3)
SLOT_A0: IC101.7 (IN7), SV101.12; also elsewhere on the board
SLOT_A1: SV101.10; also elsewhere on the board
SLOT_A2: SV101.8; also elsewhere on the board
SLOT_A3: SV101.7
SLOT_A4: SV101.9
SLOT_A5: SV101.11
SLOT_A6: SV101.14
SLOT_A7: SV101.13
SLOT_A8: IC101.3 (IN3), SV101.16
SLOT_A9: IC101.8 (IN8), SV101.15
SLOT_A10: SV101.18
SLOT_A11: SV101.17
SLOT_A12: SV101.20
SLOT_A13: SV101.19
SLOT_A14: SV101.22
SLOT_A15: SV101.21
SLOT_D0: SV101.35; also elsewhere on the board
SLOT_D1: SV101.37; also elsewhere on the board
SLOT_D2: SV101.39; also elsewhere on the board
SLOT_D3: SV101.40; also elsewhere on the board
SLOT_D4: SV101.38; also elsewhere on the board
SLOT_D5: SV101.36; also elsewhere on the board
SLOT_D6: SV101.34; also elsewhere on the board
SLOT_D7: SV101.33; also elsewhere on the board
SLOT_R/!W!: IC101.4 (IN4), SV101.23; also elsewhere on the board

Notes on the sheet:
SV102/103 are connected to AY ports A/B Select wait states for YM3812/AY-3-8910 with SV104/105

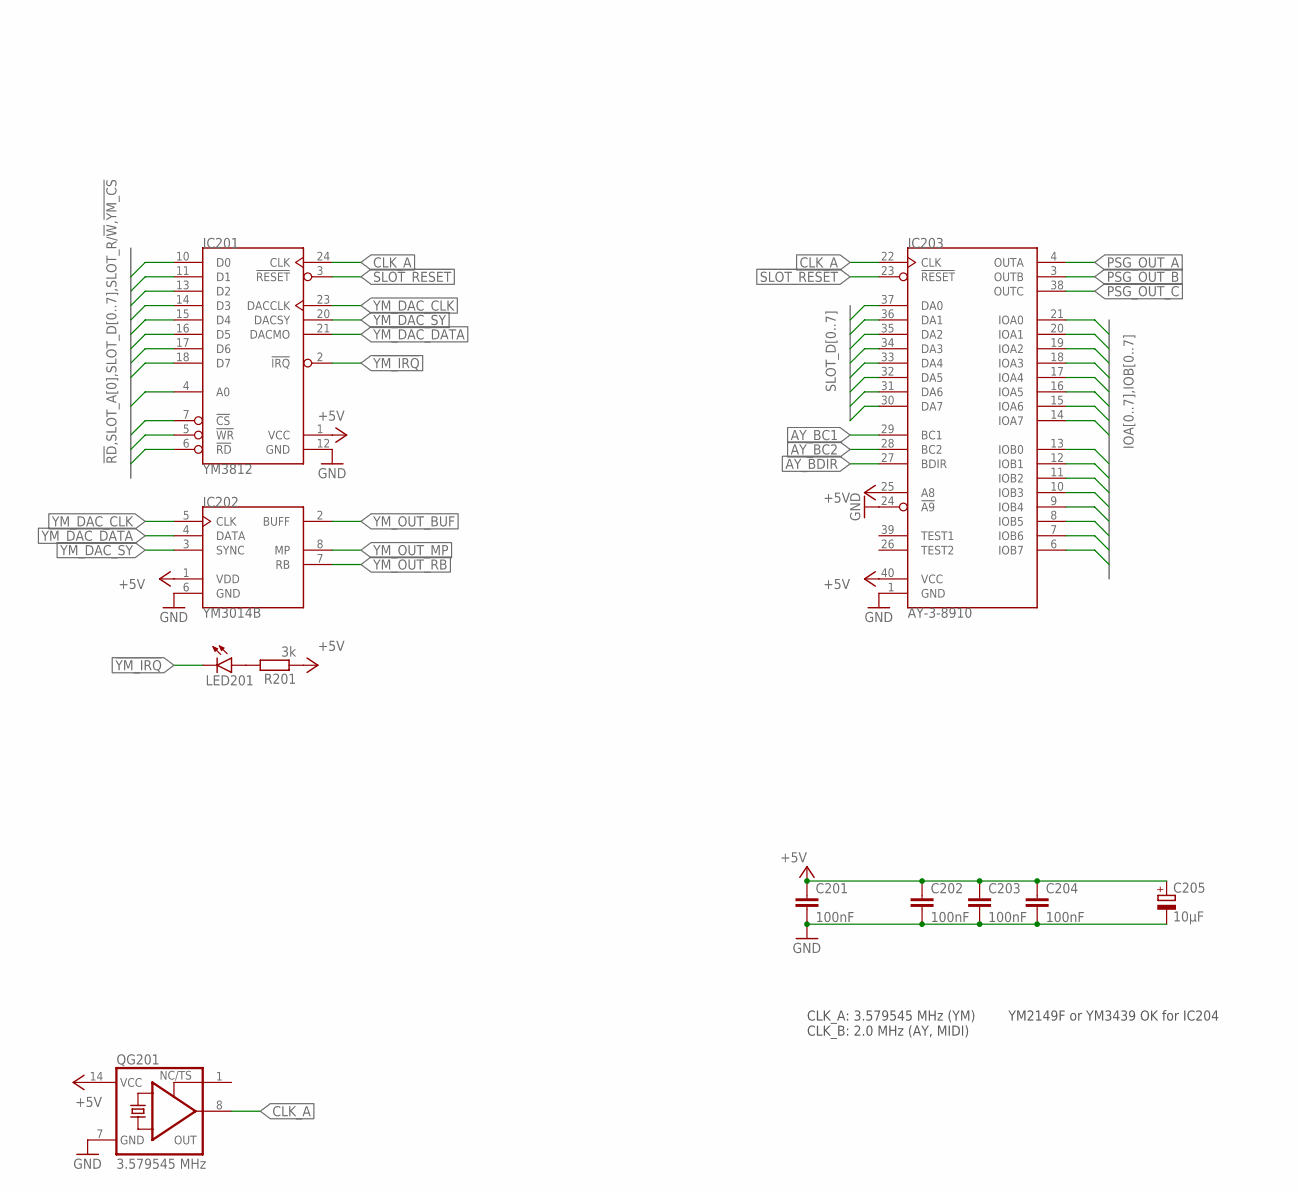
[picture p64: schematic sound.sch, sheet 2, Sound Generators]

Parts:
C201, C202, C203, C204: 100nF; C0805; MOUSER 710-885012207072
C205: 10µF; SMC_B; MOUSER 581-TAJB106K020RNJV
IC201: YM3812; DIL24; MOUSER_SOCKET 575-1104762441001000
IC202: YM3014B; DIL8; MOUSER_SOCKET 575-1104730841001000
IC203: AY-3-8910; DIL40; MOUSER_SOCKET 575-11044640
LED201: LEDCHIPLED_1206; CHIPLED_1206; MOUSER 710-156120VS75300
QG201: 3.579545 MHz; DIL14S; MOUSER 520-TCF357-X
R201: 3k; R2012; MOUSER 652-CR0805JW-302ELF

Connections:
!RD: IC201.6 (!RD); also elsewhere on the board
!SLOT_RESET: IC201.3 (!RESET), IC203.23 (!RESET); also elsewhere on the board
!YM_CS: IC201.7 (!CS); also elsewhere on the board
!YM_IRQ: IC201.2 (!IRQ), LED201.C; also elsewhere on the board
+5V: C201.1, C202.1, C203.1, C204.1, C205.+, IC201.1 (VCC), IC202.1 (VDD), IC203.25 (A8), IC203.40 (VCC), QG201.14 (VCC), R201.1; also elsewhere on the board
AY_BC1: IC203.29 (BC1); also elsewhere on the board
AY_BC2: IC203.28 (BC2); also elsewhere on the board
AY_BDIR: IC203.27 (BDIR); also elsewhere on the board
CLK_A: IC201.24 (CLK), IC203.22 (CLK), QG201.8 (OUT); also elsewhere on the board
GND: C201.2, C202.2, C203.2, C204.2, C205.-, IC201.12 (GND), IC202.6 (GND), IC203.1 (GND), IC203.24 (!A9), QG201.7 (GND); also elsewhere on the board
IOA0: IC203.21 (IOA0); also elsewhere on the board
IOA1: IC203.20 (IOA1); also elsewhere on the board
IOA2: IC203.19 (IOA2); also elsewhere on the board
IOA3: IC203.18 (IOA3); also elsewhere on the board
IOA4: IC203.17 (IOA4); also elsewhere on the board
IOA5: IC203.16 (IOA5); also elsewhere on the board
IOA6: IC203.15 (IOA6); also elsewhere on the board
IOA7: IC203.14 (IOA7); also elsewhere on the board
IOB0: IC203.13 (IOB0); also elsewhere on the board
IOB1: IC203.12 (IOB1); also elsewhere on the board
IOB2: IC203.11 (IOB2); also elsewhere on the board
IOB3: IC203.10 (IOB3); also elsewhere on the board
IOB4: IC203.9 (IOB4); also elsewhere on the board
IOB5: IC203.8 (IOB5); also elsewhere on the board
IOB6: IC203.7 (IOB6); also elsewhere on the board
IOB7: IC203.6 (IOB7); also elsewhere on the board
unnamed: LED201.A, R201.2
PSG_OUT_A: IC203.4 (OUTA); also elsewhere on the board
PSG_OUT_B: IC203.3 (OUTB); also elsewhere on the board
PSG_OUT_C: IC203.38 (OUTC); also elsewhere on the board
SLOT_A0: IC201.4 (A0); also elsewhere on the board
SLOT_D0: IC201.10 (D0), IC203.37 (DA0); also elsewhere on the board
SLOT_D1: IC201.11 (D1), IC203.36 (DA1); also elsewhere on the board
SLOT_D2: IC201.13 (D2), IC203.35 (DA2); also elsewhere on the board
SLOT_D3: IC201.14 (D3), IC203.34 (DA3); also elsewhere on the board
SLOT_D4: IC201.15 (D4), IC203.33 (DA4); also elsewhere on the board
SLOT_D5: IC201.16 (D5), IC203.32 (DA5); also elsewhere on the board
SLOT_D6: IC201.17 (D6), IC203.31 (DA6); also elsewhere on the board
SLOT_D7: IC201.18 (D7), IC203.30 (DA7); also elsewhere on the board
SLOT_R/!W!: IC201.5 (!WR); also elsewhere on the board
YM_DAC_CLK: IC201.23 (DACCLK), IC202.5 (CLK)
YM_DAC_DATA: IC201.21 (DACMO), IC202.4 (DATA)
YM_DAC_SY: IC201.20 (DACSY), IC202.3 (SYNC)
YM_OUT_BUF: IC202.2 (BUFF); also elsewhere on the board
YM_OUT_MP: IC202.8 (MP); also elsewhere on the board
YM_OUT_RB: IC202.7 (RB); also elsewhere on the board

Notes on the sheet:
CLK_A: 3.579545 MHz (YM) CLK_B: 2.0 MHz (AY, MIDI)
YM2149F or YM3439 OK for IC204

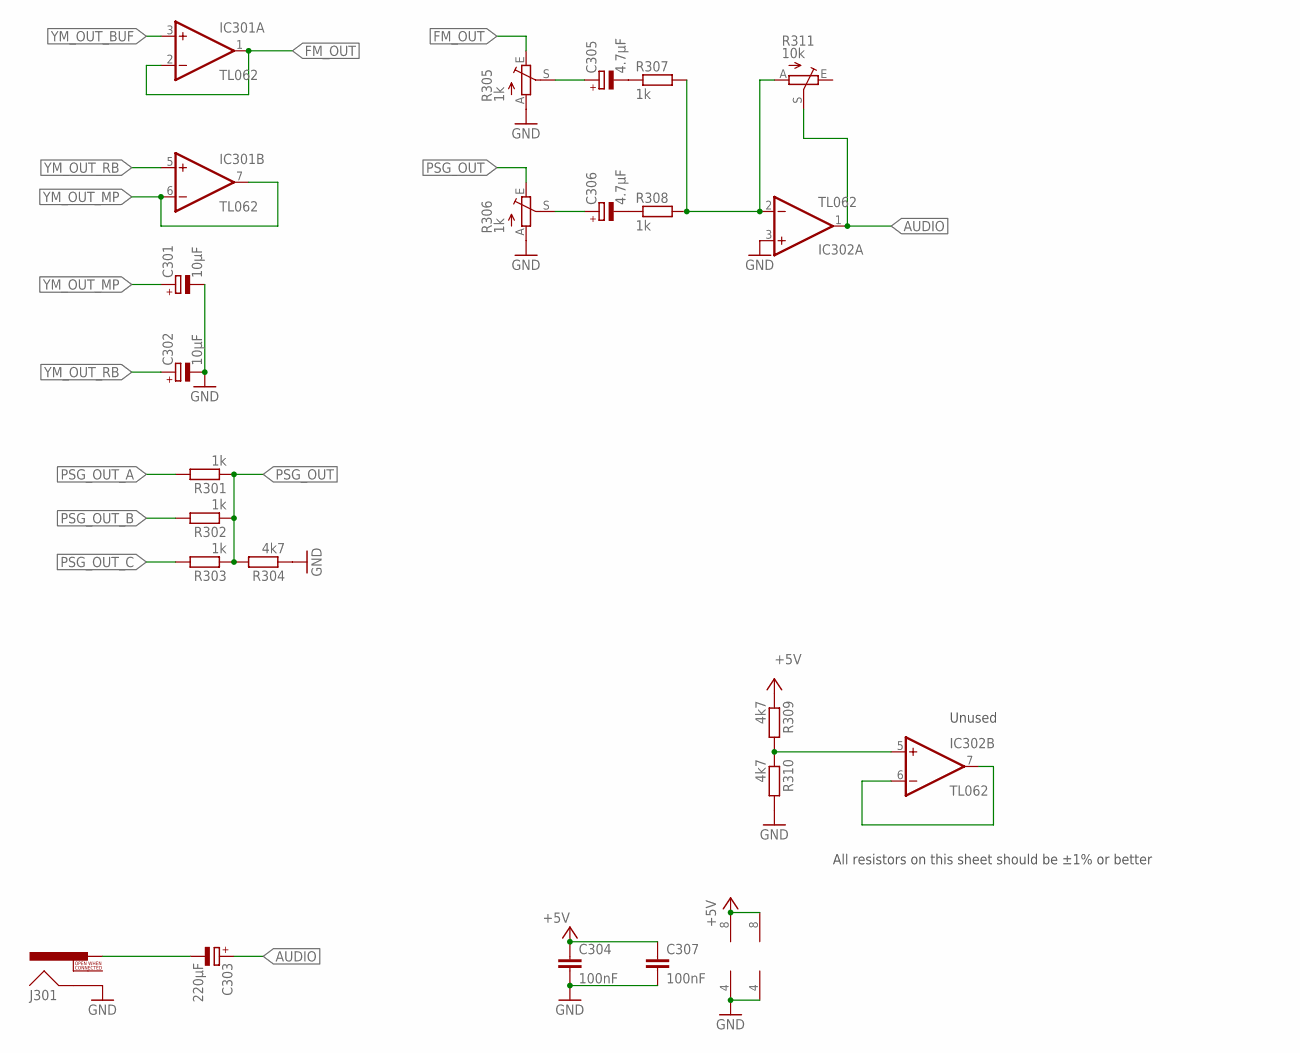
[picture p65: schematic sound.sch, sheet 3, Analog]

Parts:
C301, C302: 10µF; E2-5; MOUSER 710-860020472003
C303: 220µF; E2,5-6; MOUSER 710-860020373010
C304, C307: 100nF; C0805; MOUSER 710-885012207072
C305, C306: 4.7µF; E2-5; MOUSER 710-860020472001
IC301, IC302: TL062; DIL08; MOUSER 595-TL062CP
J301: RCALOCK; RCA_LOCK; MOUSER 502-PJRAN1X1U03AUX
R301, R302, R303, R307, R308: 1k; R2012; MOUSER 652-CR0805FX-1001ELF
R304, R309, R310: 4k7; R2012; MOUSER 652-CR0805FX-4701ELF
R305, R306: 1k; PT-10S; MOUSER PT10LH01-102A2020-S
R311: 10k; PT-10S; MOUSER 531-PT10H-10K-S

Connections:
+5V: C304.1, C307.1, IC301.8 (V+), IC302.8 (V+), R309.1; also elsewhere on the board
AUDIO: C303.+, IC302.1 (OUT), R311.S
FM_OUT: IC301.1 (OUT), IC301.2 (-IN), R305.E
GND: C301.-, C302.-, C304.2, C307.2, IC301.4 (V-), IC302.3 (+IN), IC302.4 (V-), J301.SHELL, R304.1, R305.A, R306.A, R310.2; also elsewhere on the board
unnamed: C305.+, R305.S
unnamed: C303.-, J301.PIN
unnamed: C306.+, R306.S
unnamed: C305.-, R307.1
unnamed: C306.-, R308.1
unnamed: IC302.2 (-IN), R307.2, R308.2, R311.A
unnamed: IC302.6 (-IN), IC302.7 (OUT)
unnamed: IC302.5 (+IN), R309.2, R310.1
PSG_OUT: R301.1, R302.1, R303.1, R304.2, R306.E
PSG_OUT_A: R301.2; also elsewhere on the board
PSG_OUT_B: R302.2; also elsewhere on the board
PSG_OUT_C: R303.2; also elsewhere on the board
YM_OUT_BUF: IC301.3 (+IN); also elsewhere on the board
YM_OUT_MP: C301.+, IC301.6 (-IN), IC301.7 (OUT); also elsewhere on the board
YM_OUT_RB: C302.+, IC301.5 (+IN); also elsewhere on the board

Notes on the sheet:
All resistors on this sheet should be ±1% or better
Unused

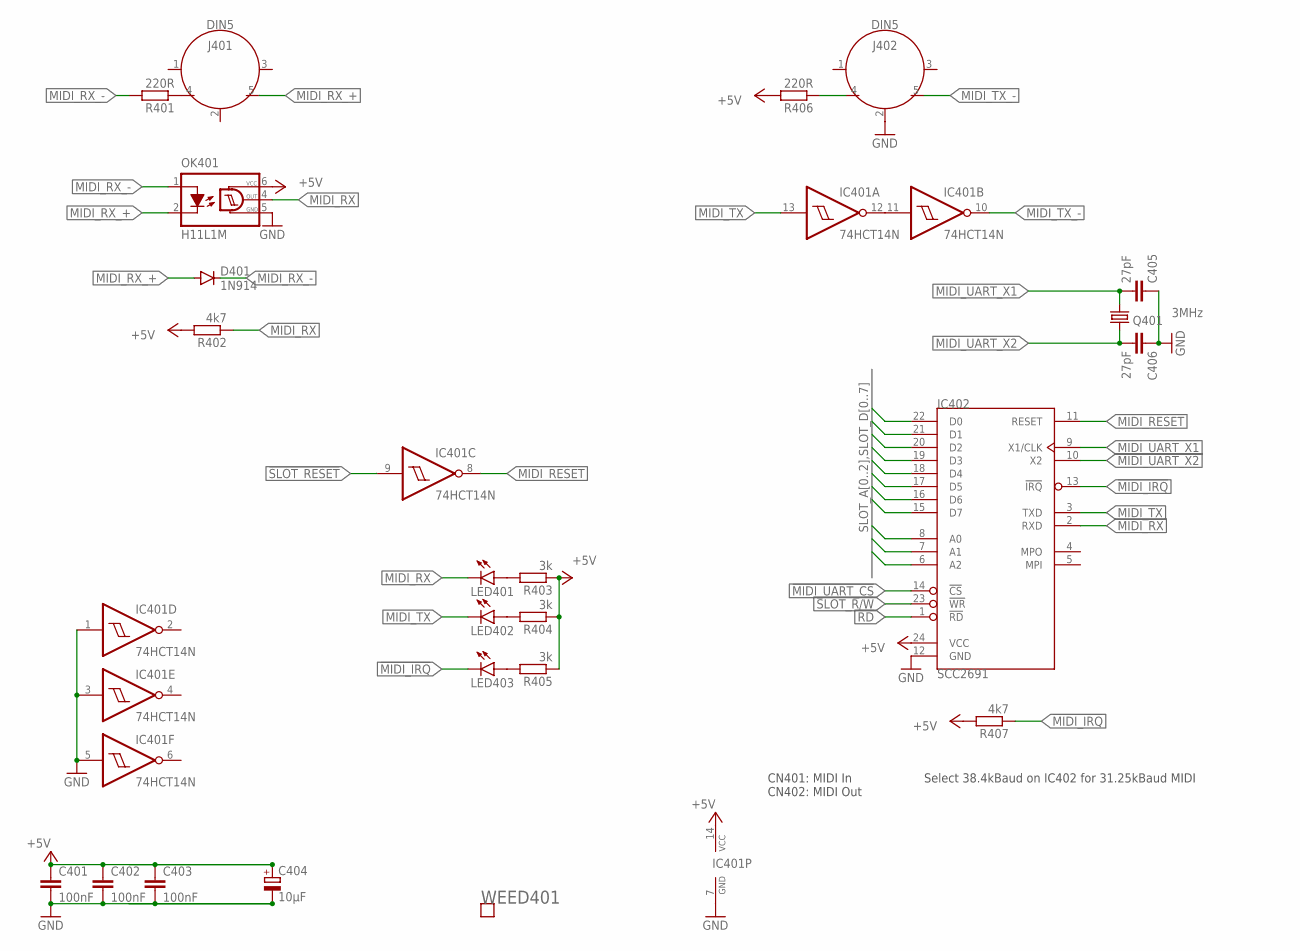
[picture p66: schematic sound.sch, sheet 4, MIDI Interface]

Parts:
C401, C402, C403: 100nF; C0805; MOUSER 710-885012207072
C404: 10µF; SMC_B; MOUSER 581-TAJB106K020RNJV
C405, C406: 27pF; C0805; MOUSER 80-C0805C270K5HACTU
D401: 1N914; DO35-10; MOUSER 512-1N914TR
IC401: 74HCT14N; DIL14; MOUSER 595-SN74HCT14N
IC402: SCC2691; DIL24S; MOUSER_SOCKET 575-11044324
J401, J402: DIN5; DIN5-RA-PTH; MOUSER 806-KCDX-5S-N
LED401, LED402, LED403: LEDCHIPLED_1206; CHIPLED_1206; MOUSER 710-156120VS75300
OK401: H11L1M; DIL06; MOUSER 512-H11L1M
Q401: 3MHz; HC49/S; MOUSER 520-HCA300-SX
R401, R406: 220R; R2012; MOUSER 652-CR0805FX-2200ELF
R402, R407: 4k7; R2012; MOUSER 652-CR0805FX-4701ELF
R403, R404, R405: 3k; R2012; MOUSER 652-CR0805JW-302ELF
WEED401: WEED; DOINK

Connections:
!MIDI_IRQ: IC402.13 (!IRQ), LED403.C, R407.1; also elsewhere on the board
!MIDI_UART_CS: IC402.14 (!CS); also elsewhere on the board
!RD: IC402.1 (!RD); also elsewhere on the board
!SLOT_RESET: IC401.9 (I); also elsewhere on the board
+5V: C401.1, C402.1, C403.1, C404.+, IC401.14 (VCC), IC402.24 (VCC), OK401.6 (VCC), R402.2, R403.1, R404.1, R405.1, R406.2, R407.2; also elsewhere on the board
GND: C401.2, C402.2, C403.2, C404.-, C405.1, C406.1, IC401.1 (I), IC401.3 (I), IC401.5 (I), IC401.7 (GND), IC402.12 (GND), J402.2, OK401.5 (GND); also elsewhere on the board
MIDI_RESET: IC401.8 (O), IC402.11 (RESET)
MIDI_RX: IC402.2 (RXD), LED401.C, OK401.4 (OUT), R402.1
MIDI_RX_+: D401.A, J401.5, OK401.2 (C)
MIDI_RX_-: D401.C, OK401.1 (A), R401.2
MIDI_TX: IC401.13 (I), IC402.3 (TXD), LED402.C
MIDI_TX_-: IC401.10 (O), J402.5
MIDI_UART_X1: C405.2, IC402.9 (X1/CLK), Q401.1
MIDI_UART_X2: C406.2, IC402.10 (X2), Q401.2
unnamed: LED401.A, R403.2
unnamed: LED402.A, R404.2
unnamed: J401.4, R401.1
unnamed: IC401.11 (I), IC401.12 (O)
unnamed: J402.4, R406.1
unnamed: LED403.A, R405.2
SLOT_A0: IC402.8 (A0); also elsewhere on the board
SLOT_A1: IC402.7 (A1); also elsewhere on the board
SLOT_A2: IC402.6 (A2); also elsewhere on the board
SLOT_D0: IC402.22 (D0); also elsewhere on the board
SLOT_D1: IC402.21 (D1); also elsewhere on the board
SLOT_D2: IC402.20 (D2); also elsewhere on the board
SLOT_D3: IC402.19 (D3); also elsewhere on the board
SLOT_D4: IC402.18 (D4); also elsewhere on the board
SLOT_D5: IC402.17 (D5); also elsewhere on the board
SLOT_D6: IC402.16 (D6); also elsewhere on the board
SLOT_D7: IC402.15 (D7); also elsewhere on the board
SLOT_R/!W!: IC402.23 (!WR); also elsewhere on the board

Notes on the sheet:
CN401: MIDI In CN402: MIDI Out
Select 38.4kBaud on IC402 for 31.25kBaud MIDI

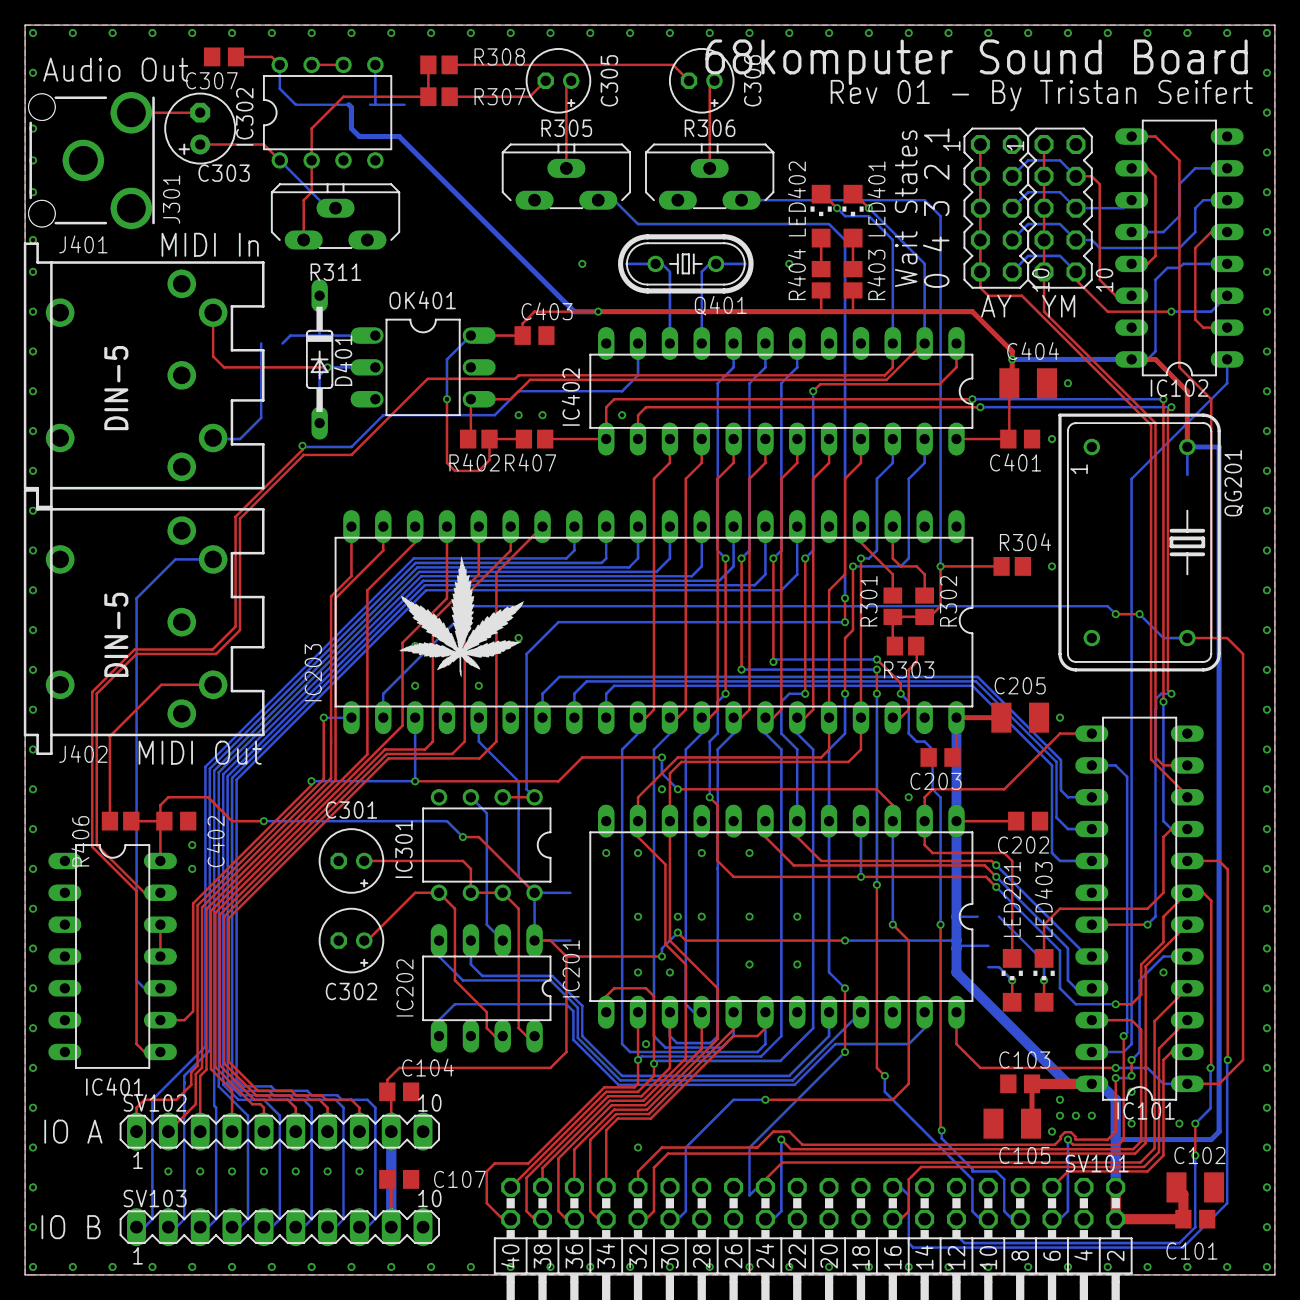
[picture p67: board cpu-68008/sound.brd from above]

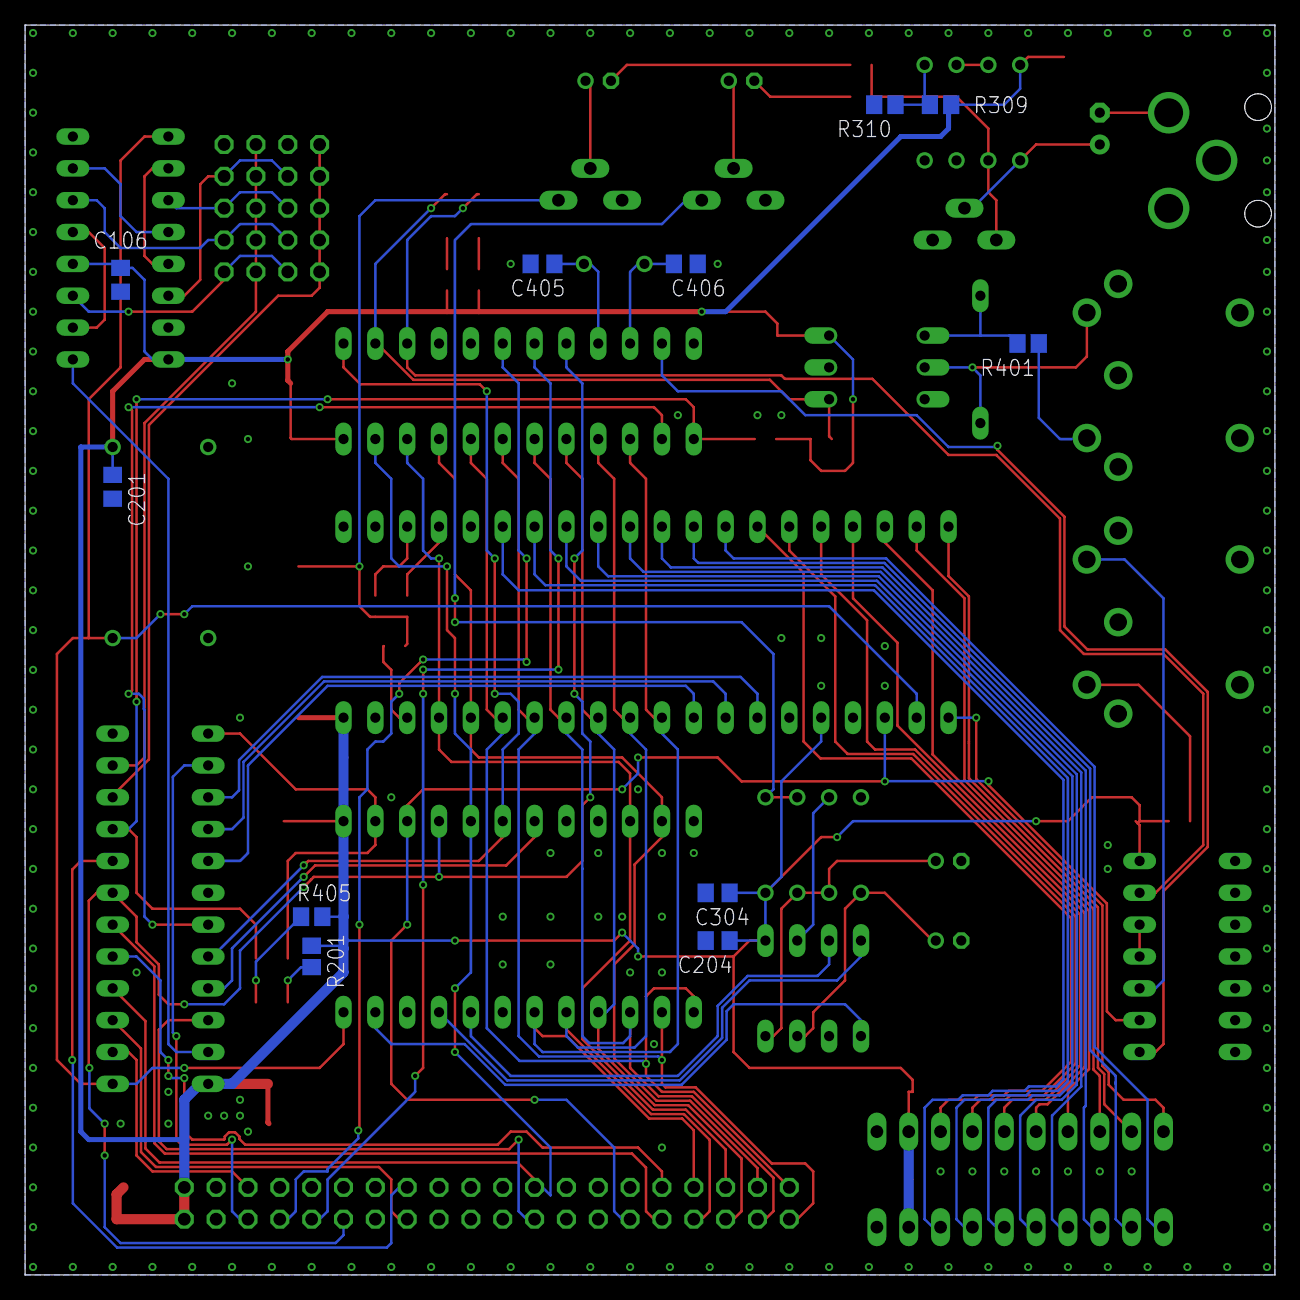
[picture p68: board cpu-68008/sound.brd from below]

Board: 2 copper layers, 99.7 x 99.7 mm, 70 parts (11 on the bottom side), 92 nets.
