tristanseifert/68komputer-hw/cpu-68008/ide-8bit.brd

## EAGLE design cpu-68008/ide-8bit.brd (2019-11-14)

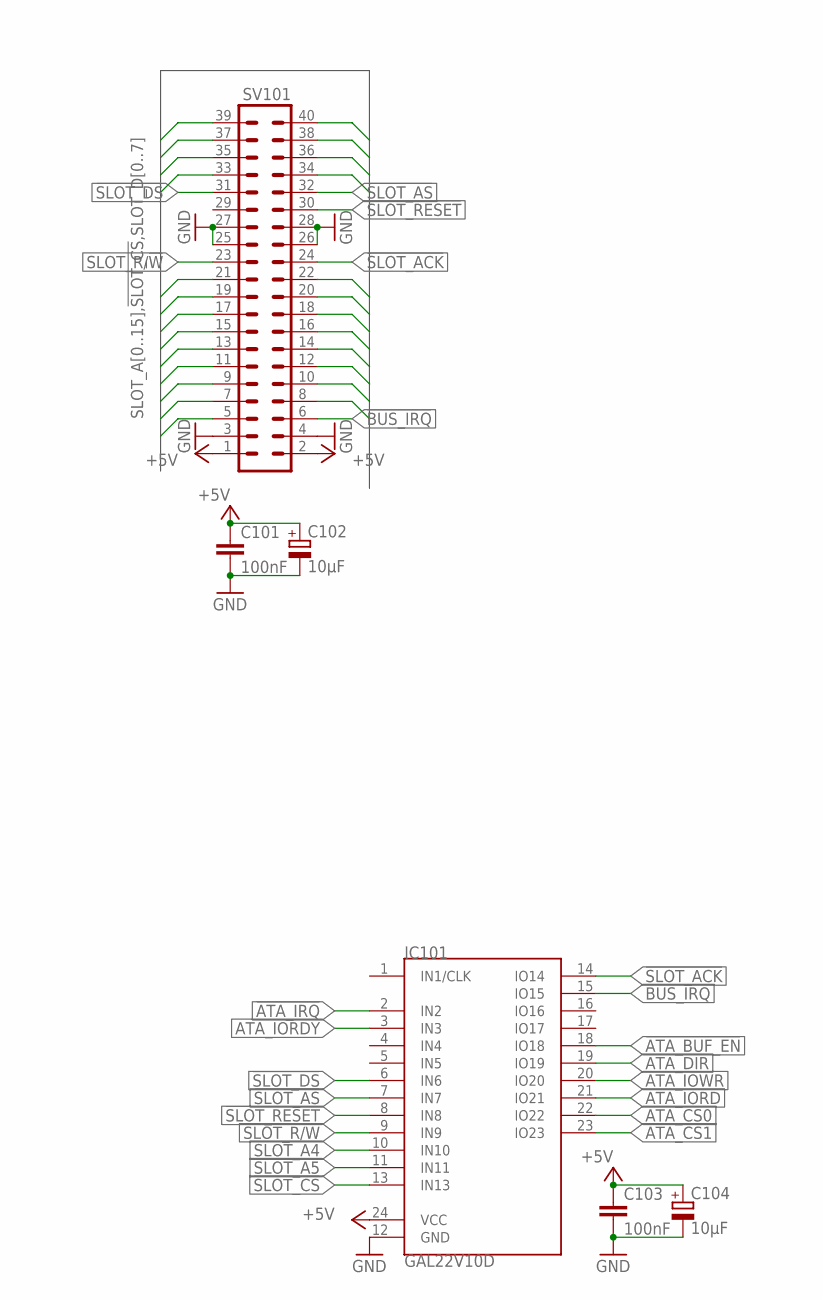
[picture p69: schematic ide-8bit.sch, sheet 1, Bus interface]

Parts:
C101, C103: 100nF; C0805; MOUSER 710-885012207072
C102, C104: 10µF; SMC_B; MOUSER 581-TAJB106K020RNJV
IC101: GAL22V10D; DIL24S; MOUSER_SOCKET 575-11044324
SV101: MA20-2W; MOUSER 517-30340-5002

Connections:
!ATA_BUF_EN: IC101.18 (IO18); also elsewhere on the board
!ATA_CS0: IC101.22 (IO22); also elsewhere on the board
!ATA_CS1: IC101.23 (IO23); also elsewhere on the board
!ATA_IRQ: IC101.2 (IN2); also elsewhere on the board
!BUS_IRQ: IC101.15 (IO15), SV101.6
!SLOT_ACK: IC101.14 (IO14), SV101.24
!SLOT_AS: IC101.7 (IN7), SV101.32
!SLOT_CS: IC101.13 (IN13), SV101.5
!SLOT_DS: IC101.6 (IN6), SV101.31
!SLOT_RESET: IC101.8 (IN8), SV101.30
+5V: C101.1, C102.+, C103.1, C104.+, IC101.24 (VCC), SV101.1, SV101.2; also elsewhere on the board
ATA_DIR: IC101.19 (IO19); also elsewhere on the board
ATA_IORD: IC101.21 (IO21); also elsewhere on the board
ATA_IORDY: IC101.3 (IN3); also elsewhere on the board
ATA_IOWR: IC101.20 (IO20); also elsewhere on the board
GND: C101.2, C102.-, C103.2, C104.-, IC101.12 (GND), SV101.3, SV101.4, SV101.25, SV101.26, SV101.27, SV101.28; also elsewhere on the board
SLOT_A0: SV101.12; also elsewhere on the board
SLOT_A1: SV101.10; also elsewhere on the board
SLOT_A2: SV101.8; also elsewhere on the board
SLOT_A3: SV101.7
SLOT_A4: IC101.10 (IN10), SV101.9
SLOT_A5: IC101.11 (IN11), SV101.11
SLOT_A6: SV101.14
SLOT_A7: SV101.13
SLOT_A8: SV101.16
SLOT_A9: SV101.15
SLOT_A10: SV101.18
SLOT_A11: SV101.17
SLOT_A12: SV101.20
SLOT_A13: SV101.19
SLOT_A14: SV101.22
SLOT_A15: SV101.21
SLOT_D0: SV101.35; also elsewhere on the board
SLOT_D1: SV101.37; also elsewhere on the board
SLOT_D2: SV101.39; also elsewhere on the board
SLOT_D3: SV101.40; also elsewhere on the board
SLOT_D4: SV101.38; also elsewhere on the board
SLOT_D5: SV101.36; also elsewhere on the board
SLOT_D6: SV101.34; also elsewhere on the board
SLOT_D7: SV101.33; also elsewhere on the board
SLOT_R/!W!: IC101.9 (IN9), SV101.23

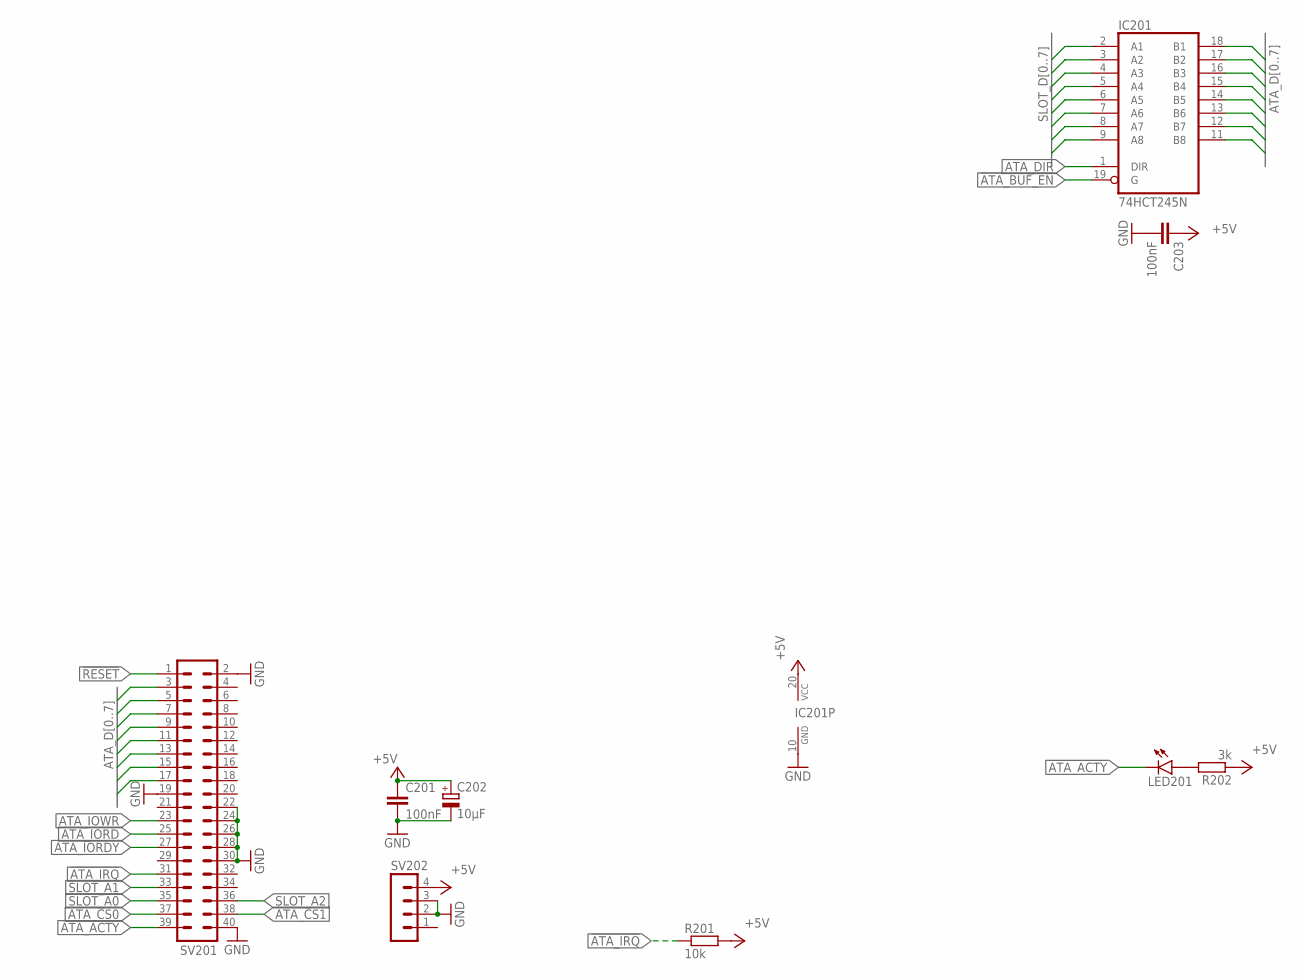
[picture p70: schematic ide-8bit.sch, sheet 2, ATA Interface]

Parts:
C201, C203: 100nF; C0805; MOUSER 710-885012207072
C202: 10µF; SMC_B; MOUSER 581-TAJB106K020RNJV
IC201: 74HCT245N; DIL20; MOUSER 595-SN74HCT245N
LED201: LEDCHIPLED_1206; CHIPLED_1206; MOUSER 710-156120VS75300
R201: 10k; R2012; MOUSER 652-CR0805FX-1002ELF
R202: 3k; R2012; MOUSER 652-CR0805JW-302ELF
SV201: ML40L
SV202: MA04-1

Connections:
!ATA_ACTY: LED201.C, SV201.39
!ATA_BUF_EN: IC201.19 (G); also elsewhere on the board
!ATA_CS0: SV201.37; also elsewhere on the board
!ATA_CS1: SV201.38; also elsewhere on the board
!ATA_IRQ: R201.1, SV201.31; also elsewhere on the board
!RESET: SV201.1
+5V: C201.1, C202.+, C203.1, IC201.20 (VCC), R201.2, R202.1, SV202.4; also elsewhere on the board
ATA_D0: IC201.18 (B1), SV201.17
ATA_D1: IC201.17 (B2), SV201.15
ATA_D2: IC201.16 (B3), SV201.13
ATA_D3: IC201.15 (B4), SV201.11
ATA_D4: IC201.14 (B5), SV201.9
ATA_D5: IC201.13 (B6), SV201.7
ATA_D6: IC201.12 (B7), SV201.5
ATA_D7: IC201.11 (B8), SV201.3
ATA_DIR: IC201.1 (DIR); also elsewhere on the board
ATA_IORD: SV201.25; also elsewhere on the board
ATA_IORDY: SV201.27; also elsewhere on the board
ATA_IOWR: SV201.23; also elsewhere on the board
GND: C201.2, C202.-, C203.2, IC201.10 (GND), SV201.2, SV201.19, SV201.22, SV201.24, SV201.26, SV201.28, SV201.30, SV201.40, SV202.2, SV202.3; also elsewhere on the board
unnamed: LED201.A, R202.2
SLOT_A0: SV201.35; also elsewhere on the board
SLOT_A1: SV201.33; also elsewhere on the board
SLOT_A2: SV201.36; also elsewhere on the board
SLOT_D0: IC201.2 (A1); also elsewhere on the board
SLOT_D1: IC201.3 (A2); also elsewhere on the board
SLOT_D2: IC201.4 (A3); also elsewhere on the board
SLOT_D3: IC201.5 (A4); also elsewhere on the board
SLOT_D4: IC201.6 (A5); also elsewhere on the board
SLOT_D5: IC201.7 (A6); also elsewhere on the board
SLOT_D6: IC201.8 (A7); also elsewhere on the board
SLOT_D7: IC201.9 (A8); also elsewhere on the board

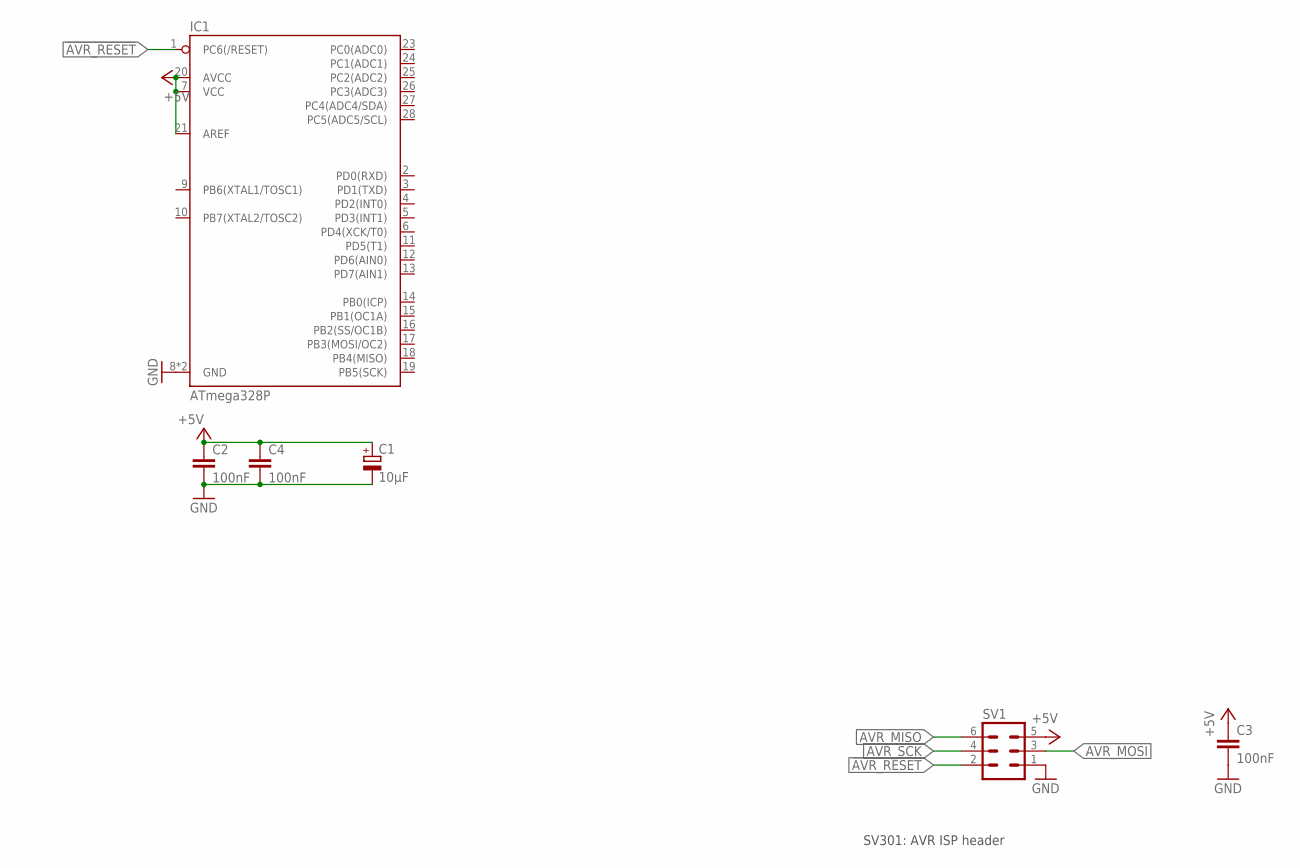
[picture p71: schematic ide-8bit.sch, sheet 3]

Parts:
C1: 10µF; SMC_B; MOUSER 581-TAJB106K020RNJV
C2, C3, C4: 100nF; C0805; MOUSER 710-885012207072
IC1: ATmega328P; DIP28; MOUSER 556-ATMEGA328-PU
SV1: ML6

Connections:
!AVR_RESET: IC1.1 (PC6(/RESET)), SV1.2
+5V: C1.+, C2.1, C3.1, C4.1, IC1.7 (VCC), IC1.20 (AVCC), IC1.21 (AREF), SV1.5; also elsewhere on the board
AVR_MISO: SV1.6
AVR_MOSI: SV1.3
AVR_SCK: SV1.4
GND: C1.-, C2.2, C3.2, C4.2, IC1.8 (GND), IC1.22 (GND), SV1.1; also elsewhere on the board

Notes on the sheet:
SV301: AVR ISP header
