tristanseifert/68komputer-hw/cpu-68008/ide-8bit.brd

## EAGLE design cpu-68008/ide-8bit.brd (continued)

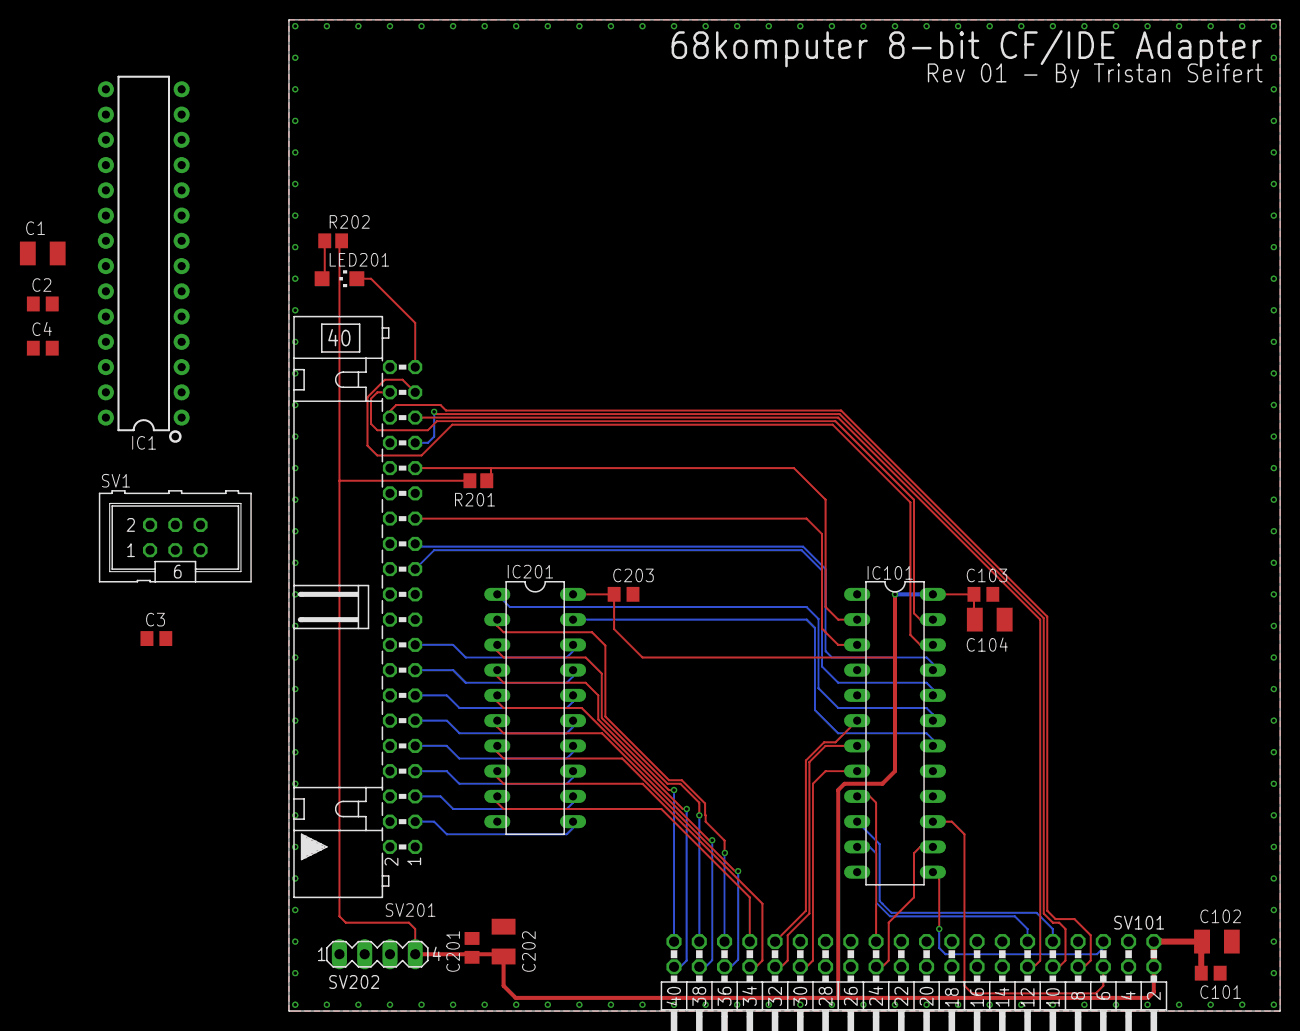
[picture p72: board ide-8bit.brd from above]

Board: 2 copper layers, 99.7 x 99.7 mm, 21 parts (0 on the bottom side), 41 nets.
