tristanseifert/68komputer-hw/cpu-68008/cpu-68008.brd

## EAGLE design cpu-68008/cpu-68008.brd (2019-10-28)

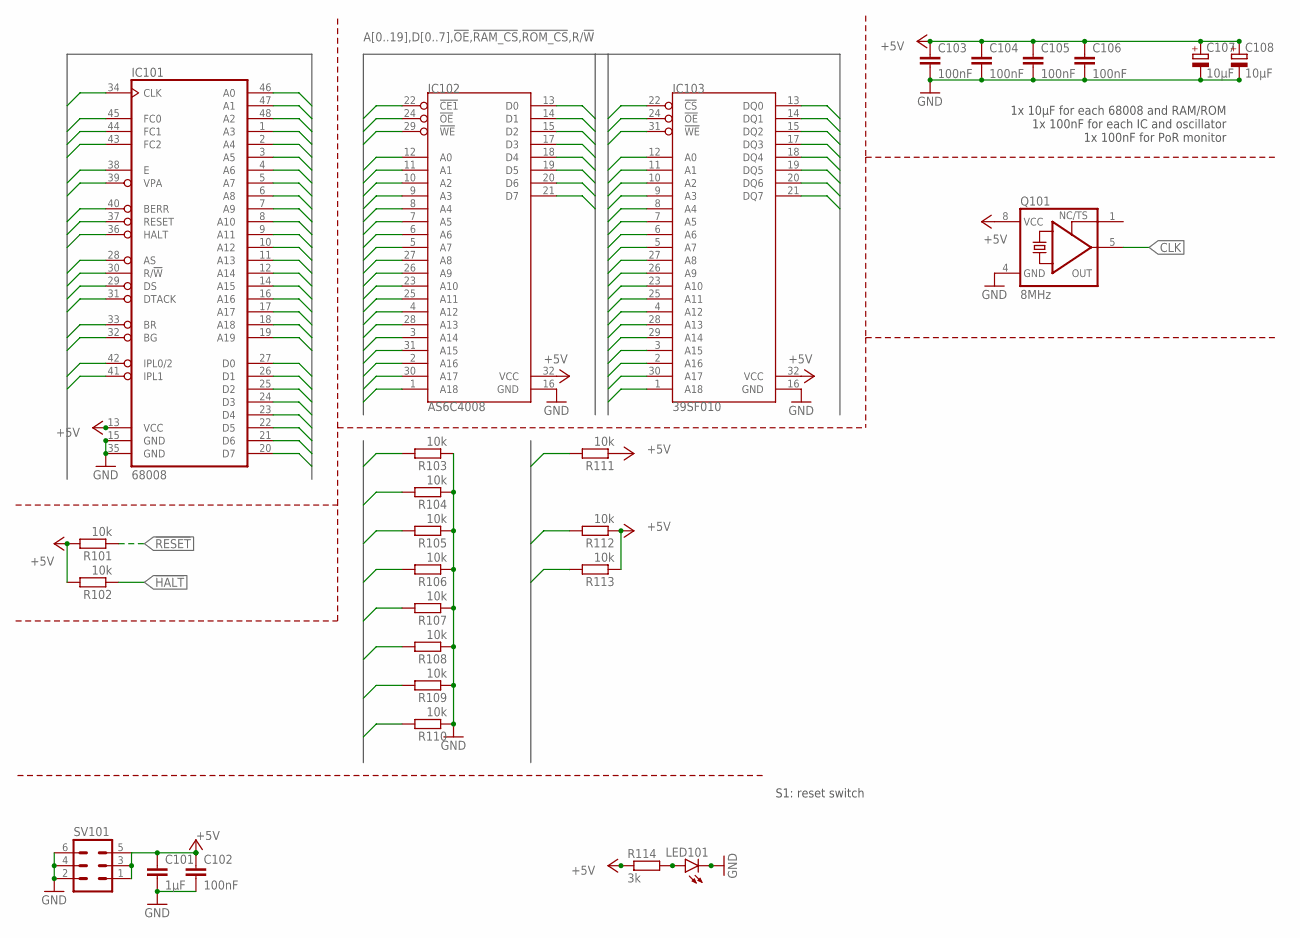
[picture p73: schematic cpu-68008.sch, sheet 1, CPU, RAM, ROM]

Parts:
C101: 1µF; C0805; MOUSER 710-885012107015
C102, C103, C104, C105, C106: 100nF; C0805; MOUSER 710-885012207072
C107, C108: 10µF; SMC_B; MOUSER 581-TAJB106K020RNJV
IC101: 68008; DIL48; MOUSER_SOCKET 517-4848-6004-CP
IC102: AS6C4008; DIL32; MOUSER_SOCKET 517-4832-6000-CP
IC103: 39SF010; DIL32; MOUSER 804-39SF010A7CPHE
LED101: LEDCHIPLED_1206; CHIPLED_1206; MOUSER 710-156120YS75300
Q101: 8MHz; DIL08S; MOUSER 774-MXO45HS-3C-8.0
R101, R102, R103, R104, R105, R106, R107, R108, R109, R110, R111, R112, R113: 10k; R2012; MOUSER 652-CR0805FX-1002ELF
R114: 3k; R2012; MOUSER 652-CR0805JW-302ELF
SV101: MA03-2

Connections:
!AS: IC101.28 (AS); also elsewhere on the board
!BERR: IC101.40 (BERR), R113.2; also elsewhere on the board
!BG: IC101.32 (BG); also elsewhere on the board
!BR: IC101.33 (BR), R111.2; also elsewhere on the board
!DS: IC101.29 (DS); also elsewhere on the board
!DTACK: IC101.31 (DTACK); also elsewhere on the board
!HALT: IC101.36 (HALT), R102.1; also elsewhere on the board
!IPL0/2: IC101.42 (IPL0/2); also elsewhere on the board
!IPL1: IC101.41 (IPL1); also elsewhere on the board
!OE: IC102.24 (!OE), IC103.24 (!OE); also elsewhere on the board
!RAM_CS: IC102.22 (!CE1); also elsewhere on the board
!RESET: IC101.37 (RESET), R101.1; also elsewhere on the board
!ROM_CS: IC103.22 (!CS); also elsewhere on the board
!VPA: IC101.39 (VPA), R112.2; also elsewhere on the board
+5V: C101.1, C102.1, C103.1, C104.1, C105.1, C106.1, C107.+, C108.+, IC101.13 (VCC), IC102.32 (VCC), IC103.32 (VCC), Q101.8 (VCC), R101.2, R102.2, R111.1, R112.1, R113.1, R114.1, SV101.1, SV101.3, SV101.5; also elsewhere on the board
A0: IC101.46 (A0), IC102.12 (A0), IC103.12 (A0); also elsewhere on the board
A1: IC101.47 (A1), IC102.11 (A1), IC103.11 (A1); also elsewhere on the board
A2: IC101.48 (A2), IC102.10 (A2), IC103.10 (A2); also elsewhere on the board
A3: IC101.1 (A3), IC102.9 (A3), IC103.9 (A3); also elsewhere on the board
A4: IC101.2 (A4), IC102.8 (A4), IC103.8 (A4); also elsewhere on the board
A5: IC101.3 (A5), IC102.7 (A5), IC103.7 (A5); also elsewhere on the board
A6: IC101.4 (A6), IC102.6 (A6), IC103.6 (A6); also elsewhere on the board
A7: IC101.5 (A7), IC102.5 (A7), IC103.5 (A7); also elsewhere on the board
A8: IC101.6 (A8), IC102.27 (A8), IC103.27 (A8); also elsewhere on the board
A9: IC101.7 (A9), IC102.26 (A9), IC103.26 (A9); also elsewhere on the board
A10: IC101.8 (A10), IC102.23 (A10), IC103.23 (A10); also elsewhere on the board
A11: IC101.9 (A11), IC102.25 (A11), IC103.25 (A11); also elsewhere on the board
A12: IC101.10 (A12), IC102.4 (A12), IC103.4 (A12); also elsewhere on the board
A13: IC101.11 (A13), IC102.28 (A13), IC103.28 (A13); also elsewhere on the board
A14: IC101.12 (A14), IC102.3 (A14), IC103.29 (A14); also elsewhere on the board
A15: IC101.14 (A15), IC102.31 (A15), IC103.3 (A15); also elsewhere on the board
A16: IC101.16 (A16), IC102.2 (A16), IC103.2 (A16); also elsewhere on the board
A17: IC101.17 (A17), IC102.30 (A17), IC103.30 (A17); also elsewhere on the board
A18: IC101.18 (A18), IC102.1 (A18), IC103.1 (A18); also elsewhere on the board
A19: IC101.19 (A19); also elsewhere on the board
CLK: IC101.34 (CLK), Q101.5 (OUT); also elsewhere on the board
D0: IC101.27 (D0), IC102.13 (D0), IC103.13 (DQ0), R103.2; also elsewhere on the board
D1: IC101.26 (D1), IC102.14 (D1), IC103.14 (DQ1), R104.2; also elsewhere on the board
D2: IC101.25 (D2), IC102.15 (D2), IC103.15 (DQ2), R105.2; also elsewhere on the board
D3: IC101.24 (D3), IC102.17 (D3), IC103.17 (DQ3), R106.2; also elsewhere on the board
D4: IC101.23 (D4), IC102.18 (D4), IC103.18 (DQ4), R107.2; also elsewhere on the board
D5: IC101.22 (D5), IC102.19 (D5), IC103.19 (DQ5), R108.2; also elsewhere on the board
D6: IC101.21 (D6), IC102.20 (D6), IC103.20 (DQ6), R109.2; also elsewhere on the board
D7: IC101.20 (D7), IC102.21 (D7), IC103.21 (DQ7), R110.2; also elsewhere on the board
E: IC101.38 (E); also elsewhere on the board
FC0: IC101.45 (FC0); also elsewhere on the board
FC1: IC101.44 (FC1); also elsewhere on the board
FC2: IC101.43 (FC2); also elsewhere on the board
GND: C101.2, C102.2, C103.2, C104.2, C105.2, C106.2, C107.-, C108.-, IC101.15 (GND), IC101.35 (GND), IC102.16 (GND), IC103.16 (GND), LED101.C, Q101.4 (GND), R103.1, R104.1, R105.1, R106.1, R107.1, R108.1, R109.1, R110.1, SV101.2, SV101.4, SV101.6; also elsewhere on the board
unnamed: LED101.A, R114.2
R/!W!: IC101.30 (R/!W), IC102.29 (!WE), IC103.31 (!WE); also elsewhere on the board

Notes on the sheet:
1x 10µF for each 68008 and RAM/ROM 1x 100nF for each IC and oscillator 1x 100nF for PoR monitor
S1: reset switch

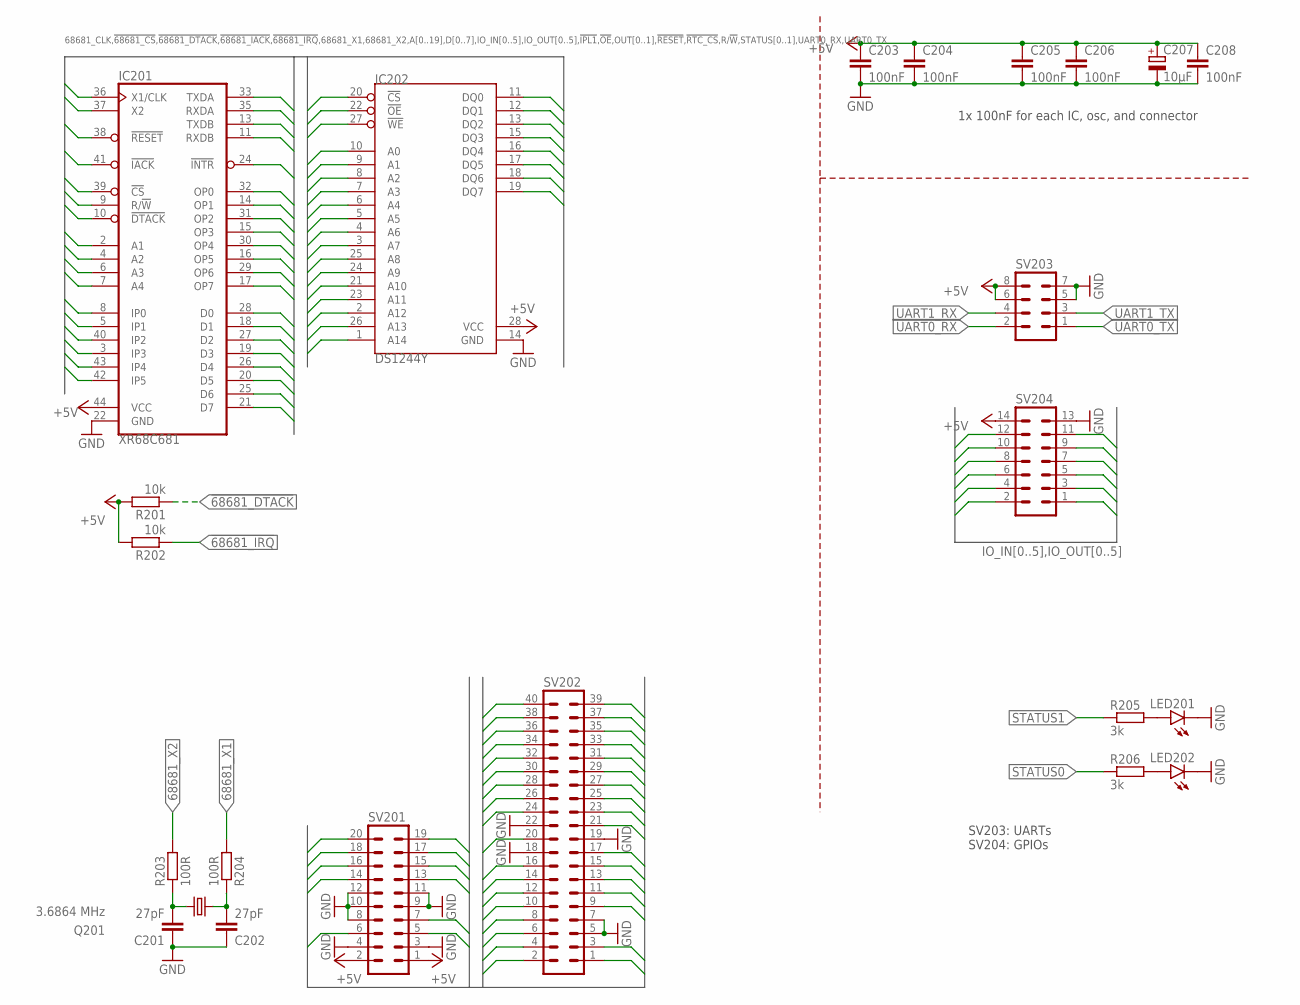
[picture p74: schematic cpu-68008.sch, sheet 2, UART, RTC, GPIO, External Bus]

Parts:
C201, C202: 27pF; C0805; MOUSER 80-C0805C270K5HACTU
C203, C204, C205, C206, C208: 100nF; C0805; MOUSER 710-885012207072
C207: 10µF; SMC_B; MOUSER 581-TAJB106K020RNJV
IC201: XR68C681; PLCC-S44; MOUSER 701-XR68C681CJ-F
IC202: DS1244Y; DIL28-6; MOUSER_SOCKET 571-1-2199299-2
LED201, LED202: LEDCHIPLED_1206; CHIPLED_1206; MOUSER 710-156120VS75300
Q201: 3.6864 MHz; HC49/S; MOUSER 815-ABL-3.6864-B2
R201, R202: 10k; R2012; MOUSER 652-CR0805FX-1002ELF
R203, R204: 100R; R2012; MOUSER 652-CR0805FX-1000ELF
R205, R206: 3k; R2012; MOUSER 652-CR0805JW-302ELF
SV201: MA10-2W
SV202: MA20-2W
SV203: MA04-2
SV204: MA07-2

Connections:
68681_X1: IC201.36 (X1/CLK), R204.2
68681_X2: IC201.37 (X2), R203.2
!68681_CS: IC201.39 (!CS); also elsewhere on the board
!68681_DTACK: IC201.10 (!DTACK), R201.1; also elsewhere on the board
!68681_IACK: IC201.41 (!IACK); also elsewhere on the board
!68681_IRQ: IC201.24 (!INTR), R202.1; also elsewhere on the board
!AS: SV202.33; also elsewhere on the board
!BERR: SV202.9; also elsewhere on the board
!BG: SV202.25; also elsewhere on the board
!BR: SV202.23; also elsewhere on the board
!BUS_CS: SV201.7; also elsewhere on the board
!BUS_DTACK: SV201.6; also elsewhere on the board
!BUS_IRQ: SV201.5; also elsewhere on the board
!DS: SV202.31; also elsewhere on the board
!DTACK: SV202.27; also elsewhere on the board
!HALT: SV202.17; also elsewhere on the board
!OE: IC202.22 (!OE); also elsewhere on the board
!RESET: IC201.38 (!RESET), SV202.15; also elsewhere on the board
!RTC_CS: IC202.20 (!CS); also elsewhere on the board
!VPA: SV202.11; also elsewhere on the board
+5V: C203.1, C204.1, C205.1, C206.1, C207.+, C208.1, IC201.44 (VCC), IC202.28 (VCC), R201.2, R202.2, SV201.1, SV201.2, SV203.6, SV203.8, SV204.14; also elsewhere on the board
A0: IC201.2 (A1), IC202.10 (A0), SV201.17; also elsewhere on the board
A1: IC201.4 (A2), IC202.9 (A1), SV201.15; also elsewhere on the board
A2: IC201.6 (A3), IC202.8 (A2), SV201.13; also elsewhere on the board
A3: IC201.7 (A4), IC202.7 (A3), SV201.14; also elsewhere on the board
A4: IC202.6 (A4), SV201.16; also elsewhere on the board
A5: IC202.5 (A5), SV201.18; also elsewhere on the board
A6: IC202.4 (A6), SV201.20; also elsewhere on the board
A7: IC202.3 (A7), SV202.2; also elsewhere on the board
A8: IC202.25 (A8), SV202.4; also elsewhere on the board
A9: IC202.24 (A9), SV202.6; also elsewhere on the board
A10: IC202.21 (A10), SV202.8; also elsewhere on the board
A11: IC202.23 (A11), SV202.10; also elsewhere on the board
A12: IC202.2 (A12), SV202.12; also elsewhere on the board
A13: IC202.26 (A13), SV202.14; also elsewhere on the board
A14: IC202.1 (A14), SV202.16; also elsewhere on the board
A15: SV202.20; also elsewhere on the board
A16: SV202.24; also elsewhere on the board
A17: SV202.26; also elsewhere on the board
A18: SV202.28; also elsewhere on the board
A19: SV202.30; also elsewhere on the board
CLK: SV202.21; also elsewhere on the board
D0: IC201.28 (D0), IC202.11 (DQ0), SV202.35; also elsewhere on the board
D1: IC201.18 (D1), IC202.12 (DQ1), SV202.37; also elsewhere on the board
D2: IC201.27 (D2), IC202.13 (DQ2), SV202.39; also elsewhere on the board
D3: IC201.19 (D3), IC202.15 (DQ3), SV202.40; also elsewhere on the board
D4: IC201.26 (D4), IC202.16 (DQ4), SV202.38; also elsewhere on the board
D5: IC201.20 (D5), IC202.17 (DQ5), SV202.36; also elsewhere on the board
D6: IC201.25 (D6), IC202.18 (DQ6), SV202.34; also elsewhere on the board
D7: IC201.21 (D7), IC202.19 (DQ7), SV202.32; also elsewhere on the board
E: SV202.13; also elsewhere on the board
FC0: SV201.19; also elsewhere on the board
FC1: SV202.1; also elsewhere on the board
FC2: SV202.3; also elsewhere on the board
GND: C201.1, C202.1, C203.2, C204.2, C205.2, C206.2, C207.-, C208.2, IC201.22 (GND), IC202.14 (GND), LED201.C, LED202.C, SV201.3, SV201.4, SV201.8, SV201.9, SV201.10, SV201.11, SV201.12, SV202.5, SV202.7, SV202.18, SV202.19, SV202.22, SV203.5, SV203.7, SV204.13; also elsewhere on the board
IO_IN0: IC201.40 (IP2), SV204.12
IO_IN1: IC201.42 (IP5), SV204.10
IO_IN2: IC201.43 (IP4), SV204.8
IO_IN3: IC201.3 (IP3), SV204.6
IO_IN4: IC201.5 (IP1), SV204.4
IO_IN5: IC201.8 (IP0), SV204.2
IO_OUT0: IC201.31 (OP2), SV204.11
IO_OUT1: IC201.32 (OP0), SV204.9
IO_OUT2: IC201.29 (OP6), SV204.7
IO_OUT3: IC201.30 (OP4), SV204.5
IO_OUT4: IC201.14 (OP1), SV204.3
IO_OUT5: IC201.16 (OP5), SV204.1
unnamed: C202.2, Q201.1, R204.1
unnamed: C201.2, Q201.2, R203.1
unnamed: LED201.A, R205.2
unnamed: LED202.A, R206.2
R/!W!: IC201.9 (R/!W), IC202.27 (!WE), SV202.29; also elsewhere on the board
STATUS0: IC201.15 (OP3), R206.1
STATUS1: IC201.17 (OP7), R205.1
UART0_RX: IC201.35 (RXDA), SV203.2
UART0_TX: IC201.33 (TXDA), SV203.1
UART1_RX: IC201.11 (RXDB), SV203.4
UART1_TX: IC201.13 (TXDB), SV203.3

Notes on the sheet:
1x 100nF for each IC, osc, and connector
SV203: UARTs SV204: GPIOs

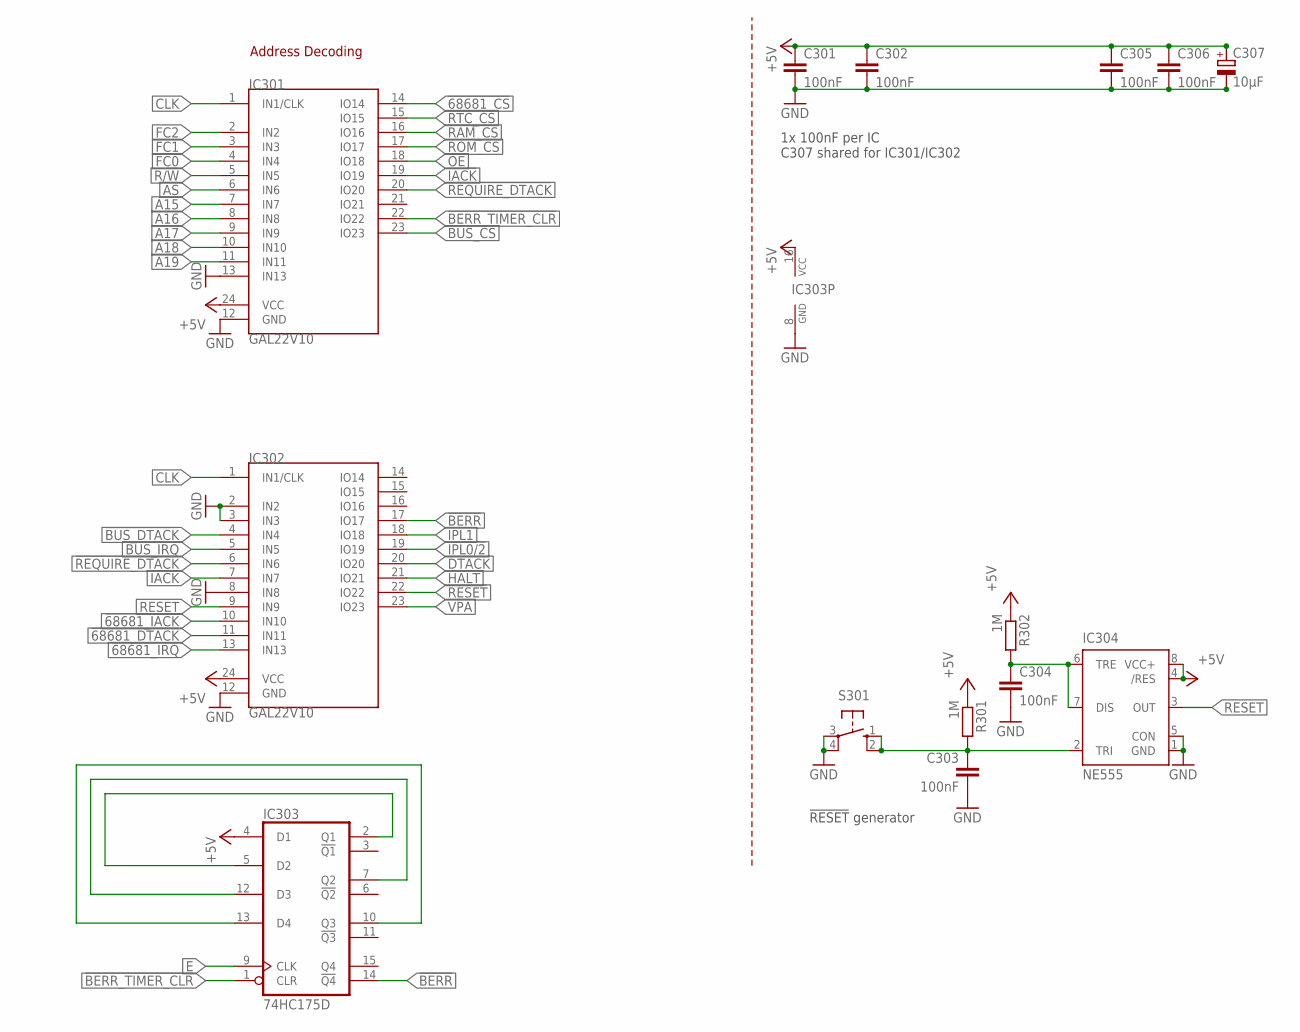
[picture p75: schematic cpu-68008.sch, sheet 3, the main logic blaz]

Parts:
C301, C302, C303, C305, C306: 100nF; C0805; MOUSER 710-885012207072
C304: 100nF; C0805; MOUSER 710-885012207078
C307: 10µF; SMC_B; MOUSER 581-TAJB106K020RNJV
IC301, IC302: GAL22V10; DIL24S
IC303: 74HC175D; SO16; MOUSER 595-CD74HCT175M
IC304: NE555; DIL-08; MOUSER 595-NE555P
R301, R302: 1M; R2012; MOUSER 652-CR0805FX-1004ELF
S301: 10-XX; B3F-10XX; MOUSER 653-B3F-1052

Connections:
!68681_CS: IC301.14 (IO14); also elsewhere on the board
!68681_DTACK: IC302.11 (IN11); also elsewhere on the board
!68681_IACK: IC302.10 (IN10); also elsewhere on the board
!68681_IRQ: IC302.13 (IN13); also elsewhere on the board
!AS: IC301.6 (IN6); also elsewhere on the board
!BERR: IC302.17 (IO17), IC303.14 (!Q4); also elsewhere on the board
!BERR_TIMER_CLR: IC301.22 (IO22), IC303.1 (CLR)
!BUS_CS: IC301.23 (IO23); also elsewhere on the board
!BUS_DTACK: IC302.4 (IN4); also elsewhere on the board
!BUS_IRQ: IC302.5 (IN5); also elsewhere on the board
!DTACK: IC302.20 (IO20); also elsewhere on the board
!HALT: IC302.21 (IO21); also elsewhere on the board
!IACK: IC301.19 (IO19), IC302.7 (IN7)
!IPL0/2: IC302.19 (IO19); also elsewhere on the board
!IPL1: IC302.18 (IO18); also elsewhere on the board
!OE: IC301.18 (IO18); also elsewhere on the board
!RAM_CS: IC301.16 (IO16); also elsewhere on the board
!REQUIRE_DTACK: IC301.20 (IO20), IC302.6 (IN6)
!RESET: IC302.22 (IO22); also elsewhere on the board
!ROM_CS: IC301.17 (IO17); also elsewhere on the board
!RTC_CS: IC301.15 (IO15); also elsewhere on the board
!VPA: IC302.23 (IO23); also elsewhere on the board
+5V: C301.1, C302.1, C305.1, C306.1, C307.+, IC301.24 (VCC), IC302.24 (VCC), IC303.4 (D1), IC303.16 (VCC), IC304.4 (/RES), IC304.8 (VCC+), R301.1, R302.1; also elsewhere on the board
A15: IC301.7 (IN7); also elsewhere on the board
A16: IC301.8 (IN8); also elsewhere on the board
A17: IC301.9 (IN9); also elsewhere on the board
A18: IC301.10 (IN10); also elsewhere on the board
A19: IC301.11 (IN11); also elsewhere on the board
CLK: IC301.1 (IN1/CLK), IC302.1 (IN1/CLK); also elsewhere on the board
E: IC303.9 (CLK); also elsewhere on the board
FC0: IC301.4 (IN4); also elsewhere on the board
FC1: IC301.3 (IN3); also elsewhere on the board
FC2: IC301.2 (IN2); also elsewhere on the board
GND: C301.2, C302.2, C303.2, C304.2, C305.2, C306.2, C307.-, IC301.12 (GND), IC301.13 (IN13), IC302.2 (IN2), IC302.3 (IN3), IC302.8 (IN8), IC302.12 (GND), IC303.8 (GND), IC304.1 (GND), IC304.5 (CON), S301.3, S301.4 (P1); also elsewhere on the board
unnamed: C303.1, IC304.2 (TRI), R301.2, S301.1 (S), S301.2 (S1)
unnamed: IC303.2 (Q1), IC303.5 (D2)
unnamed: IC303.7 (Q2), IC303.12 (D3)
unnamed: IC303.10 (Q3), IC303.13 (D4)
unnamed: C304.1, IC304.6 (TRE), IC304.7 (DIS), R302.2
R/!W!: IC301.5 (IN5); also elsewhere on the board
RESET: IC302.9 (IN9), IC304.3 (OUT)

Notes on the sheet:
!RESET! generator
1x 100nF per IC C307 shared for IC301/IC302
Address Decoding

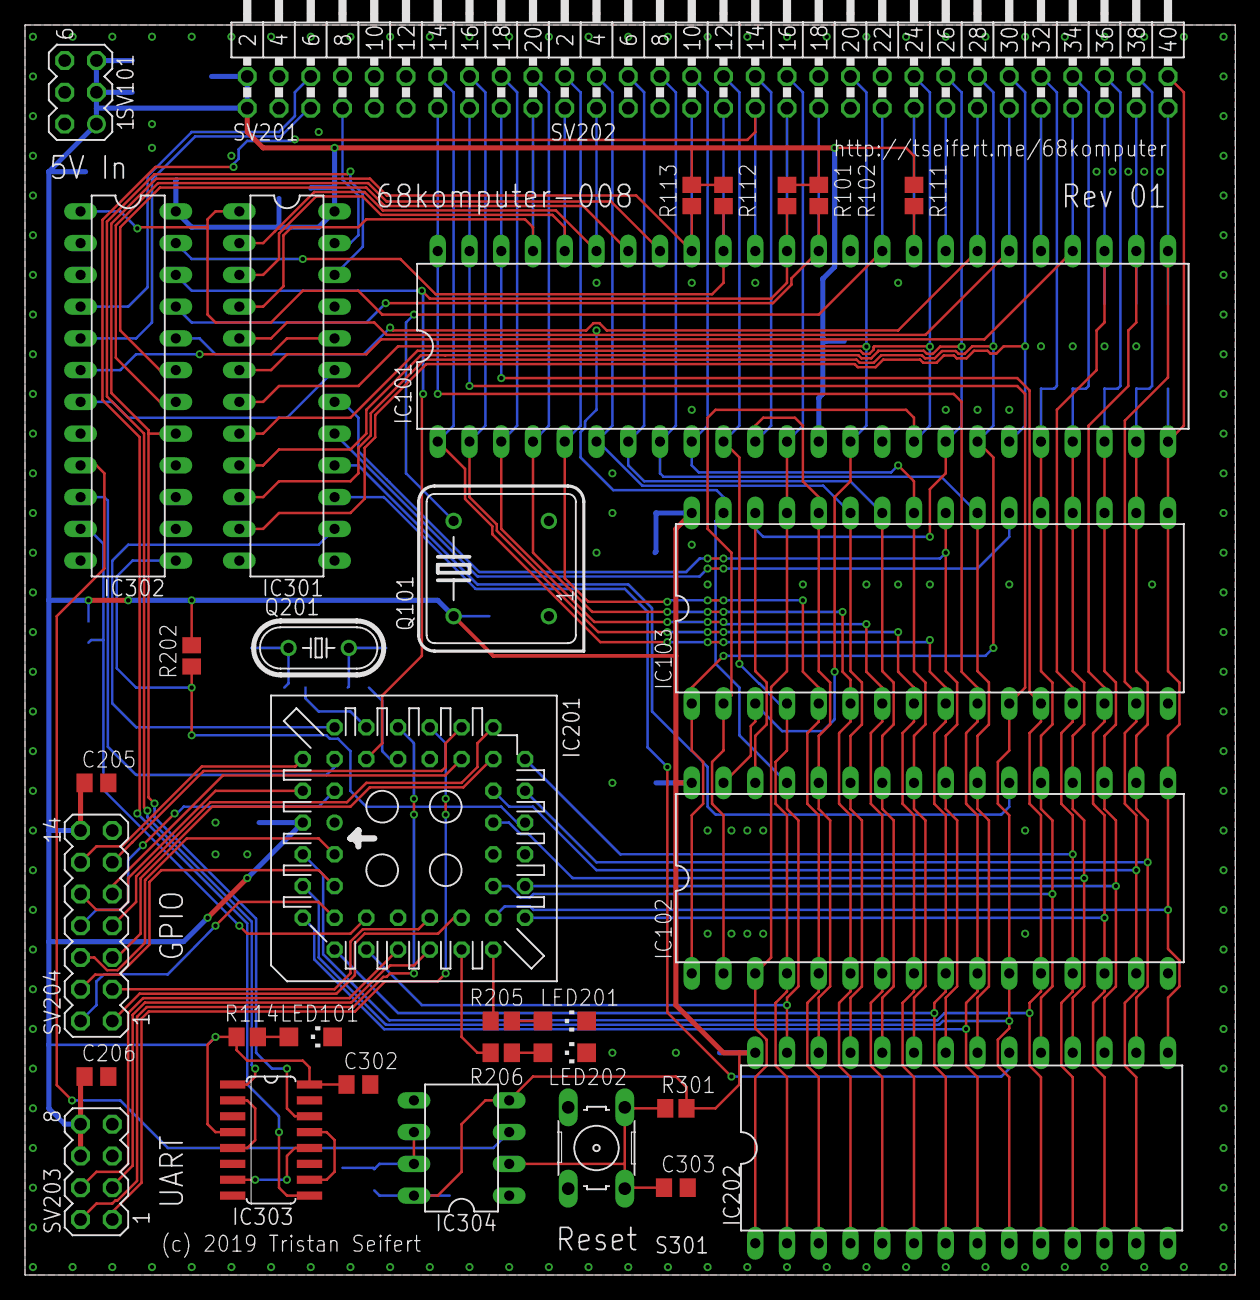
[picture p76: board cpu-68008.brd from above]

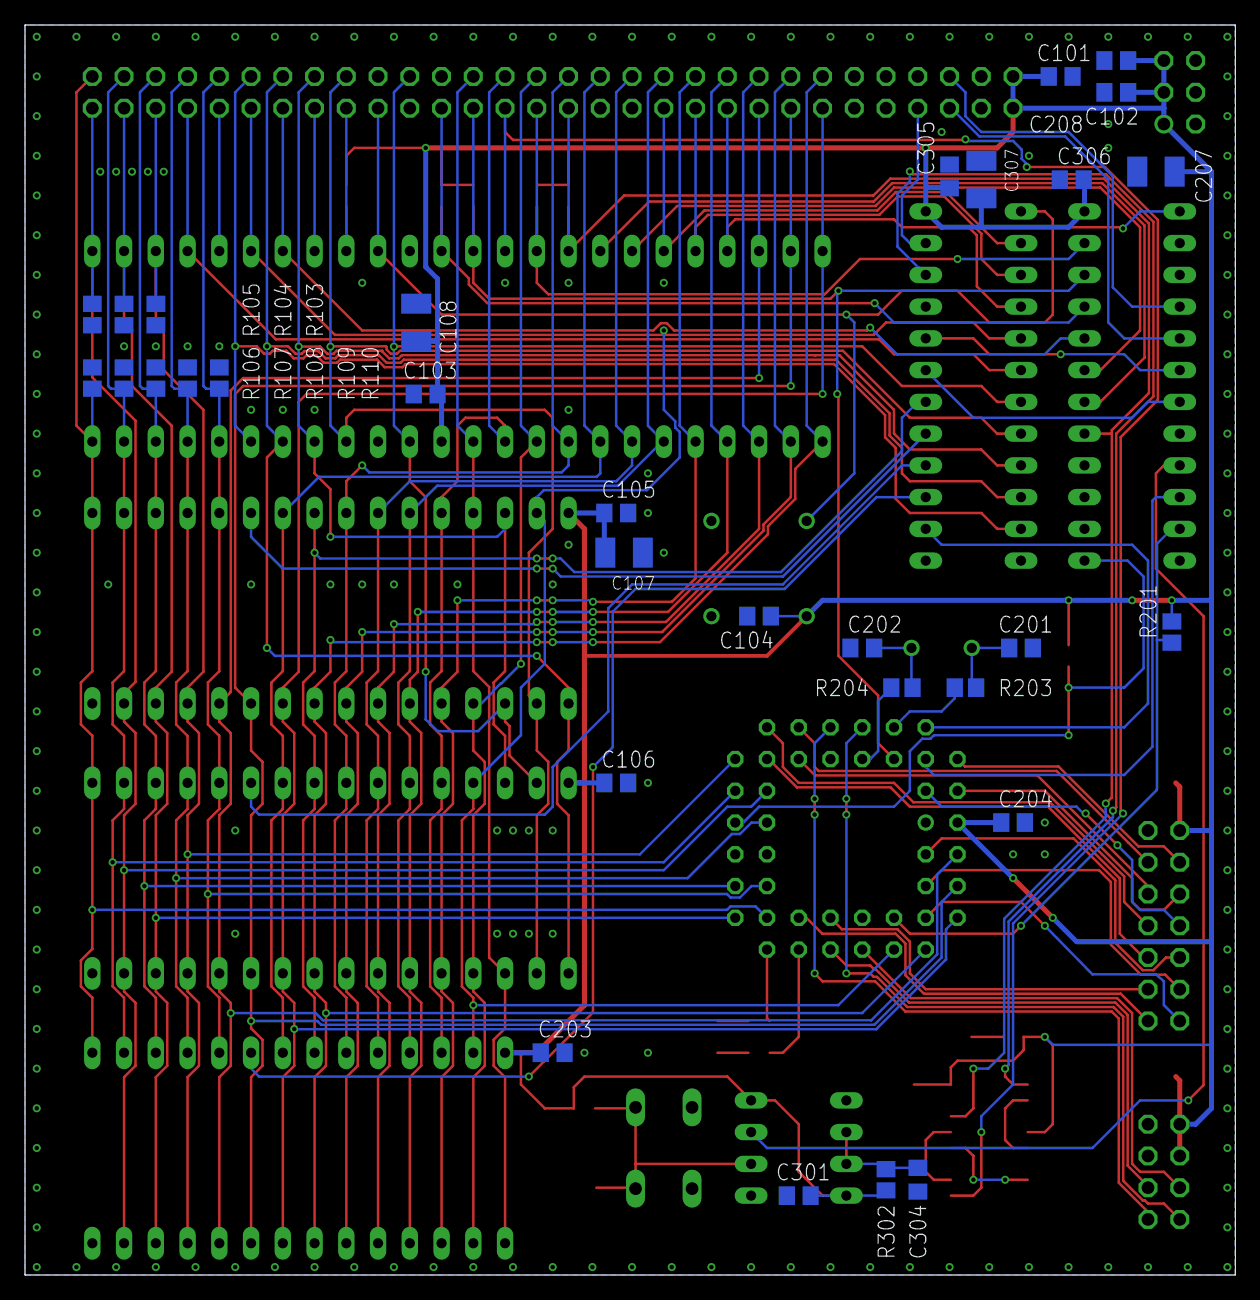
[picture p77: board cpu-68008.brd from below]

Board: 2 copper layers, 96.8 x 100.0 mm, 65 parts (31 on the bottom side), 92 nets.
