tristanseifert/68komputer-hw/cpu-68008/uart_rs232_adapter.brd

## EAGLE design cpu-68008/uart_rs232_adapter.brd (2019-10-13)

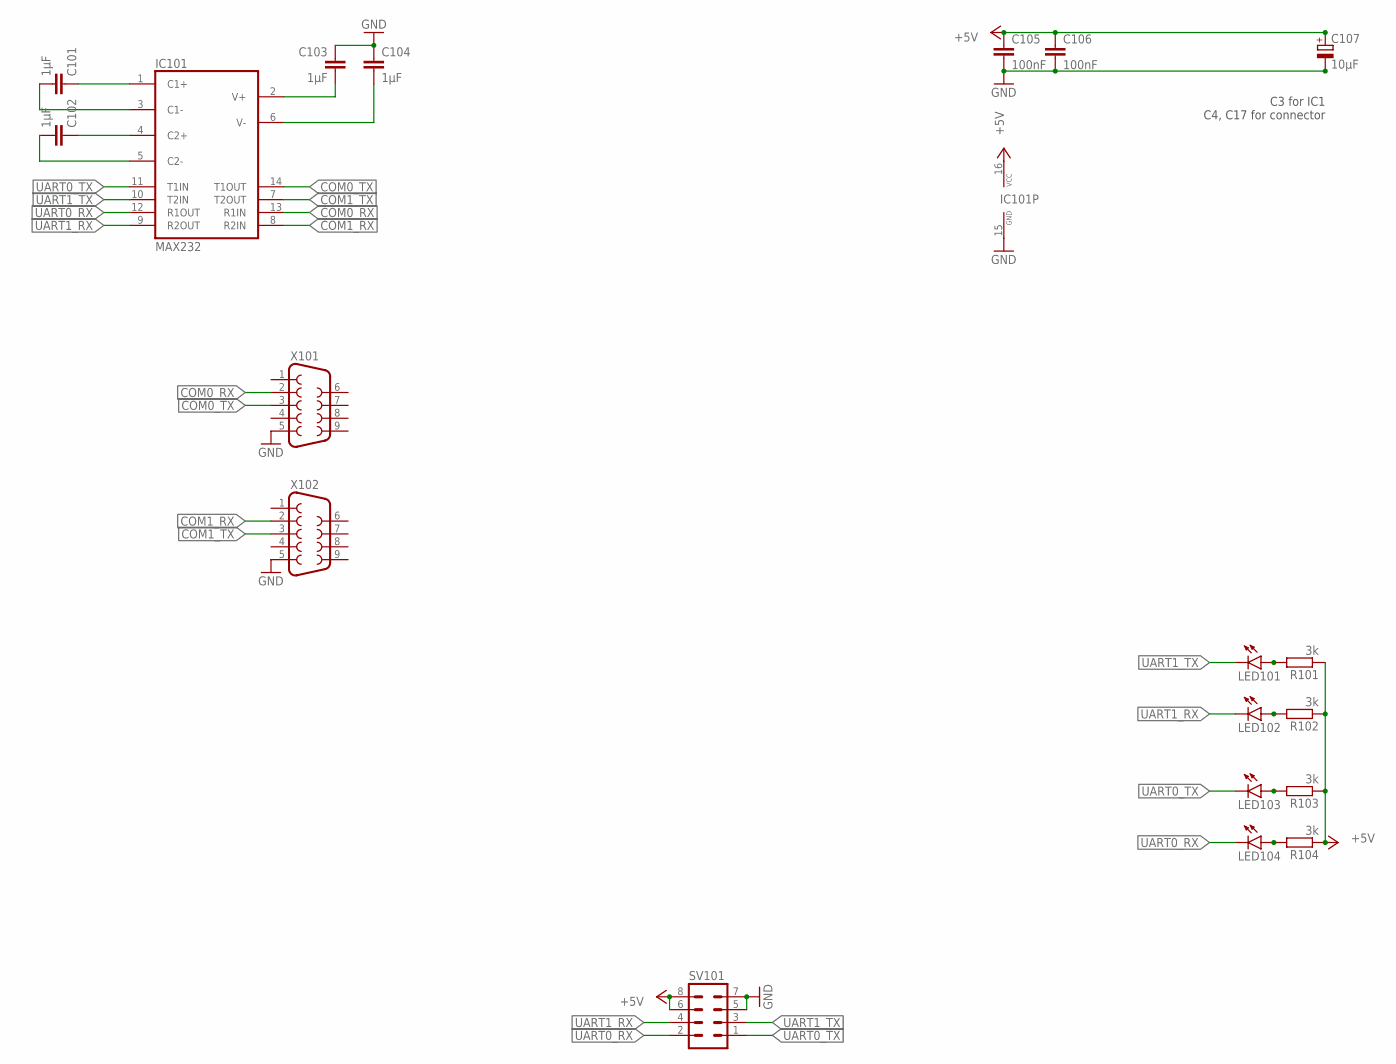
[picture p78: schematic uart_rs232_adapter.sch]

Parts:
C101, C102, C103, C104: 1µF; C0805; MOUSER 710-885012207078
C105, C106: 100nF; C0805; MOUSER 710-885012207072
C107: 10µF; SMC_B; MOUSER 581-TAJB106K020RNJV
IC101: MAX232; DIL16; MOUSER 595-MAX232ECN
LED101, LED102, LED103, LED104: LEDCHIPLED_1206; CHIPLED_1206; MOUSER 710-156120YS75300
R101, R102, R103, R104: 3k; R2012; MOUSER 652-CR0805JW-302ELF
SV101: MA04-2
X101, X102: F09HP

Connections:
+5V: C105.1, C106.1, C107.+, IC101.16 (VCC), R101.1, R102.1, R103.1, R104.1, SV101.6, SV101.8
COM0_RX: IC101.13 (R1IN), X101.2
COM0_TX: IC101.14 (T1OUT), X101.3
COM1_RX: IC101.8 (R2IN), X102.2
COM1_TX: IC101.7 (T2OUT), X102.3
GND: C103.1, C104.1, C105.2, C106.2, C107.-, IC101.15 (GND), SV101.5, SV101.7, X101.5, X102.5
unnamed: LED104.A, R104.2
unnamed: LED103.A, R103.2
unnamed: LED102.A, R102.2
unnamed: LED101.A, R101.2
unnamed: C103.2, IC101.2 (V+)
unnamed: C104.2, IC101.6 (V-)
unnamed: C102.1, IC101.4 (C2+)
unnamed: C101.1, IC101.1 (C1+)
unnamed: C101.2, IC101.3 (C1-)
unnamed: C102.2, IC101.5 (C2-)
UART0_RX: IC101.12 (R1OUT), LED104.C, SV101.2
UART0_TX: IC101.11 (T1IN), LED103.C, SV101.1
UART1_RX: IC101.9 (R2OUT), LED102.C, SV101.4
UART1_TX: IC101.10 (T2IN), LED101.C, SV101.3

Notes on the sheet:
C3 for IC1 C4, C17 for connector

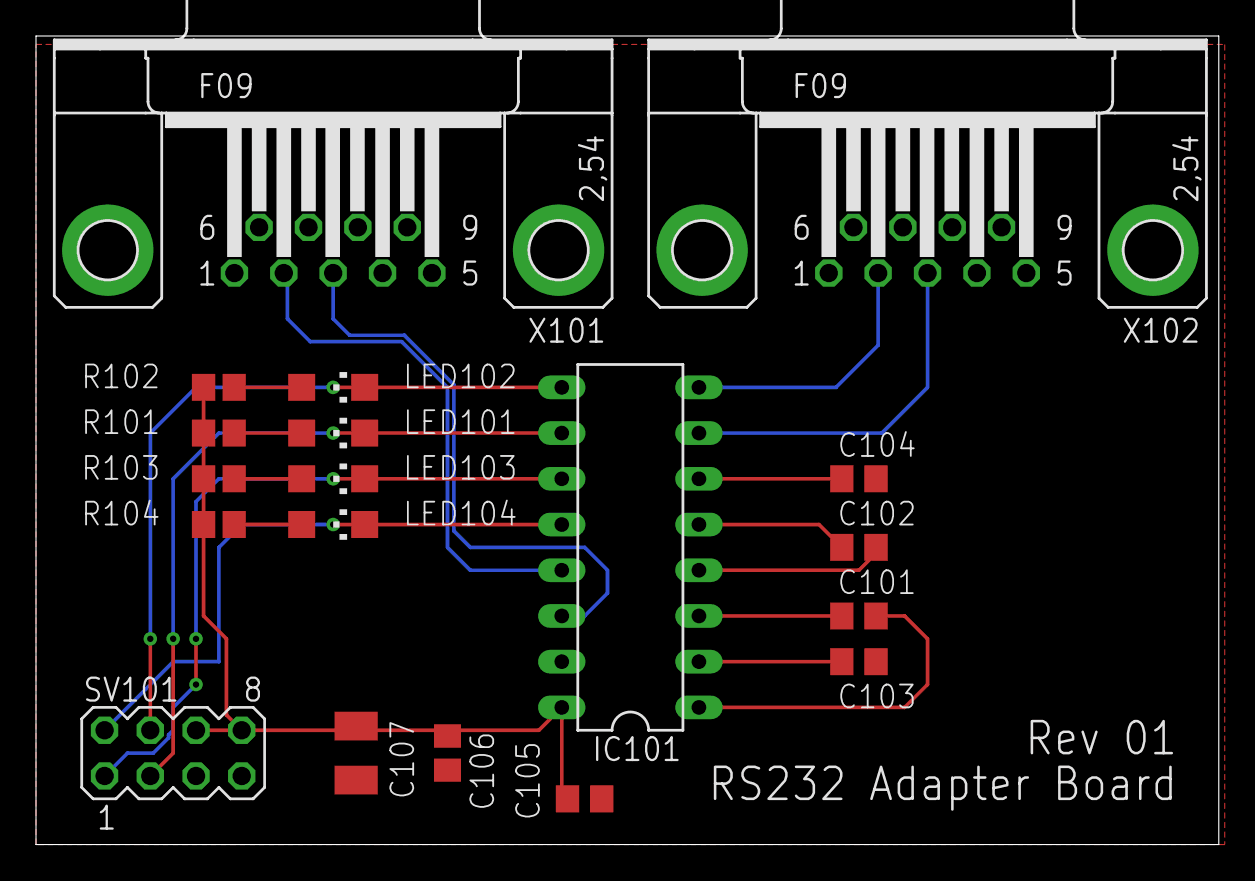
[picture p79: board uart_rs232_adapter.brd from above]

Board: 2 copper layers, 65.7 x 44.9 mm, 19 parts (0 on the bottom side), 20 nets.
