tristanseifert/68komputer-hw/cpu-68010/cpu-68010.brd

## EAGLE design cpu-68010/cpu-68010.brd (2018-12-12)

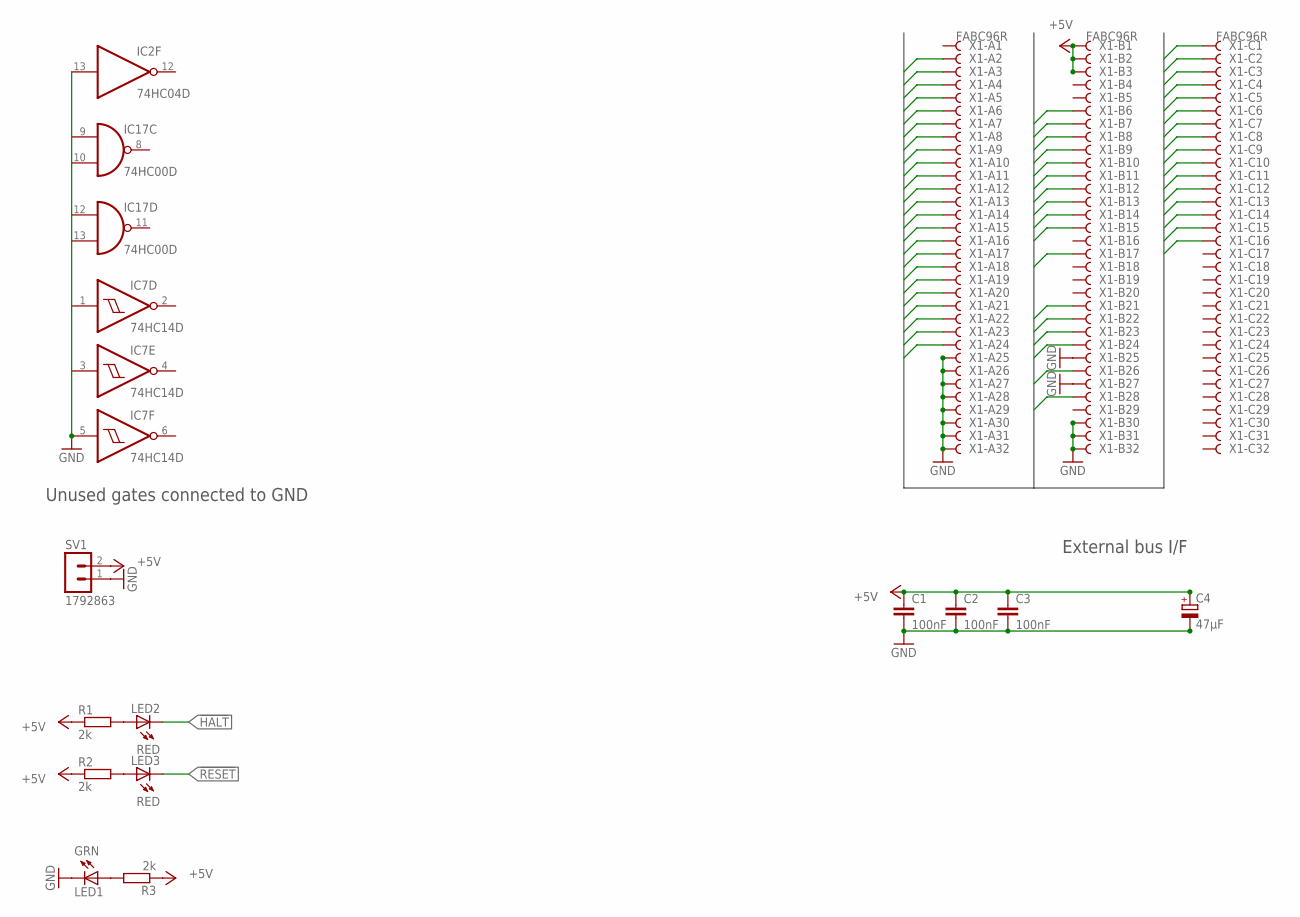
[picture p80: schematic cpu-68010.sch, sheet 1, External bus connection, power]

Parts:
C1, C2, C3: 100nF; C0805; MOUSER 710-885012207072
C4: 47µF; CT6032; MOUSER 581-TAJD476M016RNJV
IC2: 74HC04D; SO14
IC7: 74HC14D; SO14
IC17: 74HC00D; SO14
LED1: GRN; CHIPLED_1206; MOUSER 604-APTR3216SGC
LED2, LED3: RED; CHIPLED_1206; MOUSER 710-156120RS75300
R1, R2, R3: 2k; M0805; MOUSER 652-CR0805-FX6800GLF
SV1: 1792863
X1: FABC96R

Connections:
!AS: X1.B21; also elsewhere on the board
!BERR: X1.B9; also elsewhere on the board
!BG: X1.B14; also elsewhere on the board
!BGACK: X1.B15; also elsewhere on the board
!BR: X1.B13; also elsewhere on the board
!EXT_DTACK: X1.B28; also elsewhere on the board
!EXT_IRQ: X1.B17; also elsewhere on the board
!HALT: LED2.C, X1.B11; also elsewhere on the board
!LDS: X1.B24; also elsewhere on the board
!RESET: LED3.C, X1.B10; also elsewhere on the board
!UDS: X1.B23; also elsewhere on the board
!VPA: X1.B12; also elsewhere on the board
+5V: C1.1, C2.1, C3.1, C4.+, R1.1, R2.1, R3.1, SV1.2, X1.B1, X1.B2, X1.B3; also elsewhere on the board
A1: X1.A2; also elsewhere on the board
A2: X1.A3; also elsewhere on the board
A3: X1.A4; also elsewhere on the board
A4: X1.A5; also elsewhere on the board
A5: X1.A6; also elsewhere on the board
A6: X1.A7; also elsewhere on the board
A7: X1.A8; also elsewhere on the board
A8: X1.A9; also elsewhere on the board
A9: X1.A10; also elsewhere on the board
A10: X1.A11; also elsewhere on the board
A11: X1.A12; also elsewhere on the board
A12: X1.A13; also elsewhere on the board
A13: X1.A14; also elsewhere on the board
A14: X1.A15; also elsewhere on the board
A15: X1.A16; also elsewhere on the board
A16: X1.A17; also elsewhere on the board
A17: X1.A18; also elsewhere on the board
A18: X1.A19; also elsewhere on the board
A19: X1.A20; also elsewhere on the board
A20: X1.A21; also elsewhere on the board
A21: X1.A22; also elsewhere on the board
A22: X1.A23; also elsewhere on the board
A23: X1.A24; also elsewhere on the board
CLK: X1.B26; also elsewhere on the board
D0: X1.C1; also elsewhere on the board
D1: X1.C2; also elsewhere on the board
D2: X1.C3; also elsewhere on the board
D3: X1.C4; also elsewhere on the board
D4: X1.C5; also elsewhere on the board
D5: X1.C6; also elsewhere on the board
D6: X1.C7; also elsewhere on the board
D7: X1.C8; also elsewhere on the board
D8: X1.C9; also elsewhere on the board
D9: X1.C10; also elsewhere on the board
D10: X1.C11; also elsewhere on the board
D11: X1.C12; also elsewhere on the board
D12: X1.C13; also elsewhere on the board
D13: X1.C14; also elsewhere on the board
D14: X1.C15; also elsewhere on the board
D15: X1.C16; also elsewhere on the board
FC0: X1.B6; also elsewhere on the board
FC1: X1.B7; also elsewhere on the board
FC2: X1.B8; also elsewhere on the board
GND: C1.2, C2.2, C3.2, C4.-, IC2.13 (I), IC7.5 (I), LED1.C, SV1.1, X1.A25, X1.A26, X1.A27, X1.A28, X1.A29, X1.A30, X1.A31, X1.A32, X1.B25, X1.B27, X1.B30, X1.B31, X1.B32; also elsewhere on the board
unnamed: LED3.A, R2.2
unnamed: LED2.A, R1.2
unnamed: LED1.A, R3.2
R!W!: X1.B22; also elsewhere on the board

Notes on the sheet:
External bus I/F
Unused gates connected to GND
