tristanseifert/68komputer-hw/cpu-68010/cpu-68010.brd

## EAGLE design cpu-68010/cpu-68010.brd (continued)

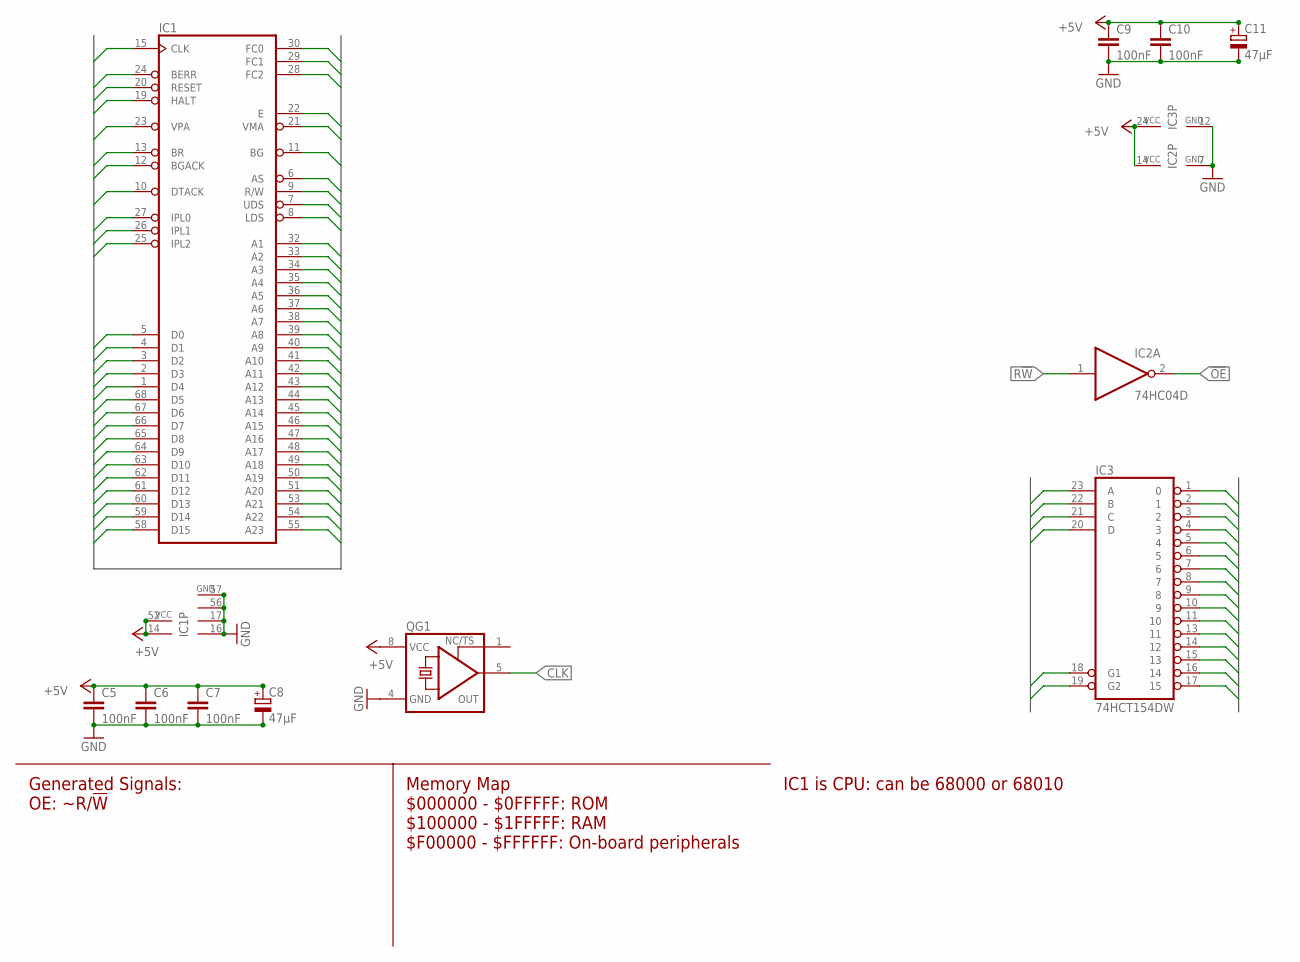
[picture p81: schematic cpu-68010.sch, sheet 2, CPU, address decoding]

Parts:
C5, C6, C7, C9, C10: 100nF; C0805; MOUSER 710-885012207072
C8, C11: 47µF; CT6032; MOUSER 581-TAJD476M016RNJV
IC1: MC68000FN-SOC; PLCC68SOCK
IC2: 74HC04D; SO14
IC3: 74HCT154DW; SO24W
QG1: XO-8; DIL08S

Connections:
!AS: IC1.6 (AS); also elsewhere on the board
!BERR: IC1.24 (BERR); also elsewhere on the board
!BG: IC1.11 (BG); also elsewhere on the board
!BGACK: IC1.12 (BGACK); also elsewhere on the board
!BR: IC1.13 (BR); also elsewhere on the board
!DTACK: IC1.10 (DTACK); also elsewhere on the board
!HALT: IC1.19 (HALT); also elsewhere on the board
!IPL0: IC1.27 (IPL0); also elsewhere on the board
!IPL1: IC1.26 (IPL1); also elsewhere on the board
!IPL2: IC1.25 (IPL2); also elsewhere on the board
!LDS: IC1.8 (LDS); also elsewhere on the board
!OE: IC2.2 (O); also elsewhere on the board
!REGION0: IC3.1 (0); also elsewhere on the board
!REGION1: IC3.2 (1); also elsewhere on the board
!REGION2: IC3.3 (2)
!REGION3: IC3.4 (3)
!REGION4: IC3.5 (4)
!REGION5: IC3.6 (5)
!REGION6: IC3.7 (6)
!REGION7: IC3.8 (7)
!REGION8: IC3.9 (8)
!REGION9: IC3.10 (9)
!REGION10: IC3.11 (10)
!REGION11: IC3.13 (11)
!REGION12: IC3.14 (12)
!REGION13: IC3.15 (13)
!REGION14: IC3.16 (14)
!REGION15: IC3.17 (15); also elsewhere on the board
!RESET: IC1.20 (RESET); also elsewhere on the board
!UDS: IC1.7 (UDS); also elsewhere on the board
!VMA: IC1.21 (VMA)
!VPA: IC1.23 (VPA); also elsewhere on the board
+5V: C5.1, C6.1, C7.1, C8.+, C9.1, C10.1, C11.+, IC1.14 (VCC), IC1.52 (VCC), IC2.14 (VCC), IC3.24 (VCC), QG1.8 (VCC); also elsewhere on the board
/AS: IC3.18 (G1), IC3.19 (G2)
A1: IC1.32 (A1); also elsewhere on the board
A2: IC1.33 (A2); also elsewhere on the board
A3: IC1.34 (A3); also elsewhere on the board
A4: IC1.35 (A4); also elsewhere on the board
A5: IC1.36 (A5); also elsewhere on the board
A6: IC1.37 (A6); also elsewhere on the board
A7: IC1.38 (A7); also elsewhere on the board
A8: IC1.39 (A8); also elsewhere on the board
A9: IC1.40 (A9); also elsewhere on the board
A10: IC1.41 (A10); also elsewhere on the board
A11: IC1.42 (A11); also elsewhere on the board
A12: IC1.43 (A12); also elsewhere on the board
A13: IC1.44 (A13); also elsewhere on the board
A14: IC1.45 (A14); also elsewhere on the board
A15: IC1.46 (A15); also elsewhere on the board
A16: IC1.47 (A16); also elsewhere on the board
A17: IC1.48 (A17); also elsewhere on the board
A18: IC1.49 (A18); also elsewhere on the board
A19: IC1.50 (A19); also elsewhere on the board
A20: IC1.51 (A20), IC3.23 (A); also elsewhere on the board
A21: IC1.53 (A21), IC3.22 (B); also elsewhere on the board
A22: IC1.54 (A22), IC3.21 (C); also elsewhere on the board
A23: IC1.55 (A23), IC3.20 (D); also elsewhere on the board
CLK: IC1.15 (CLK), QG1.5 (OUT); also elsewhere on the board
D0: IC1.5 (D0); also elsewhere on the board
D1: IC1.4 (D1); also elsewhere on the board
D2: IC1.3 (D2); also elsewhere on the board
D3: IC1.2 (D3); also elsewhere on the board
D4: IC1.1 (D4); also elsewhere on the board
D5: IC1.68 (D5); also elsewhere on the board
D6: IC1.67 (D6); also elsewhere on the board
D7: IC1.66 (D7); also elsewhere on the board
D8: IC1.65 (D8); also elsewhere on the board
D9: IC1.64 (D9); also elsewhere on the board
D10: IC1.63 (D10); also elsewhere on the board
D11: IC1.62 (D11); also elsewhere on the board
D12: IC1.61 (D12); also elsewhere on the board
D13: IC1.60 (D13); also elsewhere on the board
D14: IC1.59 (D14); also elsewhere on the board
D15: IC1.58 (D15); also elsewhere on the board
E: IC1.22 (E)
FC0: IC1.30 (FC0); also elsewhere on the board
FC1: IC1.29 (FC1); also elsewhere on the board
FC2: IC1.28 (FC2); also elsewhere on the board
GND: C5.2, C6.2, C7.2, C8.-, C9.2, C10.2, C11.-, IC1.16 (GND), IC1.17 (GND), IC1.56 (GND), IC1.57 (GND), IC2.7 (GND), IC3.12 (GND), QG1.4 (GND); also elsewhere on the board
R!W!: IC1.9 (R/W), IC2.1 (I); also elsewhere on the board

Notes on the sheet:
IC1 is CPU: can be 68000 or 68010
Memory Map $000000 - $0FFFFF: ROM $100000 - $1FFFFF: RAM $F00000 - $FFFFFF: On-board peripherals
Generated Signals: OE: ~R/!W

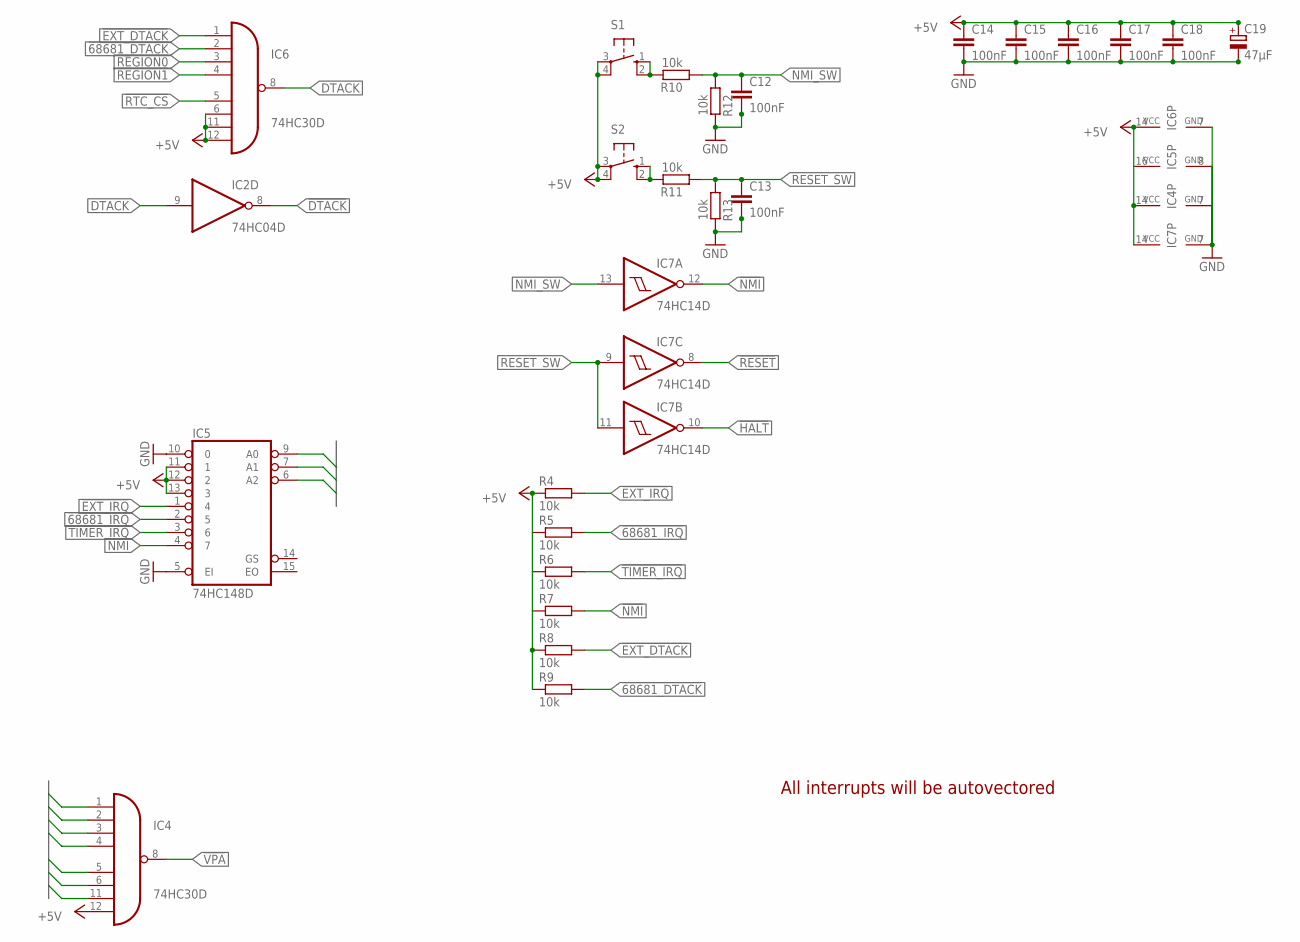
[picture p82: schematic cpu-68010.sch, sheet 3, DTACK and Interrupts]

Parts:
C12, C13, C14, C15, C16, C17, C18: 100nF; C0805; MOUSER 710-885012207072
C19: 47µF; CT6032; MOUSER 581-TAJD476M016RNJV
IC2: 74HC04D; SO14
IC4, IC6: 74HC30D; SO14
IC5: 74HC148D; SO16
IC7: 74HC14D; SO14
R4, R5, R6, R7, R8, R9, R10, R11, R12, R13: 10k; M0805; MOUSER 652-CR0805-FX6800GLF
S1, S2: 10-XX; B3F-10XX

Connections:
!68681_DTACK: IC6.2 (I1), R9.2; also elsewhere on the board
!68681_IRQ: IC5.2 (5), R5.2; also elsewhere on the board
!DTACK: IC2.8 (O); also elsewhere on the board
!EXT_DTACK: IC6.1 (I0), R8.2; also elsewhere on the board
!EXT_IRQ: IC5.1 (4), R4.2; also elsewhere on the board
!HALT: IC7.10 (O); also elsewhere on the board
!IPL0: IC5.9 (A0); also elsewhere on the board
!IPL1: IC5.7 (A1); also elsewhere on the board
!IPL2: IC5.6 (A2); also elsewhere on the board
!NMI: IC5.4 (7), IC7.12 (O), R7.2
!REGION0: IC6.3 (I2); also elsewhere on the board
!REGION1: IC6.4 (I3); also elsewhere on the board
!RESET: IC7.8 (O); also elsewhere on the board
!RTC_CS: IC6.5 (I4); also elsewhere on the board
!TIMER_IRQ: IC5.3 (6), R6.2
!VPA: IC4.8 (O); also elsewhere on the board
+5V: C14.1, C15.1, C16.1, C17.1, C18.1, C19.+, IC4.12 (I7), IC4.14 (VCC), IC5.11 (1), IC5.12 (2), IC5.13 (3), IC5.16 (VCC), IC6.6 (I5), IC6.11 (I6), IC6.12 (I7), IC6.14 (VCC), IC7.14 (VCC), R4.1, R8.1, R9.1, S1.3, S1.4 (P1), S2.3, S2.4 (P1); also elsewhere on the board
A16: IC4.4 (I3); also elsewhere on the board
A17: IC4.5 (I4); also elsewhere on the board
A18: IC4.6 (I5); also elsewhere on the board
A19: IC4.11 (I6); also elsewhere on the board
DTACK: IC2.9 (I), IC6.8 (O)
FC0: IC4.1 (I0); also elsewhere on the board
FC1: IC4.2 (I1); also elsewhere on the board
FC2: IC4.3 (I2); also elsewhere on the board
GND: C12.2, C13.2, C14.2, C15.2, C16.2, C17.2, C18.2, C19.-, IC4.7 (GND), IC5.5 (EI), IC5.8 (GND), IC5.10 (0), IC6.7 (GND), IC7.7 (GND), R12.2, R13.2; also elsewhere on the board
unnamed: R11.2, S2.1 (S), S2.2 (S1)
unnamed: R10.2, S1.1 (S), S1.2 (S1)
NMI_SW: C12.1, IC7.13 (I), R10.1, R12.1
RESET_SW: C13.1, IC7.9 (I), IC7.11 (I), R11.1, R13.1

Notes on the sheet:
All interrupts will be autovectored

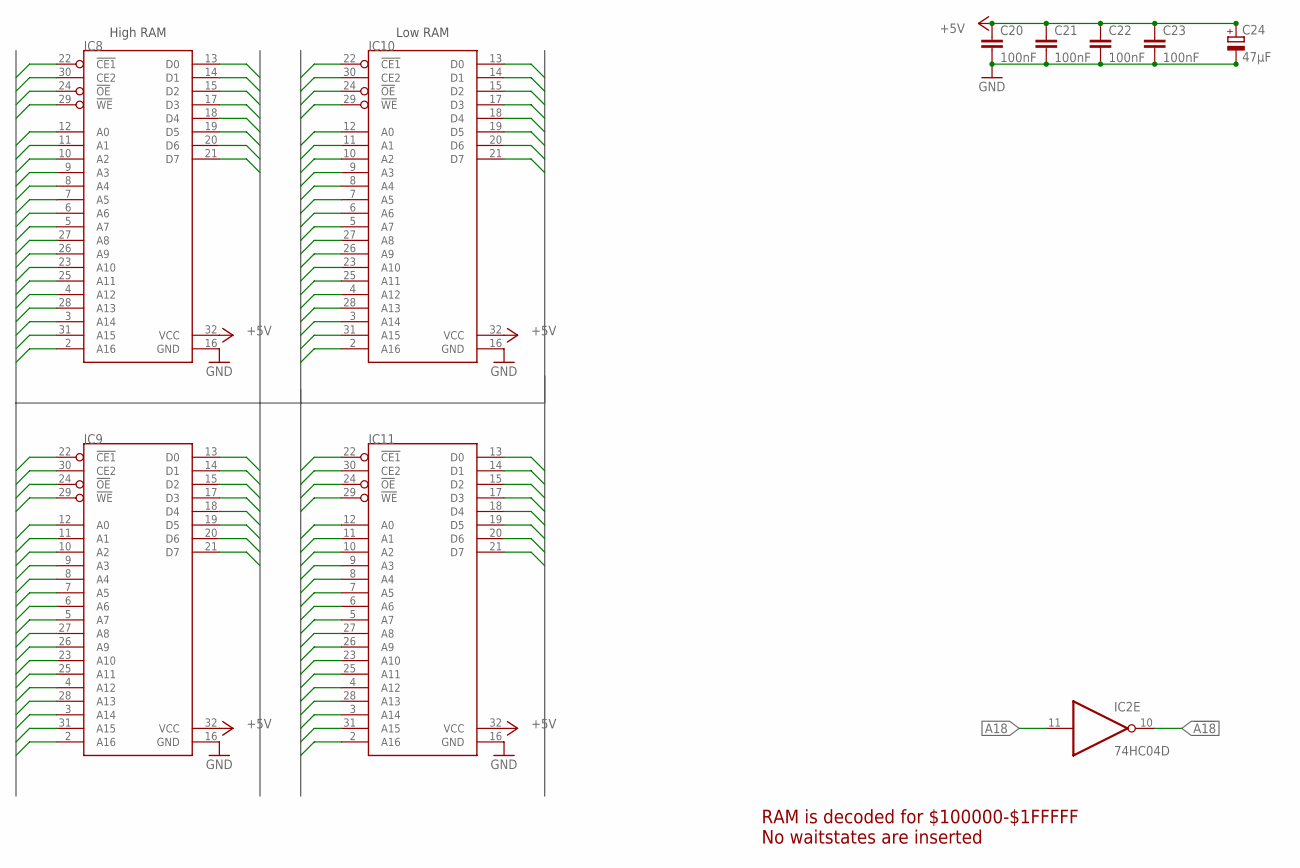
[picture p83: schematic cpu-68010.sch, sheet 4, Internal RAM]

Parts:
C20, C21, C22, C23: 100nF; C0805; MOUSER 710-885012207072
C24: 47µF; CT6032; MOUSER 581-TAJD476M016RNJV
IC2: 74HC04D; SO14
IC8, IC9, IC10, IC11: CY62128BSOIC32; SO32X

Connections:
!A18: IC2.10 (O), IC8.30 (CE2), IC9.30 (CE2), IC10.30 (CE2), IC11.30 (CE2)
!OE: IC8.24 (!OE), IC9.24 (!OE), IC10.24 (!OE), IC11.24 (!OE); also elsewhere on the board
!REGION1: IC8.22 (!CE1), IC9.22 (!CE1), IC10.22 (!CE1), IC11.22 (!CE1); also elsewhere on the board
+5V: C20.1, C21.1, C22.1, C23.1, C24.+, IC8.32 (VCC), IC9.32 (VCC), IC10.32 (VCC), IC11.32 (VCC); also elsewhere on the board
A1: IC8.12 (A0), IC9.12 (A0), IC10.12 (A0), IC11.12 (A0); also elsewhere on the board
A2: IC8.11 (A1), IC9.11 (A1), IC10.11 (A1), IC11.11 (A1); also elsewhere on the board
A3: IC8.10 (A2), IC9.10 (A2), IC10.10 (A2), IC11.10 (A2); also elsewhere on the board
A4: IC8.9 (A3), IC9.9 (A3), IC10.9 (A3), IC11.9 (A3); also elsewhere on the board
A5: IC8.8 (A4), IC9.8 (A4), IC10.8 (A4), IC11.8 (A4); also elsewhere on the board
A6: IC8.7 (A5), IC9.7 (A5), IC10.7 (A5), IC11.7 (A5); also elsewhere on the board
A7: IC8.6 (A6), IC9.6 (A6), IC10.6 (A6), IC11.6 (A6); also elsewhere on the board
A8: IC8.5 (A7), IC9.5 (A7), IC10.5 (A7), IC11.5 (A7); also elsewhere on the board
A9: IC8.27 (A8), IC9.27 (A8), IC10.27 (A8), IC11.27 (A8); also elsewhere on the board
A10: IC8.26 (A9), IC9.26 (A9), IC10.26 (A9), IC11.26 (A9); also elsewhere on the board
A11: IC8.23 (A10), IC9.23 (A10), IC10.23 (A10), IC11.23 (A10); also elsewhere on the board
A12: IC8.25 (A11), IC9.25 (A11), IC10.25 (A11), IC11.25 (A11); also elsewhere on the board
A13: IC8.4 (A12), IC9.4 (A12), IC10.4 (A12), IC11.4 (A12); also elsewhere on the board
A14: IC8.28 (A13), IC9.28 (A13), IC10.28 (A13), IC11.28 (A13); also elsewhere on the board
A15: IC8.3 (A14), IC9.3 (A14), IC10.3 (A14), IC11.3 (A14); also elsewhere on the board
A16: IC8.31 (A15), IC9.31 (A15), IC10.31 (A15), IC11.31 (A15); also elsewhere on the board
A17: IC8.2 (A16), IC9.2 (A16), IC10.2 (A16), IC11.2 (A16); also elsewhere on the board
A18: IC2.11 (I); also elsewhere on the board
D0: IC10.13 (D0), IC11.13 (D0); also elsewhere on the board
D1: IC10.14 (D1), IC11.14 (D1); also elsewhere on the board
D2: IC10.15 (D2), IC11.15 (D2); also elsewhere on the board
D3: IC10.17 (D3), IC11.17 (D3); also elsewhere on the board
D4: IC10.18 (D4), IC11.18 (D4); also elsewhere on the board
D5: IC10.19 (D5), IC11.19 (D5); also elsewhere on the board
D6: IC10.20 (D6), IC11.20 (D6); also elsewhere on the board
D7: IC10.21 (D7), IC11.21 (D7); also elsewhere on the board
D8: IC8.13 (D0), IC9.13 (D0); also elsewhere on the board
D9: IC8.14 (D1), IC9.14 (D1); also elsewhere on the board
D10: IC8.15 (D2), IC9.15 (D2); also elsewhere on the board
D11: IC8.17 (D3), IC9.17 (D3); also elsewhere on the board
D12: IC8.18 (D4), IC9.18 (D4); also elsewhere on the board
D13: IC8.19 (D5), IC9.19 (D5); also elsewhere on the board
D14: IC8.20 (D6), IC9.20 (D6); also elsewhere on the board
D15: IC8.21 (D7), IC9.21 (D7); also elsewhere on the board
GND: C20.2, C21.2, C22.2, C23.2, C24.-, IC8.16 (GND), IC9.16 (GND), IC10.16 (GND), IC11.16 (GND); also elsewhere on the board
R/!W!: IC8.29 (!WE), IC9.29 (!WE), IC10.29 (!WE), IC11.29 (!WE); also elsewhere on the board

Notes on the sheet:
RAM is decoded for $100000-$1FFFFF No waitstates are inserted
High RAM
Low RAM

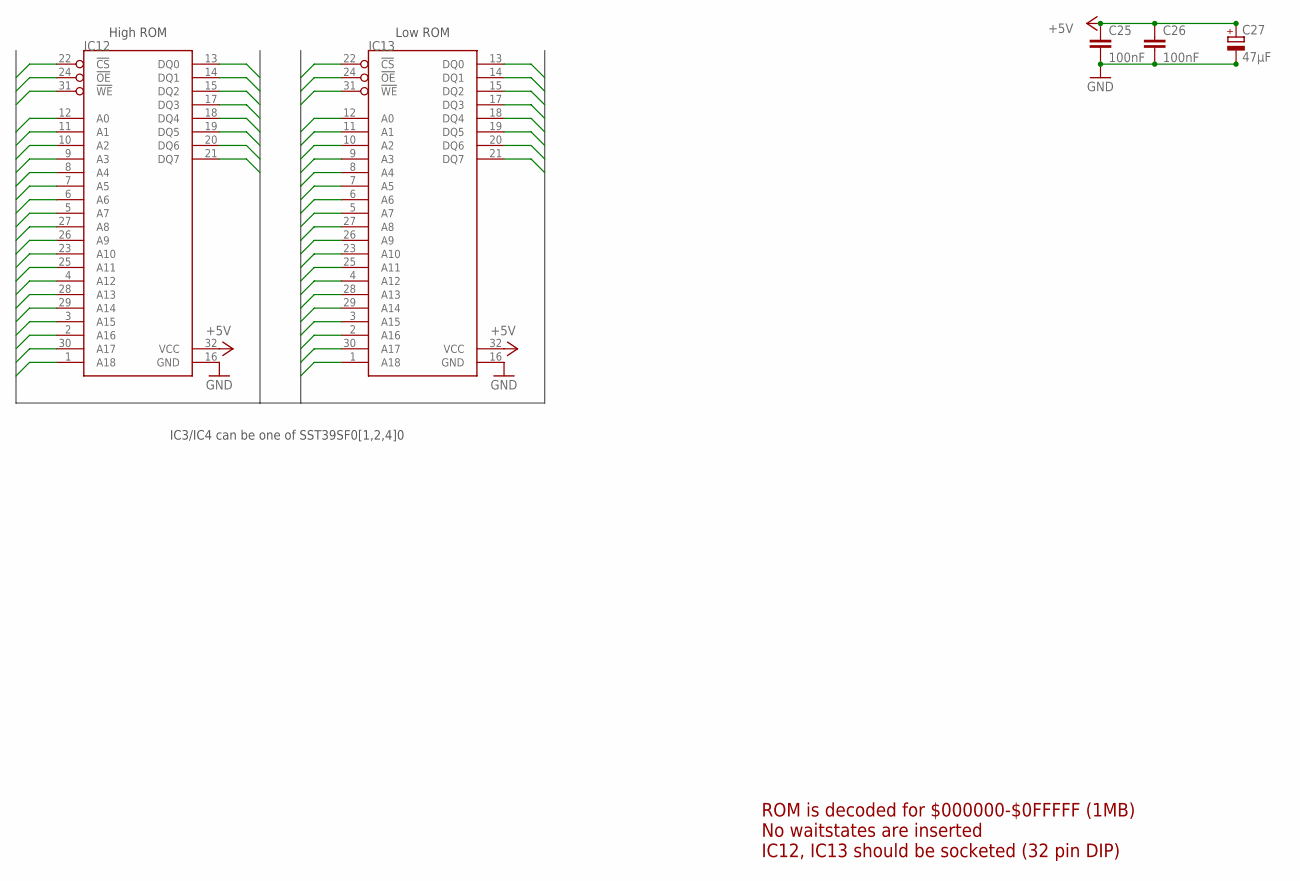
[picture p84: schematic cpu-68010.sch, sheet 5, System ROMs]

Parts:
C25, C26: 100nF; C0805; MOUSER 710-885012207072
C27: 47µF; CT6032; MOUSER 581-TAJD476M016RNJV
IC12, IC13: SST39SF0X0PDIP32; DIL32

Connections:
!OE: IC12.24 (!OE), IC13.24 (!OE); also elsewhere on the board
!REGION0: IC12.22 (!CS), IC13.22 (!CS); also elsewhere on the board
+5V: C25.1, C26.1, C27.+, IC12.32 (VCC), IC13.32 (VCC); also elsewhere on the board
A1: IC12.12 (A0), IC13.12 (A0); also elsewhere on the board
A2: IC12.11 (A1), IC13.11 (A1); also elsewhere on the board
A3: IC12.10 (A2), IC13.10 (A2); also elsewhere on the board
A4: IC12.9 (A3), IC13.9 (A3); also elsewhere on the board
A5: IC12.8 (A4), IC13.8 (A4); also elsewhere on the board
A6: IC12.7 (A5), IC13.7 (A5); also elsewhere on the board
A7: IC12.6 (A6), IC13.6 (A6); also elsewhere on the board
A8: IC12.5 (A7), IC13.5 (A7); also elsewhere on the board
A9: IC12.27 (A8), IC13.27 (A8); also elsewhere on the board
A10: IC12.26 (A9), IC13.26 (A9); also elsewhere on the board
A11: IC12.23 (A10), IC13.23 (A10); also elsewhere on the board
A12: IC12.25 (A11), IC13.25 (A11); also elsewhere on the board
A13: IC12.4 (A12), IC13.4 (A12); also elsewhere on the board
A14: IC12.28 (A13), IC13.28 (A13); also elsewhere on the board
A15: IC12.29 (A14), IC13.29 (A14); also elsewhere on the board
A16: IC12.3 (A15), IC13.3 (A15); also elsewhere on the board
A17: IC12.2 (A16), IC13.2 (A16); also elsewhere on the board
A18: IC12.30 (A17), IC13.30 (A17); also elsewhere on the board
A19: IC12.1 (A18), IC13.1 (A18); also elsewhere on the board
D0: IC13.13 (DQ0); also elsewhere on the board
D1: IC13.14 (DQ1); also elsewhere on the board
D2: IC13.15 (DQ2); also elsewhere on the board
D3: IC13.17 (DQ3); also elsewhere on the board
D4: IC13.18 (DQ4); also elsewhere on the board
D5: IC13.19 (DQ5); also elsewhere on the board
D6: IC13.20 (DQ6); also elsewhere on the board
D7: IC13.21 (DQ7); also elsewhere on the board
D8: IC12.13 (DQ0); also elsewhere on the board
D9: IC12.14 (DQ1); also elsewhere on the board
D10: IC12.15 (DQ2); also elsewhere on the board
D11: IC12.17 (DQ3); also elsewhere on the board
D12: IC12.18 (DQ4); also elsewhere on the board
D13: IC12.19 (DQ5); also elsewhere on the board
D14: IC12.20 (DQ6); also elsewhere on the board
D15: IC12.21 (DQ7); also elsewhere on the board
GND: C25.2, C26.2, C27.-, IC12.16 (GND), IC13.16 (GND); also elsewhere on the board
R/!W!: IC12.31 (!WE), IC13.31 (!WE); also elsewhere on the board

Notes on the sheet:
High ROM
Low ROM
ROM is decoded for $000000-$0FFFFF (1MB) No waitstates are inserted IC12, IC13 should be socketed (32 pin DIP)
IC3/IC4 can be one of SST39SF0[1,2,4]0

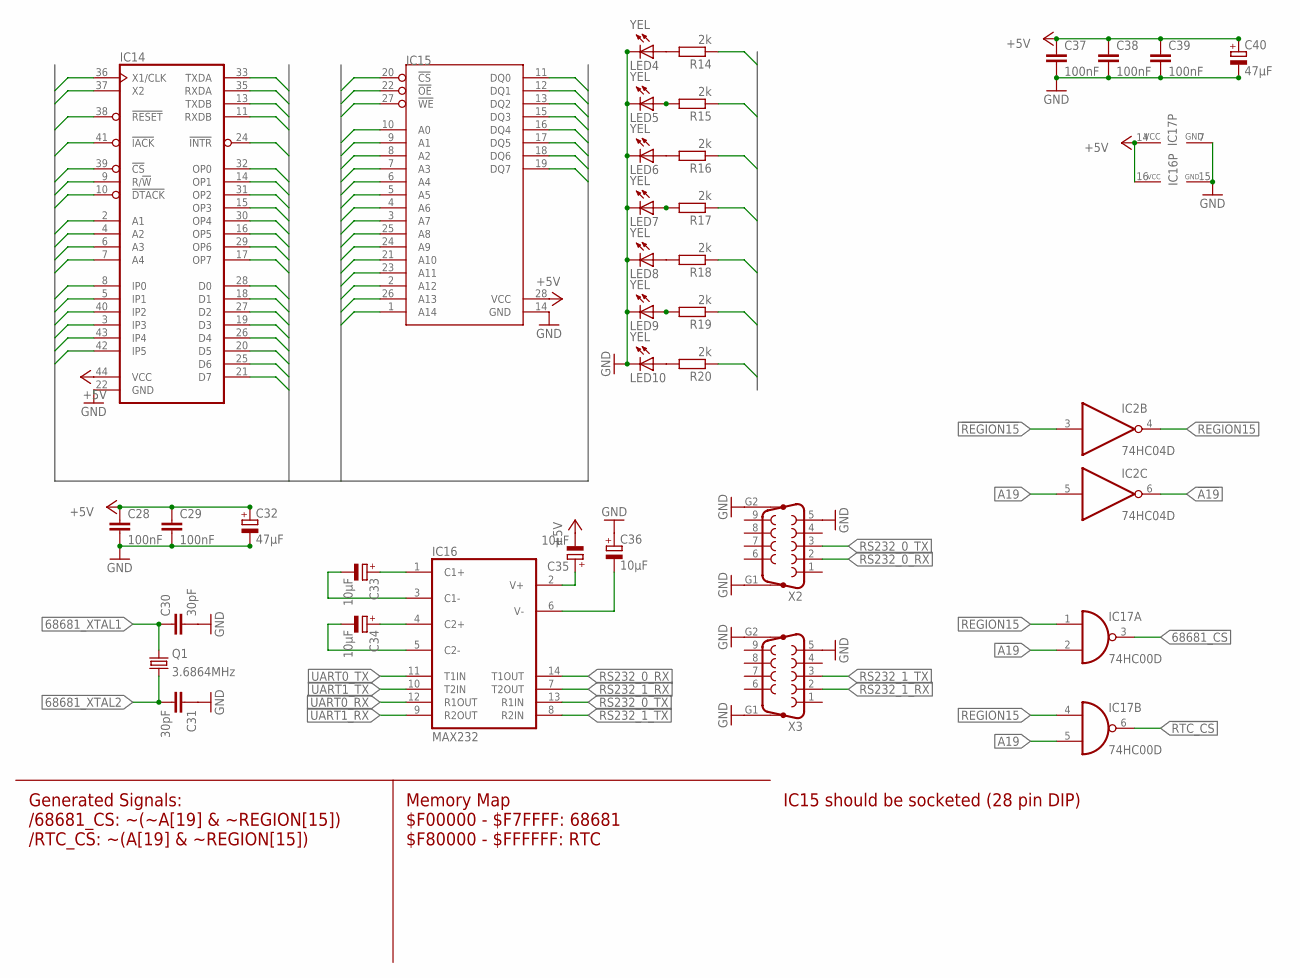
[picture p85: schematic cpu-68010.sch, sheet 6, Peripherals]

Parts:
C28, C29, C37, C38, C39: 100nF; C0805; MOUSER 710-885012207072
C30, C31: 30pF; C0805; MOUSER 710-885012207072
C32, C40: 47µF; CT6032; MOUSER 581-TAJD476M016RNJV
C33, C34, C35, C36: 10µF; E1,8-4
IC2: 74HC04D; SO14
IC14: MC68681PLCC44-SOCKET; PLCC-S44
IC15: DS1244EDIP-28; DIL28-6
IC16: MAX232; DIL16
IC17: 74HC00D; SO14
LED4, LED5, LED6, LED7, LED8, LED9, LED10: YEL; CHIPLED_1206; MOUSER 710-156120YS75300
Q1: 3.6864MHz; HC49/S
R14, R15, R16, R17, R18, R19, R20: 2k; M0805; MOUSER 652-CR0805-FX6800GLF
X2, X3: F09HP

Connections:
68681_XTAL1: C30.1, IC14.36 (X1/CLK), Q1.2
68681_XTAL2: C31.2, IC14.37 (X2), Q1.1
!68681_CS: IC14.39 (!CS), IC17.3 (O)
!68681_DTACK: IC14.10 (!DTACK); also elsewhere on the board
!68681_IRQ: IC14.24 (!INTR); also elsewhere on the board
!68681_IRQACK: IC14.41 (!IACK)
!A19: IC2.6 (O), IC17.2 (I1)
!OE: IC15.22 (!OE); also elsewhere on the board
!REGION15: IC2.3 (I); also elsewhere on the board
!RESET: IC14.38 (!RESET); also elsewhere on the board
!RTC_CS: IC15.20 (!CS), IC17.6 (O); also elsewhere on the board
+5V: C28.1, C29.1, C32.+, C35.-, C37.1, C38.1, C39.1, C40.+, IC14.44 (VCC), IC15.28 (VCC), IC16.16 (VCC), IC17.14 (VCC); also elsewhere on the board
A1: IC14.2 (A1), IC15.10 (A0); also elsewhere on the board
A2: IC14.4 (A2), IC15.9 (A1); also elsewhere on the board
A3: IC14.6 (A3), IC15.8 (A2); also elsewhere on the board
A4: IC14.7 (A4), IC15.7 (A3); also elsewhere on the board
A5: IC15.6 (A4); also elsewhere on the board
A6: IC15.5 (A5); also elsewhere on the board
A7: IC15.4 (A6); also elsewhere on the board
A8: IC15.3 (A7); also elsewhere on the board
A9: IC15.25 (A8); also elsewhere on the board
A10: IC15.24 (A9); also elsewhere on the board
A11: IC15.21 (A10); also elsewhere on the board
A12: IC15.23 (A11); also elsewhere on the board
A13: IC15.2 (A12); also elsewhere on the board
A14: IC15.26 (A13); also elsewhere on the board
A15: IC15.1 (A14); also elsewhere on the board
A19: IC2.5 (I), IC17.5 (I1); also elsewhere on the board
D0: IC14.28 (D0), IC15.11 (DQ0); also elsewhere on the board
D1: IC14.18 (D1), IC15.12 (DQ1); also elsewhere on the board
D2: IC14.27 (D2), IC15.13 (DQ2); also elsewhere on the board
D3: IC14.19 (D3), IC15.15 (DQ3); also elsewhere on the board
D4: IC14.26 (D4), IC15.16 (DQ4); also elsewhere on the board
D5: IC14.20 (D5), IC15.17 (DQ5); also elsewhere on the board
D6: IC14.25 (D6), IC15.18 (DQ6); also elsewhere on the board
D7: IC14.21 (D7), IC15.19 (DQ7); also elsewhere on the board
GND: C28.2, C29.2, C30.2, C31.1, C32.-, C36.+, C37.2, C38.2, C39.2, C40.-, IC14.22 (GND), IC15.14 (GND), IC16.15 (GND), IC17.7 (GND), LED4.C, LED5.C, LED6.C, LED7.C, LED8.C, LED9.C, LED10.C, X2.5, X2.G1, X2.G2, X3.5, X3.G1, X3.G2; also elsewhere on the board
GPIO_IN0: IC14.8 (IP0)
GPIO_IN1: IC14.5 (IP1)
GPIO_IN2: IC14.40 (IP2)
GPIO_IN3: IC14.3 (IP3)
GPIO_IN4: IC14.43 (IP4)
GPIO_IN5: IC14.42 (IP5)
GPIO_OUT0: IC14.32 (OP0), R14.1
GPIO_OUT1: IC14.14 (OP1), R15.1
GPIO_OUT2: IC14.15 (OP3), R16.1
GPIO_OUT3: IC14.30 (OP4), R17.1
GPIO_OUT4: IC14.16 (OP5), R18.1
GPIO_OUT5: IC14.29 (OP6), R19.1
GPIO_OUT6: IC14.17 (OP7), R20.1
unnamed: C35.+, IC16.2 (V+)
unnamed: C36.-, IC16.6 (V-)
unnamed: C33.+, IC16.1 (C1+)
unnamed: C34.+, IC16.4 (C2+)
unnamed: C33.-, IC16.3 (C1-)
unnamed: C34.-, IC16.5 (C2-)
unnamed: LED9.A, R19.2
unnamed: LED8.A, R18.2
unnamed: LED7.A, R17.2
unnamed: LED6.A, R16.2
unnamed: LED5.A, R15.2
unnamed: LED4.A, R14.2
unnamed: LED10.A, R20.2
R/!W!: IC14.9 (R/!W), IC15.27 (!WE); also elsewhere on the board
REGION15: IC2.4 (O), IC17.1 (I0), IC17.4 (I0)
RS232_0_RX: IC16.14 (T1OUT), X2.2
RS232_0_TX: IC16.13 (R1IN), X2.3
RS232_1_RX: IC16.7 (T2OUT), X3.2
RS232_1_TX: IC16.8 (R2IN), X3.3
TIMER_CLK: IC14.31 (OP2)
UART0_RX: IC14.35 (RXDA), IC16.12 (R1OUT)
UART0_TX: IC14.33 (TXDA), IC16.11 (T1IN)
UART1_RX: IC14.11 (RXDB), IC16.9 (R2OUT)
UART1_TX: IC14.13 (TXDB), IC16.10 (T2IN)

Notes on the sheet:
Memory Map $F00000 - $F7FFFF: 68681 $F80000 - $FFFFFF: RTC
Generated Signals: /68681_CS: ~(~A[19] & ~REGION[15]) /RTC_CS: ~(A[19] & ~REGION[15])
IC15 should be socketed (28 pin DIP)

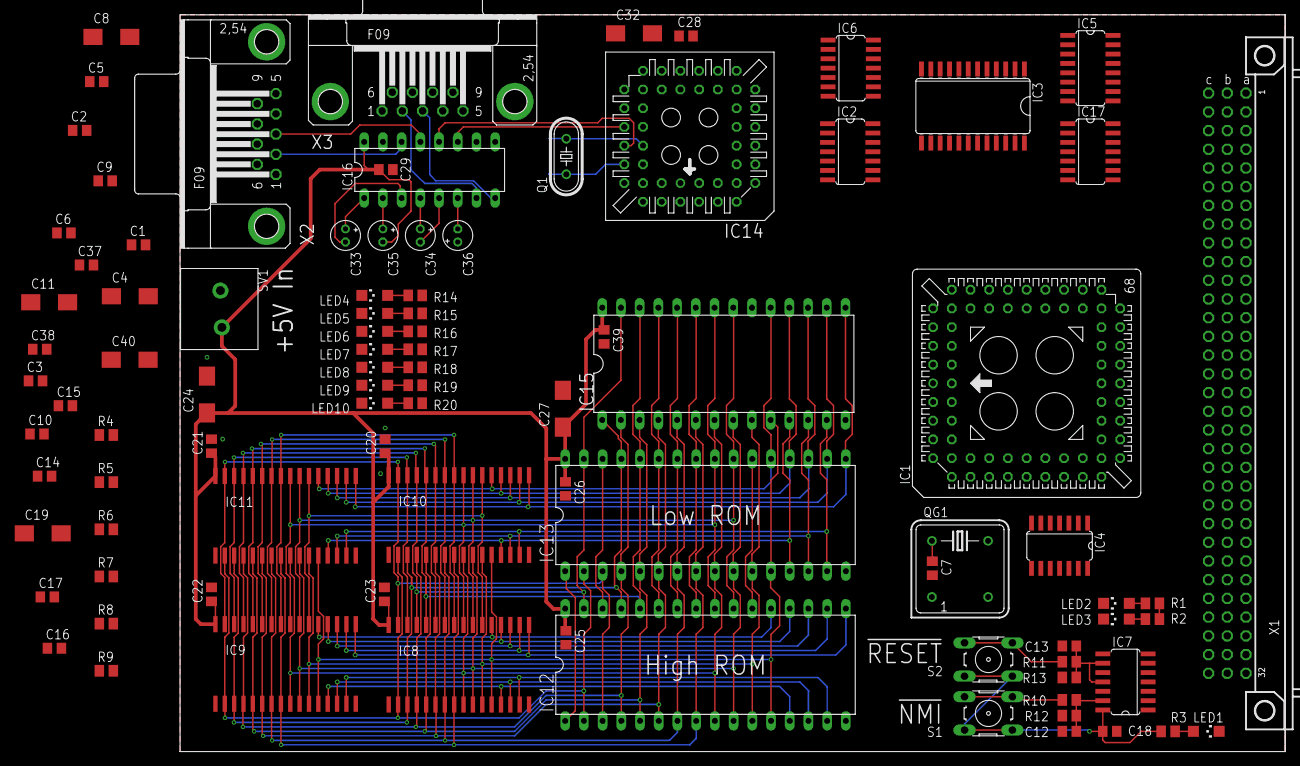
[picture p86: board cpu-68010.brd from above]

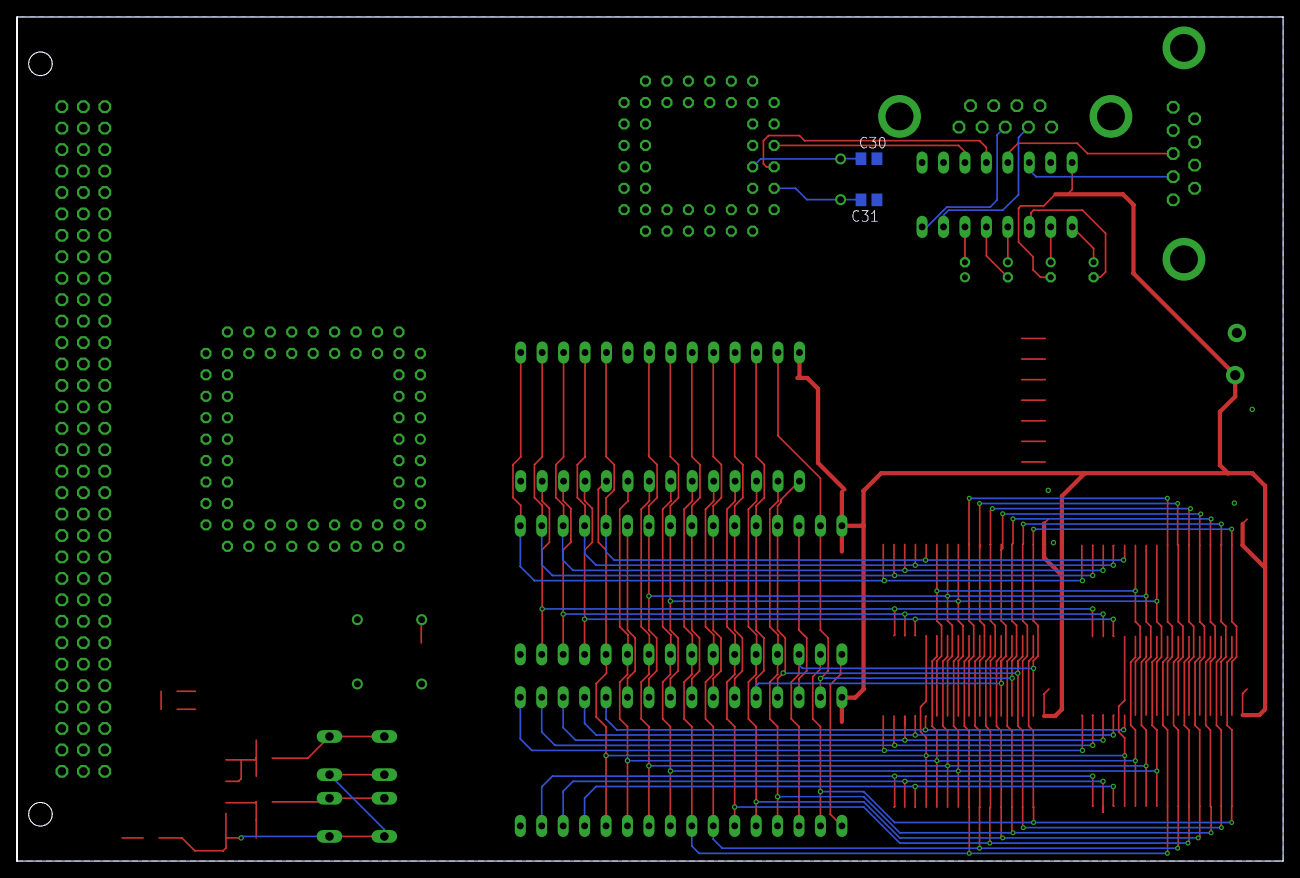
[picture p87: board cpu-68010.brd from below]

Board: 2 copper layers, 150.0 x 100.0 mm, 95 parts (2 on the bottom side), 115 nets.
